Kampi/KiCad/3D/Coilcraft/XFL4020.stp

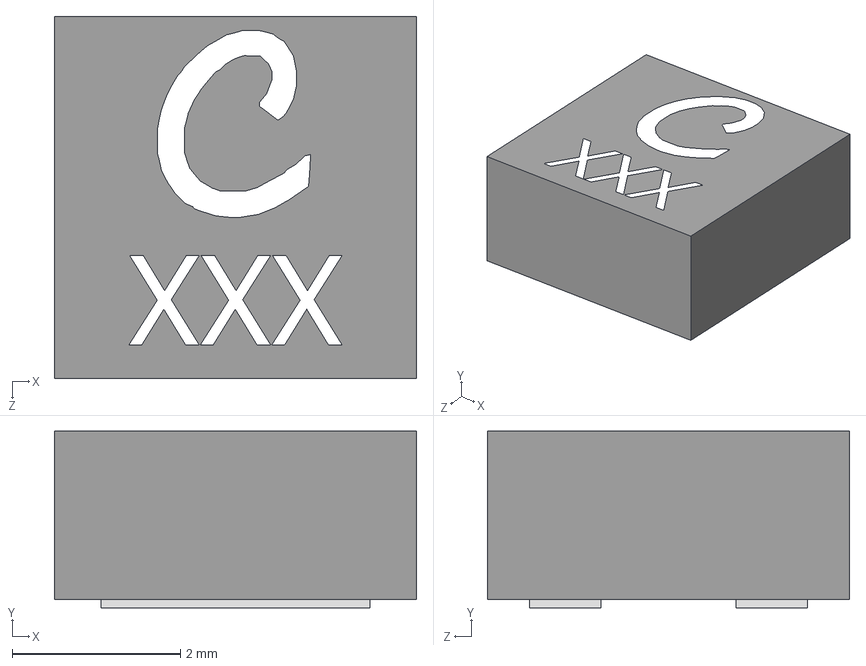
[picture p15: CAD file, 2021-03-04]
3D/Coilcraft/XFL4020.stp
4.30 x 2.10 x 4.30 mm
