Kampi/KiCad/3D/Connector_254/preci-dip/8fm-38-0006-02-146.stp

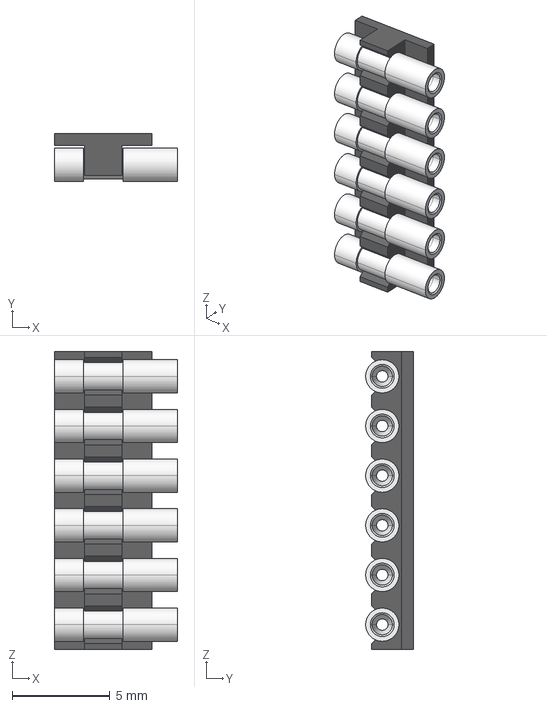
[picture p16: CAD file, 2020-06-16]
3D/Connector_254/preci-dip/8fm-38-0006-02-146.stp
6.30 x 2.44 x 15.2 mm
