Kampi/KiCad/3D/Connector_Audio/QingPu/PJ398SM_S_pin_centered.stp

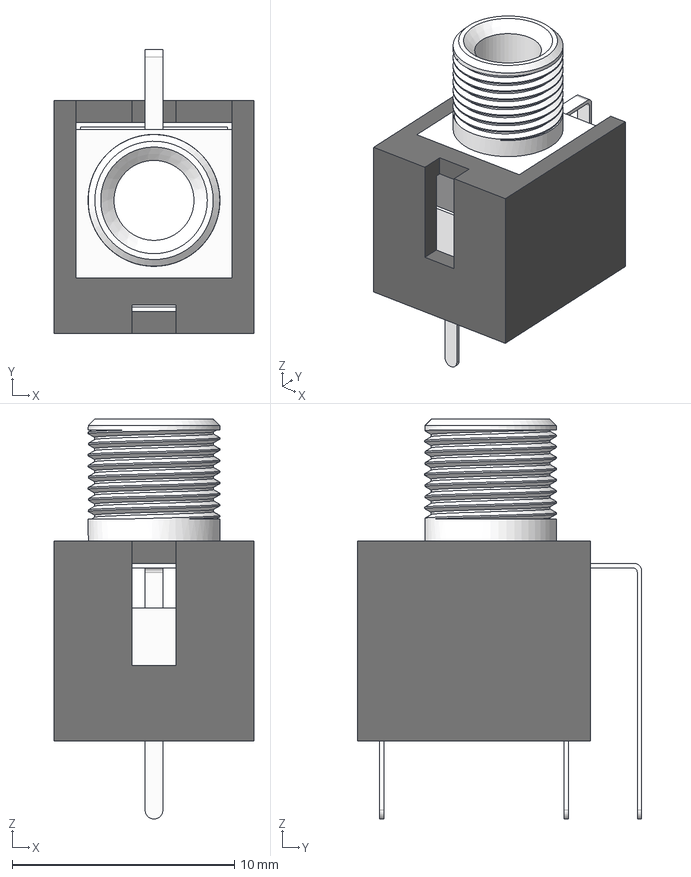
[picture p17: CAD file, 2020-06-21]
3D/Connector_Audio/QingPu/PJ398SM_S_pin_centered.stp
9.00 x 12.8 x 18.0 mm
