Kampi/KiCad/3D/Connector_Card/Hirose/DM3AT-SF-PEJM5.stp

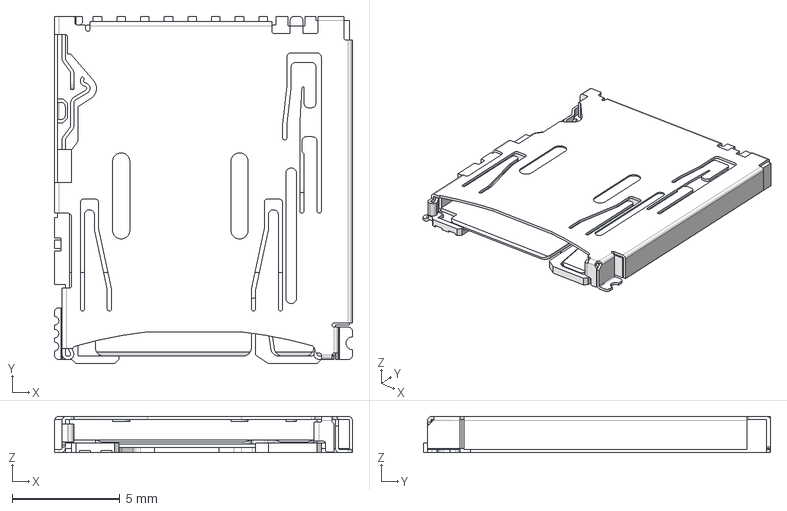
[picture p18: CAD file, 2020-09-08]
3D/Connector_Card/Hirose/DM3AT-SF-PEJM5.stp
13.8 x 16.2 x 1.68 mm
