Kampi/KiCad/3D/Connector_CUI/CUI_DEVICES_UJC-HP-3-SMT-TR.stp

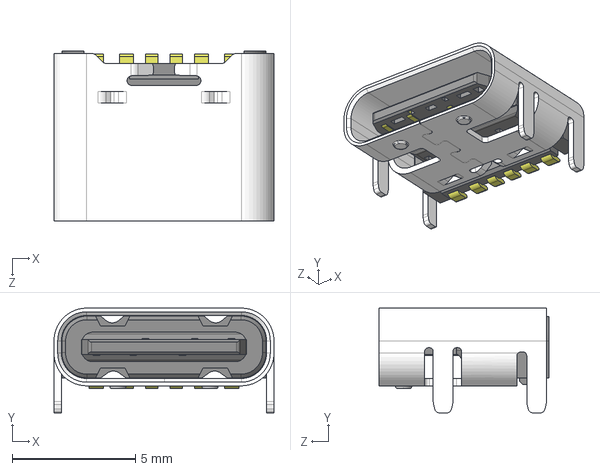
[picture p19: CAD file, 2020-06-03]
3D/Connector_CUI/CUI_DEVICES_UJC-HP-3-SMT-TR.stp
8.94 x 4.26 x 6.90 mm
