Kampi/KiCad/3D/Connector_IDC/Socket Male 10pin Straight THT Goldplated 2_54mm.stp

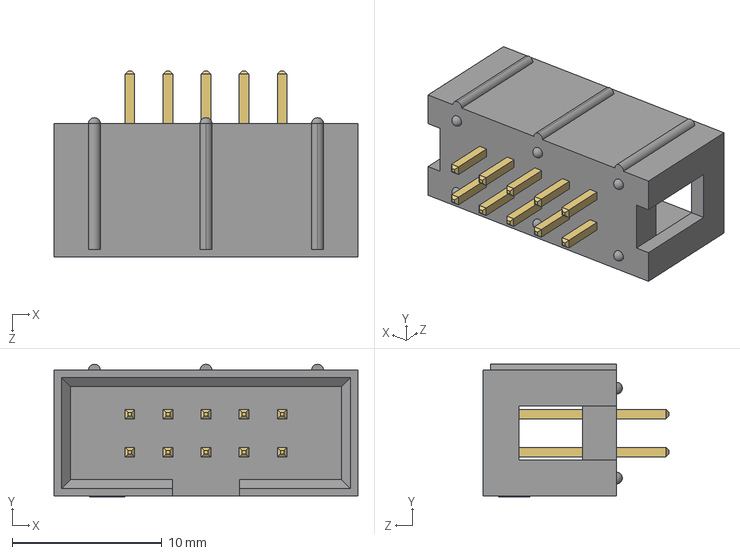
[picture p20: CAD file, 2020-06-20]
3D/Connector_IDC/Socket Male 10pin Straight THT Goldplated 2_54mm.stp
20.3 x 8.85 x 12.4 mm
