Kampi/KiCad/3D/Connector_JST/S6B-PH-SM4-TB.stp

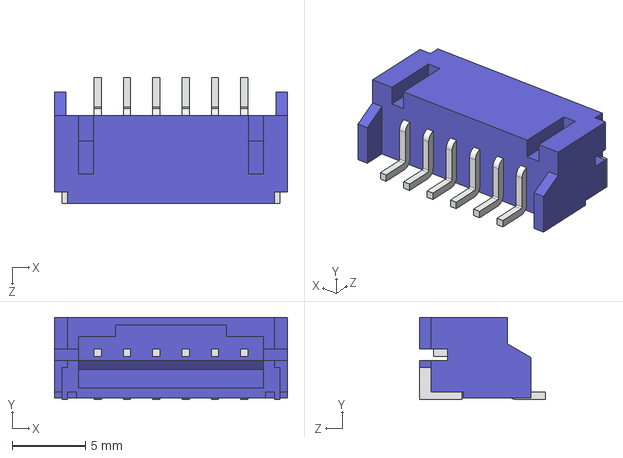
[picture p21: CAD file, 2022-03-19]
3D/Connector_JST/S6B-PH-SM4-TB.stp
15.9 x 5.60 x 8.60 mm
