Kampi/KiCad/3D/Connector_MiniDIN/TE Connectivity/c-5749231-1-o-3d.stp

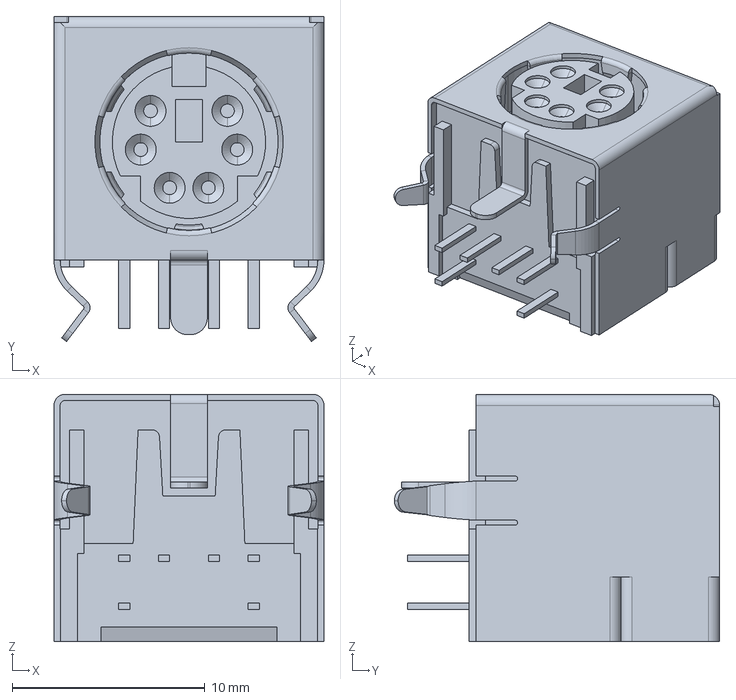
[picture p22: CAD file, 2019-10-17]
3D/Connector_MiniDIN/TE Connectivity/c-5749231-1-o-3d.stp
14.0 x 16.9 x 12.8 mm
