Kampi/KiCad/3D/Connector_Phoenix/PhoenixContact_MPT_0,5_4-4-2,54.stp

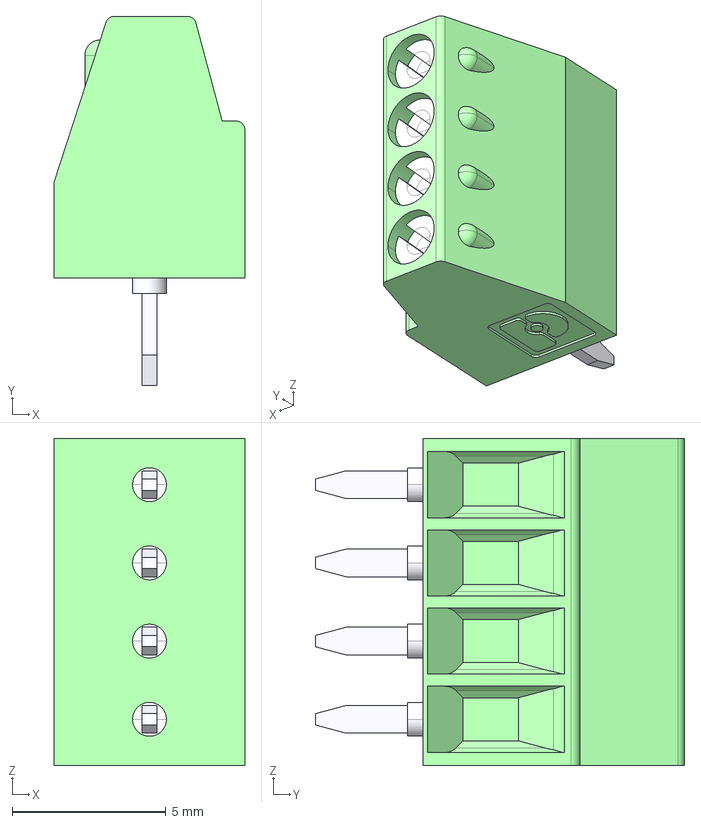
[picture p23: CAD file, 2020-06-03]
3D/Connector_Phoenix/PhoenixContact_MPT_0,5_4-4-2,54.stp
6.20 x 12.0 x 10.6 mm
