Kampi/KiCad/3D/Connector_USB/GCT/USB4110GFA.stp

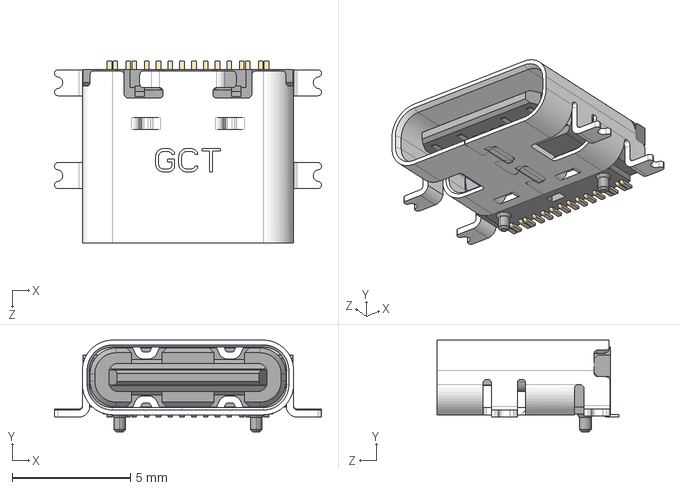
[picture p24: CAD file, 2026-01-24]
3D/Connector_USB/GCT/USB4110GFA.stp
11.3 x 3.89 x 7.70 mm
