Kampi/KiCad/3D/Connector_USB/TE Connectivity/c-292304-2-b-3d.stp

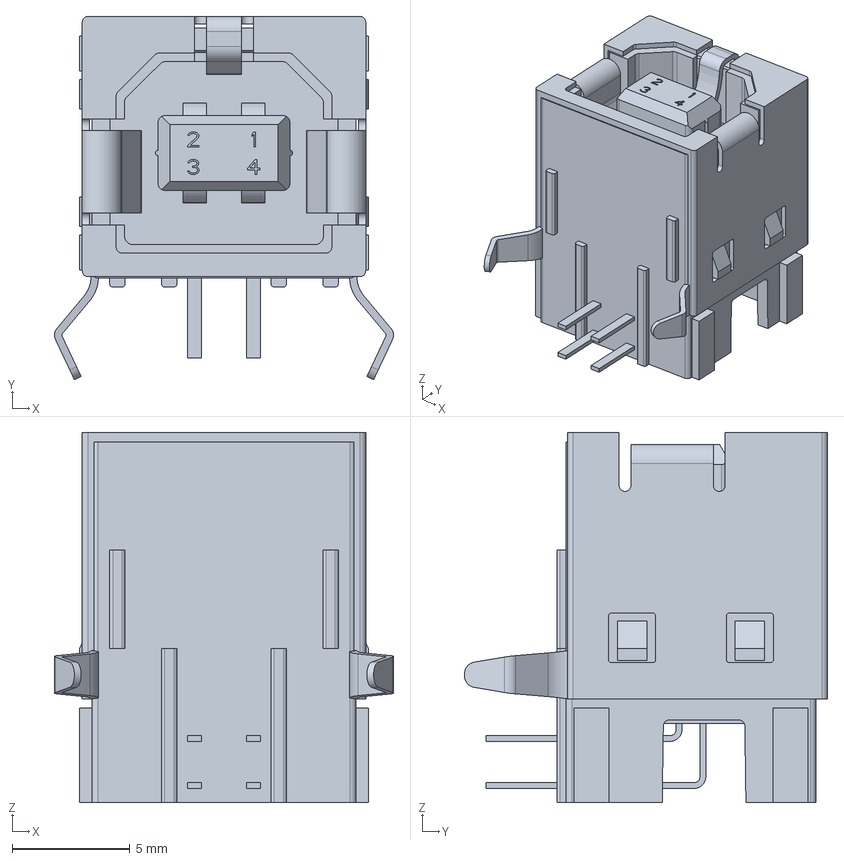
[picture p25: CAD file, 2019-10-16]
3D/Connector_USB/TE Connectivity/c-292304-2-b-3d.stp
14.4 x 15.4 x 15.7 mm
