Kampi/KiCad/3D/Cree/XLamp XP-G3.stp

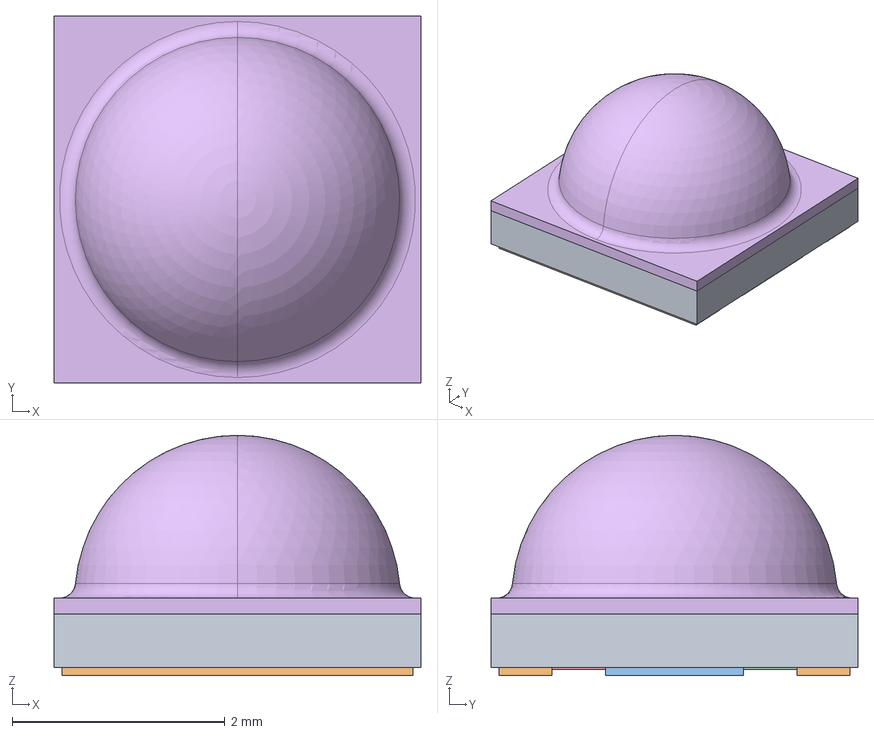
[picture p26: CAD file, 2026-01-24]
3D/Cree/XLamp XP-G3.stp
3.45 x 3.45 x 2.26 mm
2500-00565C
2500-00565C-BT
2500-00565C-SBN
2500-00565C-SB
2610-00066-DOME
