Kampi/KiCad/3D/Crystal/1612.stp

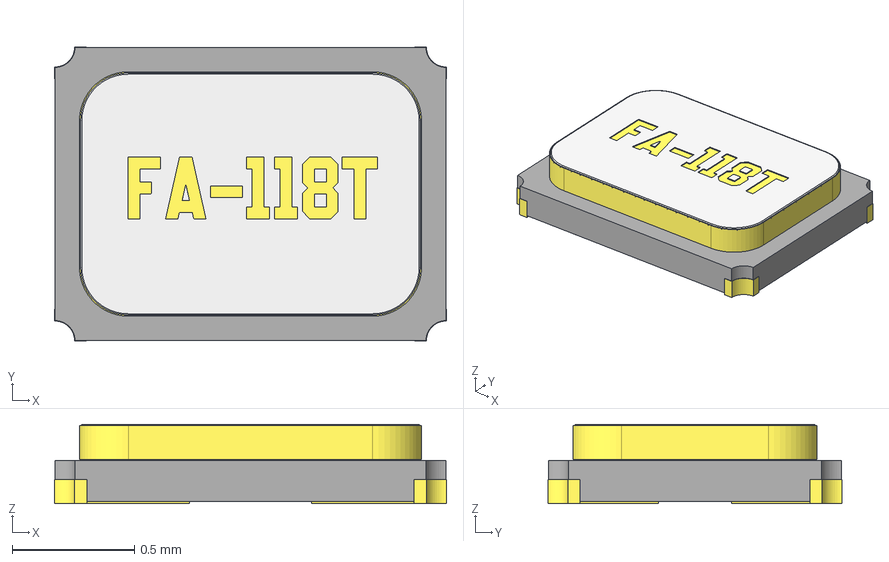
[picture p27: CAD file, 2024-10-24]
3D/Crystal/1612.stp
1.60 x 1.20 x 0.325 mm
TxT
Pin
Pin001
Pin002
Pin003
Pin004
