Kampi/KiCad/3D/Crystal/Abracon/ABS07L.stp

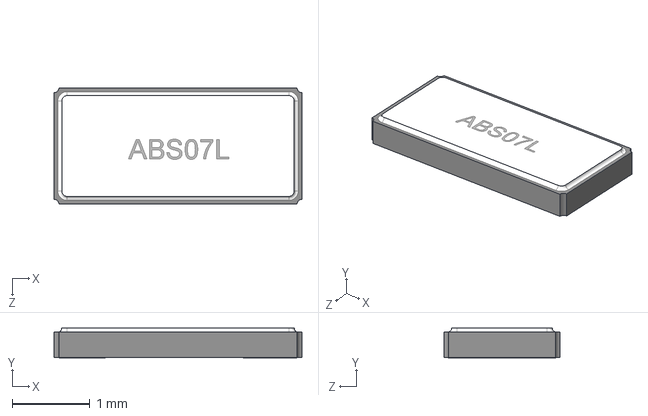
[picture p28: CAD file, 2020-09-11]
3D/Crystal/Abracon/ABS07L.stp
3.20 x 0.383 x 1.50 mm
