Kampi/KiCad/3D/CUI Devices/CMT-322-65-SMT-TR.stp

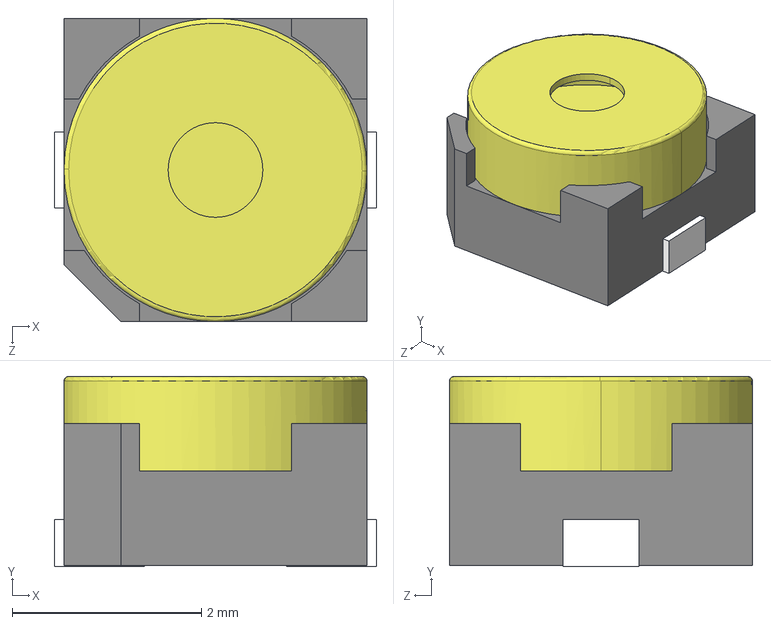
[picture p29: CAD file, 2023-12-06]
3D/CUI Devices/CMT-322-65-SMT-TR.stp
3.40 x 2.01 x 3.20 mm
