Kampi/KiCad/3D/DevBoards/Digilent/PmodOLED.stp

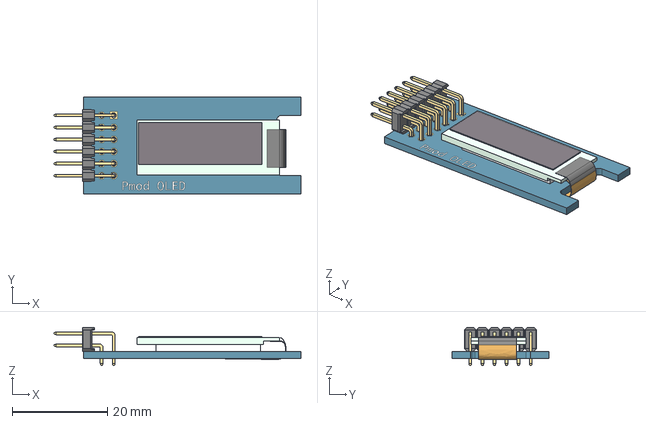
[picture p30: CAD file, 2020-05-07]
3D/DevBoards/Digilent/PmodOLED.stp
51.9 x 20.3 x 8.08 mm
