Kampi/KiCad/3D/DevBoards/Particle/Xenon.stp

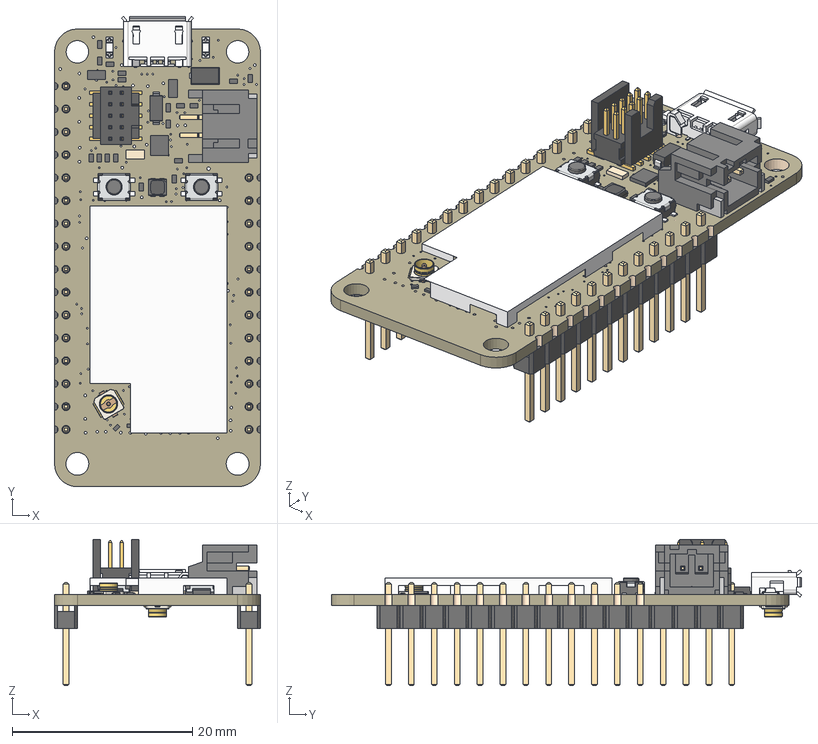
[picture p31: CAD file, 2020-05-14]
3D/DevBoards/Particle/Xenon.stp
22.9 x 52.2 x 16.3 mm
Board
_FTSH_105_01_L_DV_K_body_2
_FTSH_105_01_L_DV_K_pins1_4
_FTSH_105_01_L_DV_K_pins2_6
pin x 2
mount x 2
housing
switch v1 x 2
LED_CLVBA-FKA v1
uFL x 2
MBR120
MICRO_led (1) x 2
microUSB
DO-220AA SMP v1
0402-resistor v2 x 18
xenon-rf-shield-v002 v6
capacitor-smd v2
capacitor-smd v2 (1) x 2
ic
0402-resistor v2 (1) x 2
spacer (1) x 16
pin (1) x 16
spacer (1) (1) x 12
pin (1) (1) x 12
