Kampi/KiCad/3D/Display/LCD-320x240.step

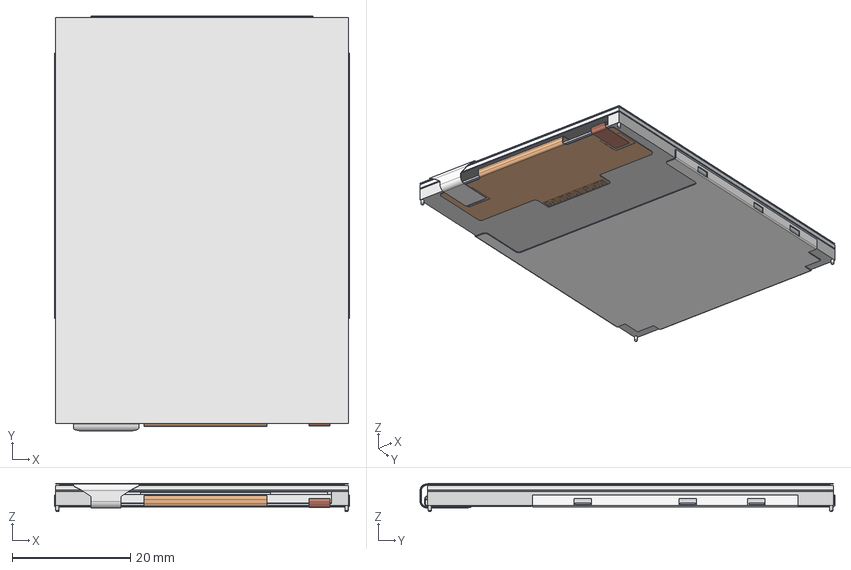
[picture p32: CAD file, 2026-01-24]
3D/Display/LCD-320x240.step
50.1 x 70.3 x 4.77 mm
frame
metal bandage
light_shelf
main_shelf
tft_matrix
tft_board
screen_film
screen_glass
touch_routs
touch_protect
touch_cable_contacts
touch_cable_film
