Kampi/KiCad/3D/Display/SevenSegment/Kingbright/SA23-11.stp

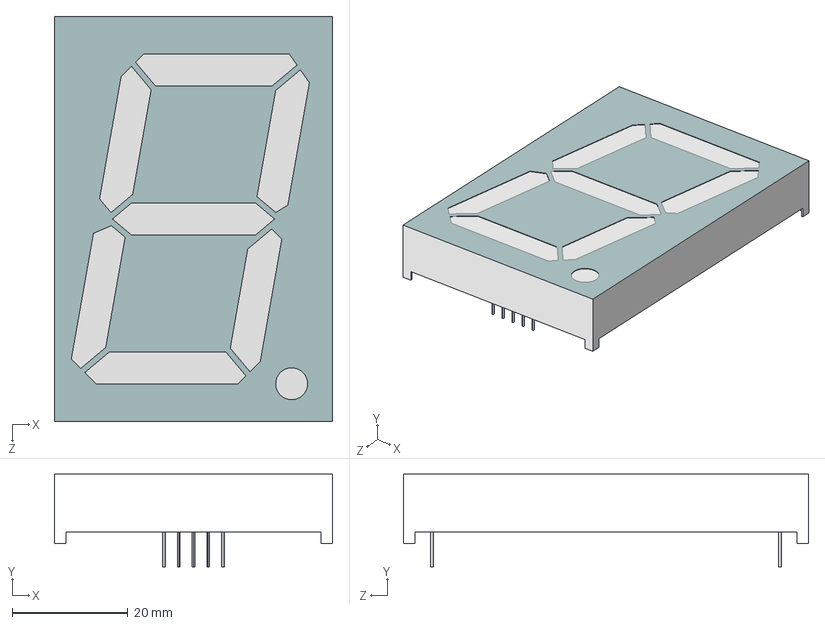
[picture p33: CAD file, 2020-06-30]
3D/Display/SevenSegment/Kingbright/SA23-11.stp
48.0 x 16.0 x 70.0 mm
