Kampi/KiCad/3D/E-Switch/TL3305.stp

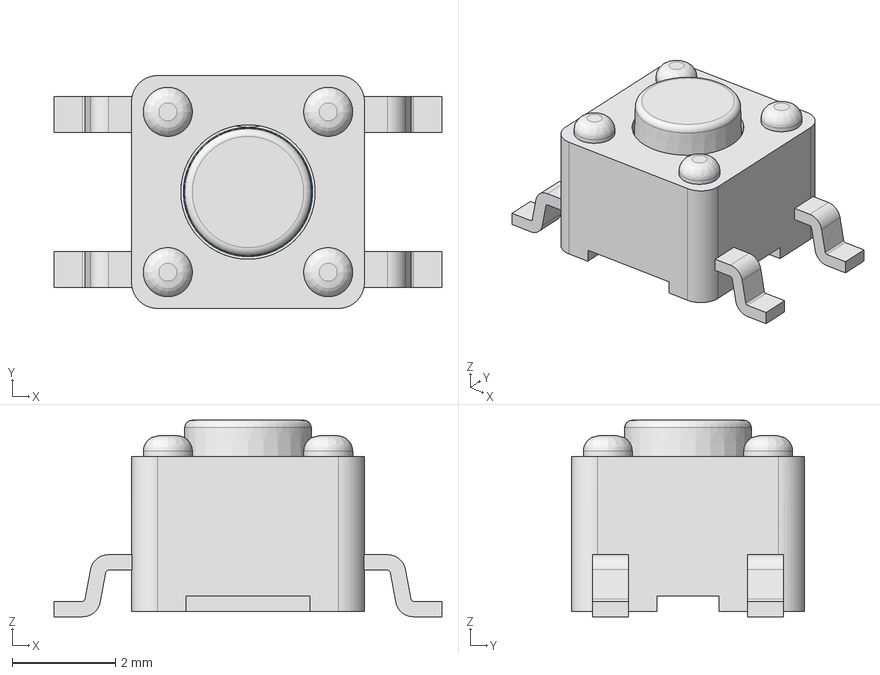
[picture p34: CAD file, 2026-01-24]
3D/E-Switch/TL3305.stp
7.50 x 4.50 x 3.80 mm
