Kampi/KiCad/3D/EastRising/ER-CON0.4-24P.stp

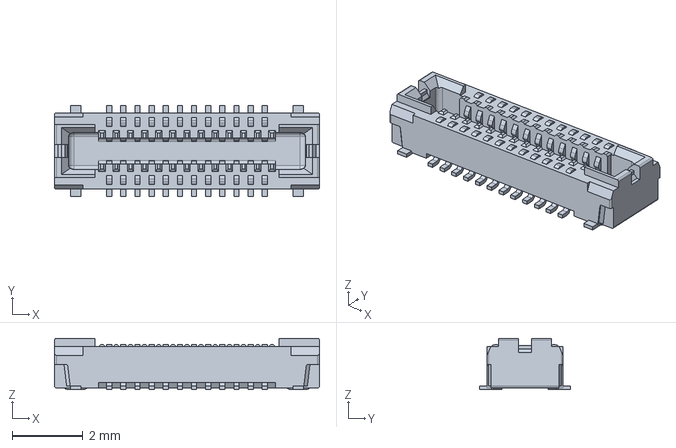
[picture p35: CAD file, 2023-08-20]
3D/EastRising/ER-CON0.4-24P.stp
7.50 x 2.58 x 1.45 mm
