Kampi/KiCad/3D/ECS/ECS-100-18-30B-AGN-TR.stp

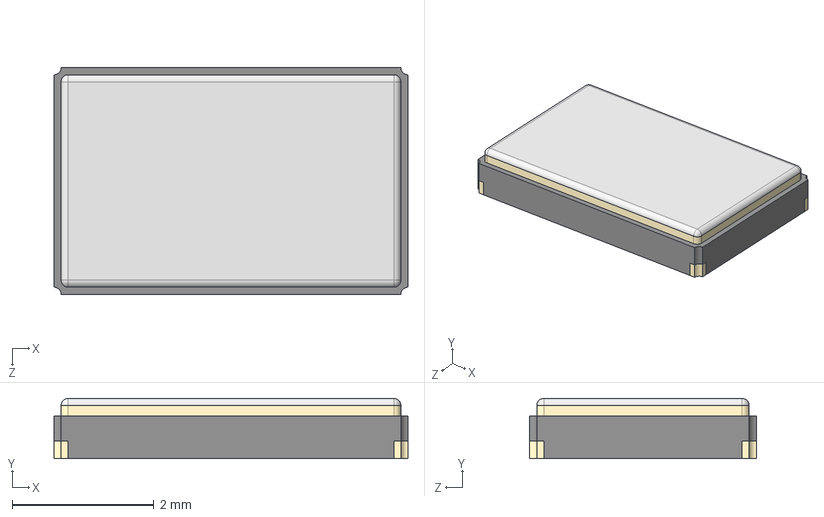
[picture p36: CAD file, 2026-07-22]
3D/ECS/ECS-100-18-30B-AGN-TR.stp
5.00 x 0.85 x 3.20 mm
