Kampi/KiCad/3D/Espressif/ESP32-C3-WROOM-02-H4.stp

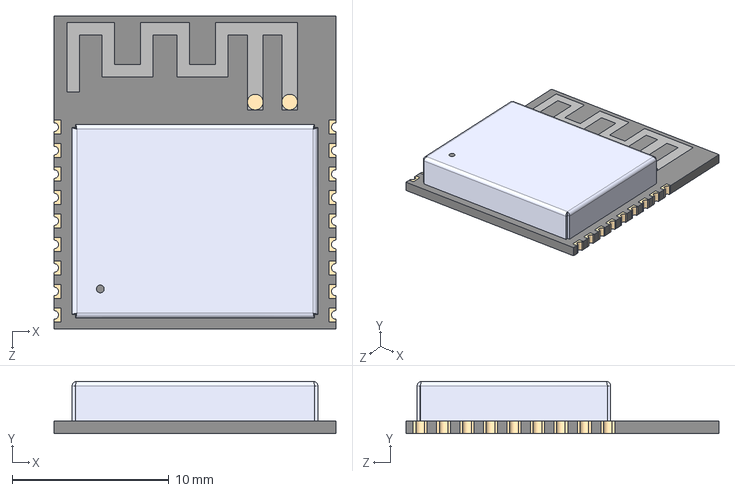
[picture p37: CAD file, 2022-07-02]
3D/Espressif/ESP32-C3-WROOM-02-H4.stp
18.0 x 3.35 x 20.0 mm
