Kampi/KiCad/3D/Fibocom/G510.stp

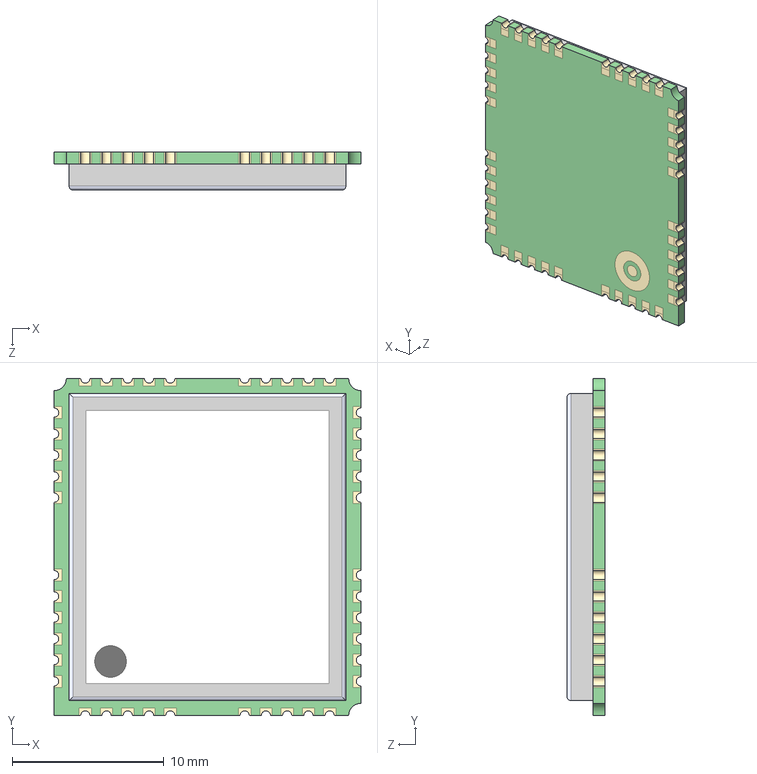
[picture p39: CAD file, 2021-02-05]
3D/Fibocom/G510.stp
20.2 x 22.2 x 2.50 mm
