Kampi/KiCad/3D/FTDI/FT231XS.stp

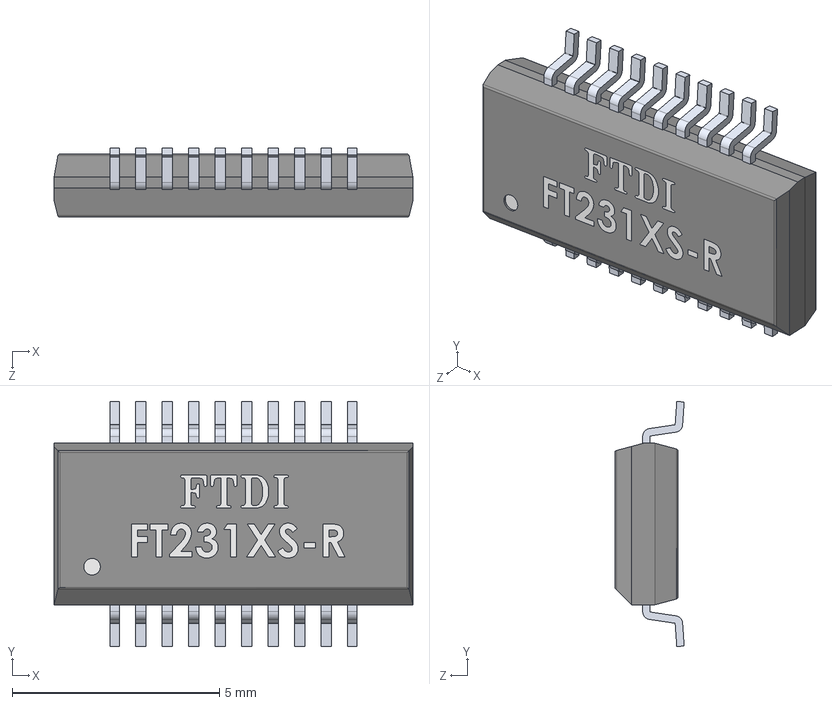
[picture p40: CAD file, 2022-09-24]
3D/FTDI/FT231XS.stp
8.66 x 5.91 x 1.67 mm
