Kampi/KiCad/3D/Fuse/5x20.stp

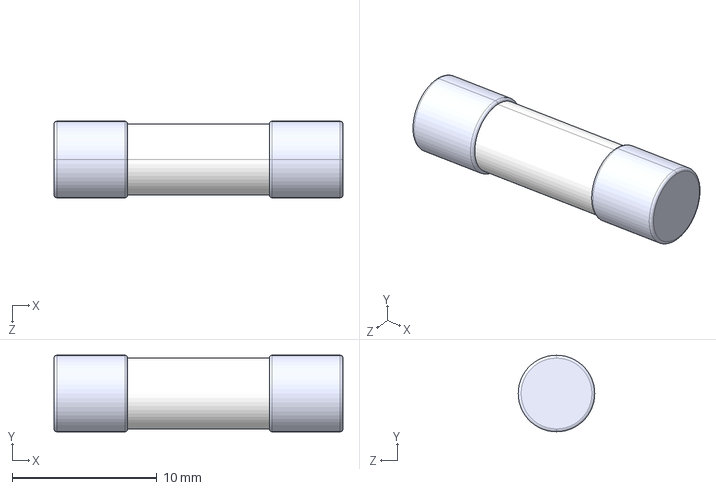
[picture p41: CAD file, 2026-05-04]
3D/Fuse/5x20.stp
20.0 x 5.30 x 5.30 mm
