Kampi/KiCad/3D/GCT/USB4120-03-C.stp

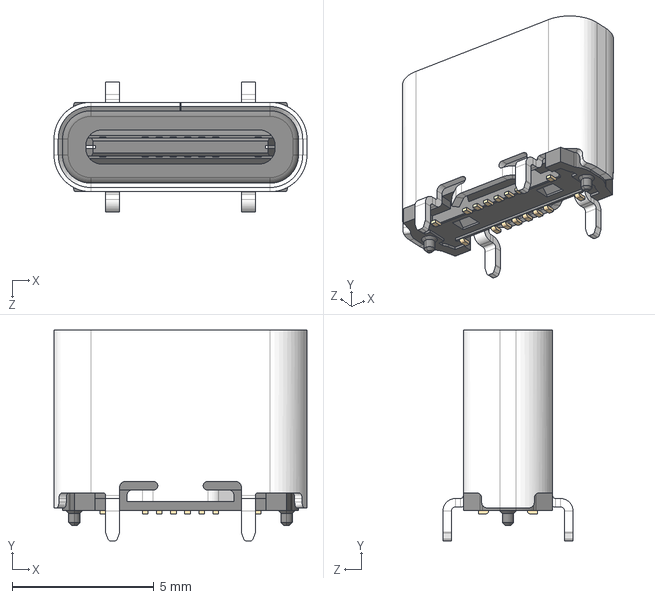
[picture p42: CAD file, 2026-05-06]
3D/GCT/USB4120-03-C.stp
8.94 x 7.45 x 4.60 mm
