Kampi/KiCad/3D/GlobTek Inc/PLUG-USBC-241SMT-TH-4BC2LS.stp

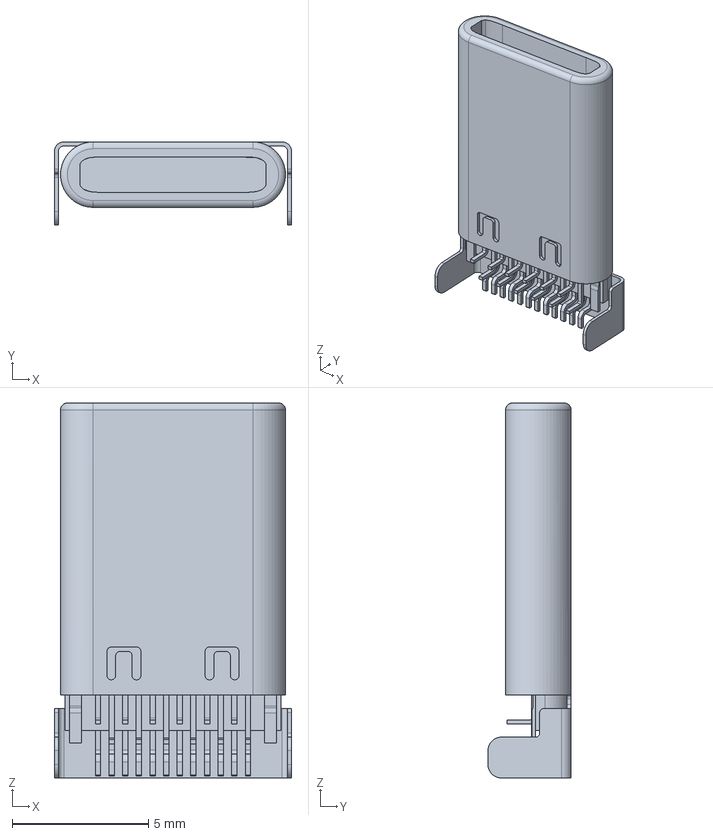
[picture p43: CAD file, 2026-01-24]
3D/GlobTek Inc/PLUG-USBC-241SMT-TH-4BC2LS.stp
8.70 x 3.05 x 13.8 mm
