Kampi/KiCad/3D/Hirose/DM3BT-DSF-PEJS.stp

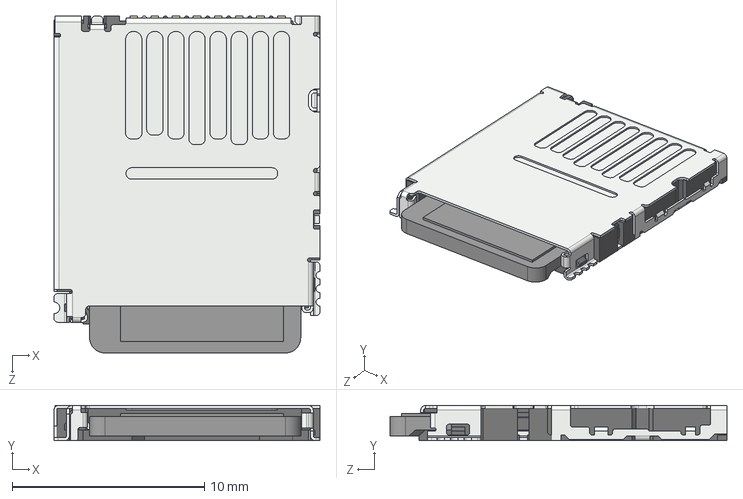
[picture p44: CAD file, 2026-01-24]
3D/Hirose/DM3BT-DSF-PEJS.stp
13.9 x 1.83 x 17.6 mm
CARD
DM3BT
