Kampi/KiCad/3D/HopeRF/RFM95.stp

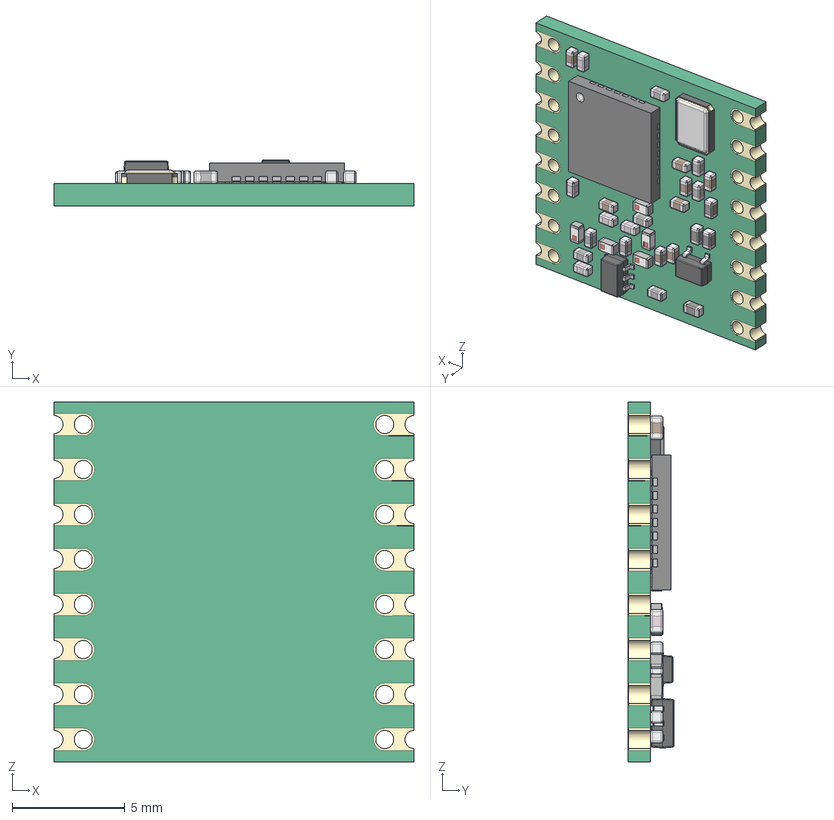
[picture p45: CAD file, 2021-02-05]
3D/HopeRF/RFM95.stp
16.0 x 2.04 x 16.0 mm
QFN 28
SMD Crystal
CAP 0403 x 8
CAP Ceramic 0403 x 8
Res 0403 x 4
CAP ML 0403 x 5
SOT-323
Inductor SMD 0403 x 5
SOT-363
