Kampi/KiCad/3D/Ignion/NN02-101.stp

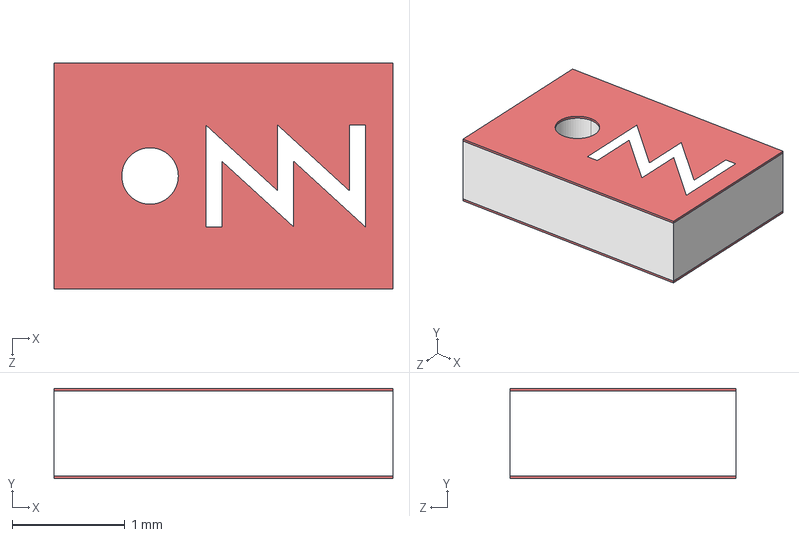
[picture p46: CAD file, 2026-01-24]
3D/Ignion/NN02-101.stp
3.00 x 0.8 x 2.00 mm
