Kampi/KiCad/3D/IMST/WiMOD_iM871A.stp

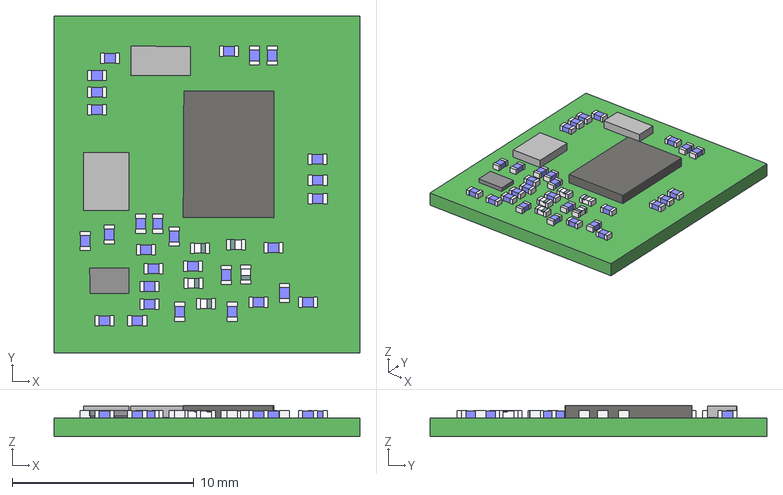
[picture p47: CAD file, 2026-06-22]
3D/IMST/WiMOD_iM871A.stp
16.8 x 18.5 x 1.73 mm
Board
Extruded x 111
