Kampi/KiCad/3D/Inductor/Murata/LQH3NPN2R2MJRL.stp

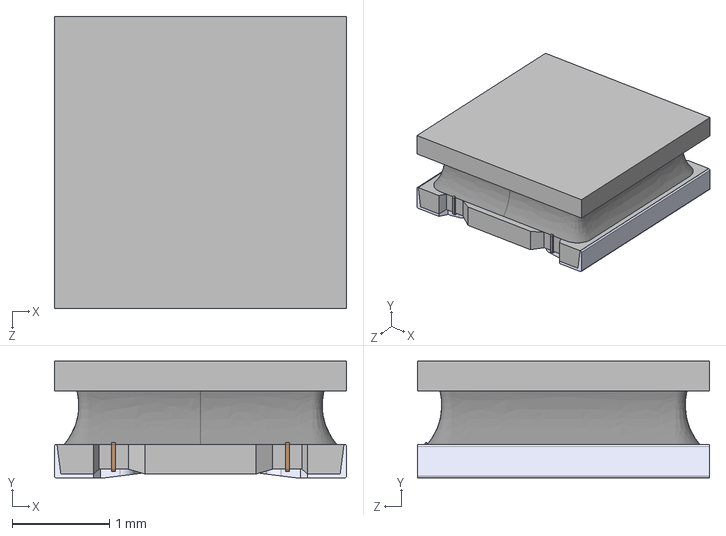
[picture p48: CAD file, 2021-05-16]
3D/Inductor/Murata/LQH3NPN2R2MJRL.stp
3.00 x 1.20 x 3.00 mm
