Kampi/KiCad/3D/Inductor/Taiyo Yuden/NR6028.stp

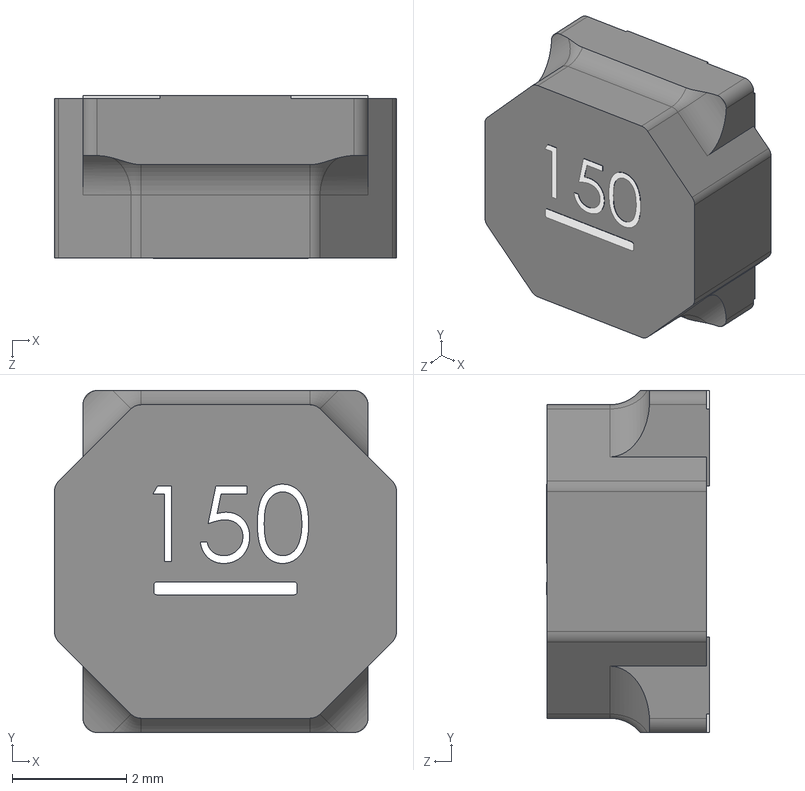
[picture p49: CAD file, 2021-11-06]
3D/Inductor/Taiyo Yuden/NR6028.stp
6.00 x 6.00 x 2.86 mm
