Kampi/KiCad/3D/Infineon/2EDN7534FXTMA1.stp

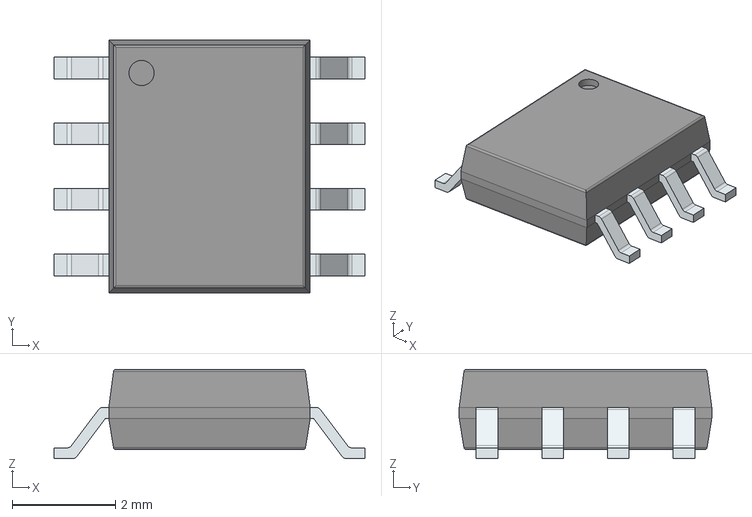
[picture p50: CAD file, 2026-01-24]
3D/Infineon/2EDN7534FXTMA1.stp
6.02 x 4.89 x 1.73 mm
PinsArrayLR
