Kampi/KiCad/3D/IR_Receiver/Vishay/TSOP283.stp

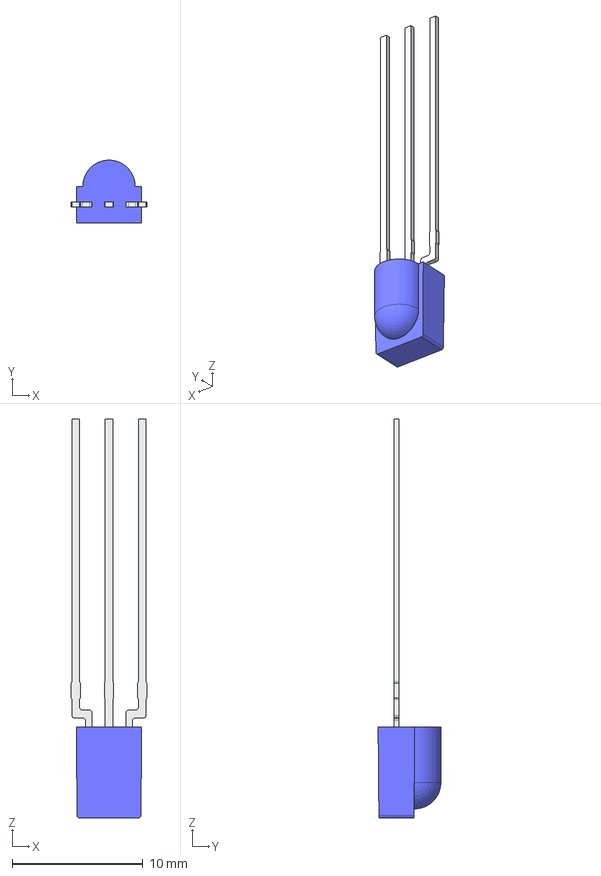
[picture p51: CAD file, 2020-09-07]
3D/IR_Receiver/Vishay/TSOP283.stp
5.78 x 4.80 x 30.5 mm
GO-100187
GO-100187.01
