Kampi/KiCad/3D/JST/B2B-PH-SM4-TB.stp

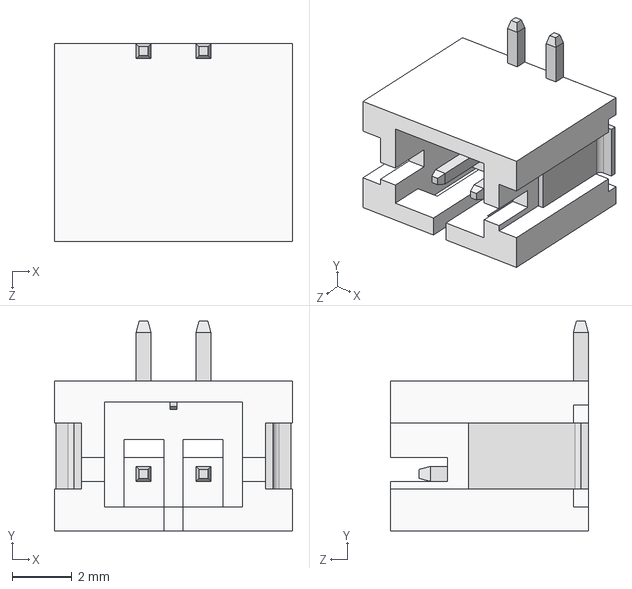
[picture p52: CAD file, 2026-01-24]
3D/JST/B2B-PH-SM4-TB.stp
7.95 x 7.00 x 6.60 mm
