Kampi/KiCad/3D/Kemet/P410QM223M300AH101.stp

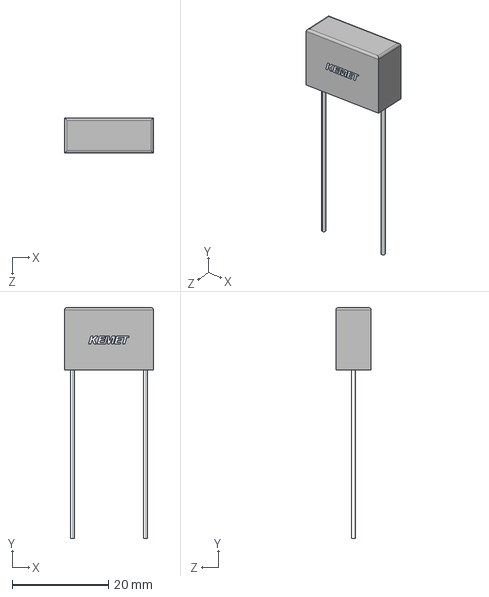
[picture p53: CAD file, 2024-10-24]
3D/Kemet/P410QM223M300AH101.stp
18.5 x 48.0 x 7.30 mm
