Kampi/KiCad/3D/Keystone/3030KTR.stp

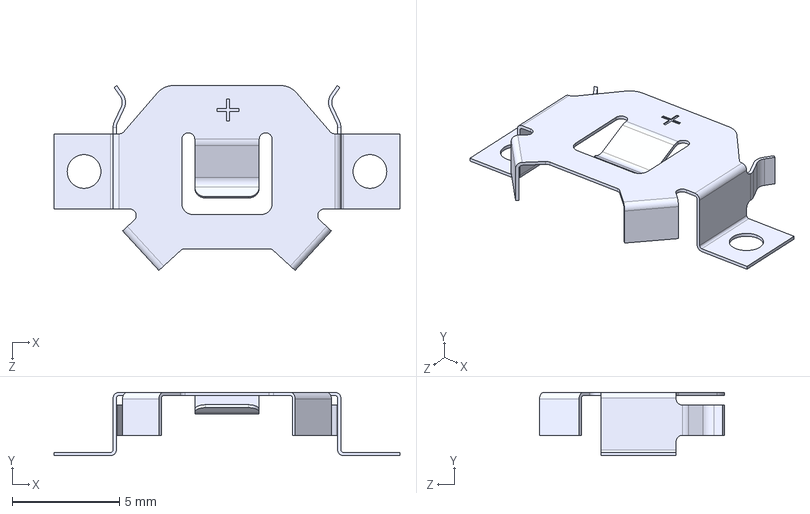
[picture p54: CAD file, 2026-08-02]
3D/Keystone/3030KTR.stp
16.1 x 2.95 x 8.61 mm
