Kampi/KiCad/3D/Knowles/SPK0641HT4H.stp

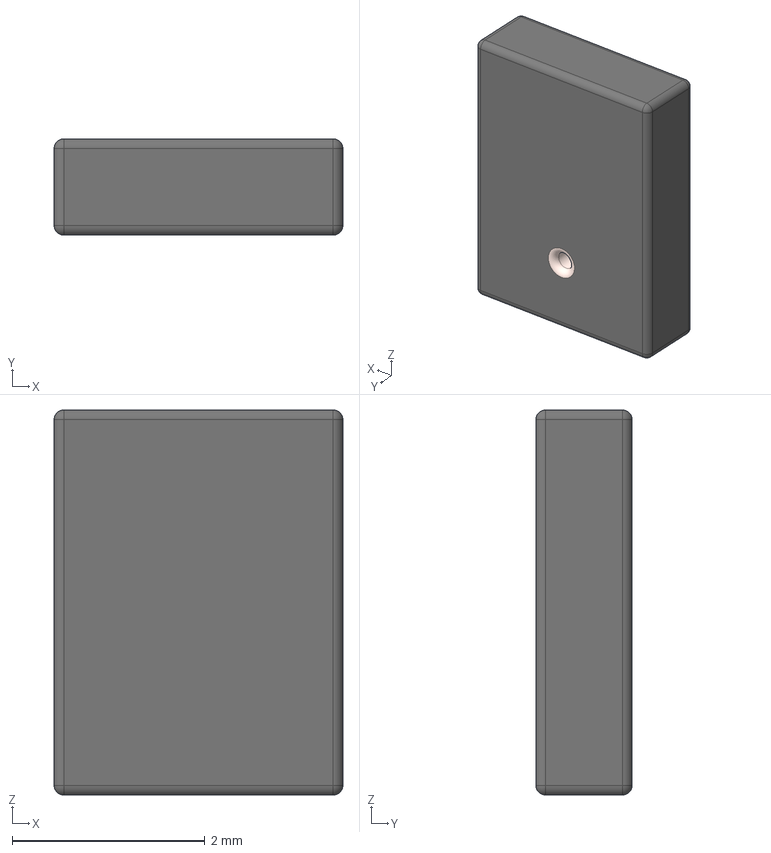
[picture p55: CAD file, 2024-02-06]
3D/Knowles/SPK0641HT4H.stp
3.00 x 1.00 x 4.00 mm
