Kampi/KiCad/3D/Kyocera/9296-POKE-HOME-CONNECTOR.step

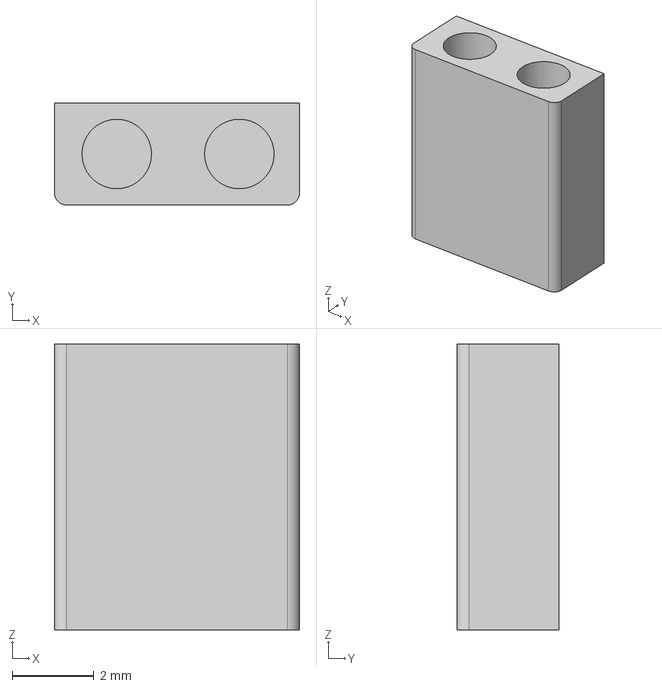
[picture p56: CAD file, 2026-02-19]
3D/Kyocera/9296-POKE-HOME-CONNECTOR.step
6.00 x 2.50 x 7.00 mm
