Kampi/KiCad/3D/LED/Cree/CLMVC-FKC.stp

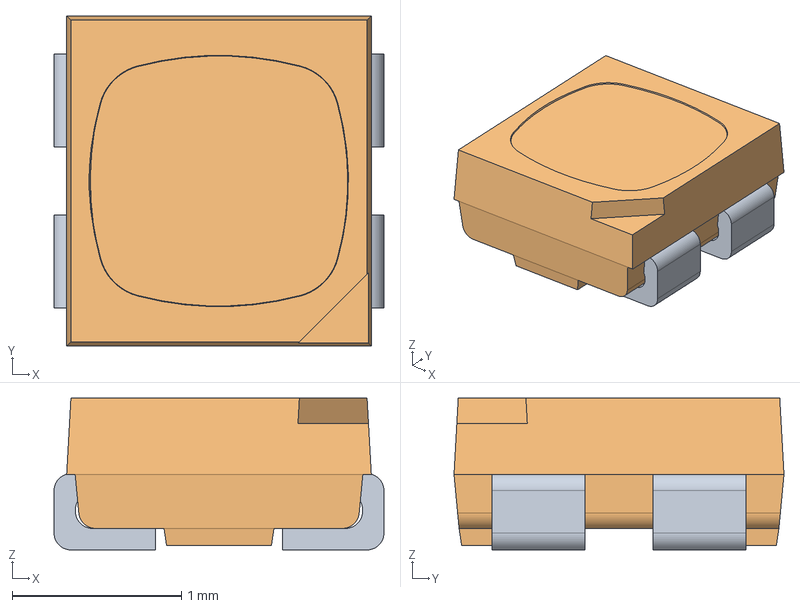
[picture p57: CAD file, 2021-08-19]
3D/LED/Cree/CLMVC-FKC.stp
1.95 x 1.95 x 0.897 mm
PRT0008
PRT0010
