Kampi/KiCad/3D/LED/Inolux/IN-3531SCUV.stp

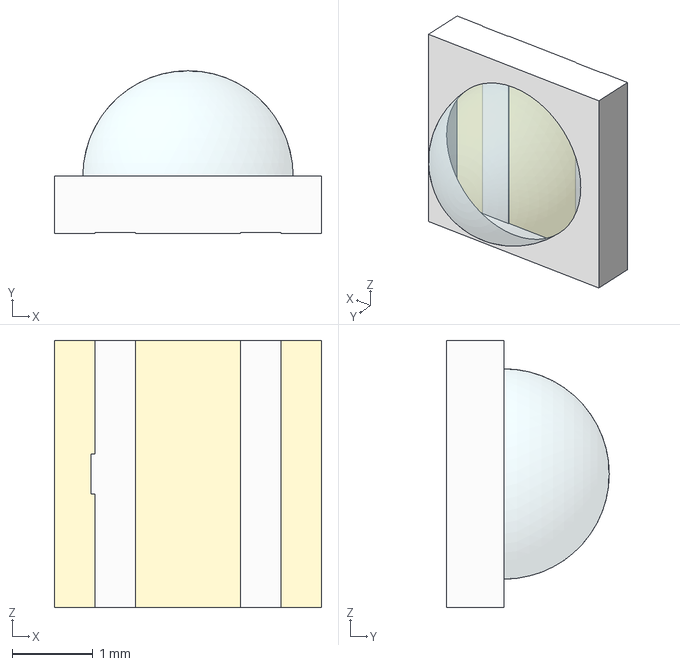
[picture p58: CAD file, 2020-06-16]
3D/LED/Inolux/IN-3531SCUV.stp
3.30 x 2.01 x 3.30 mm
