Kampi/KiCad/3D/LED/OSRAM Opto Semiconductors/SFH_4257.stp

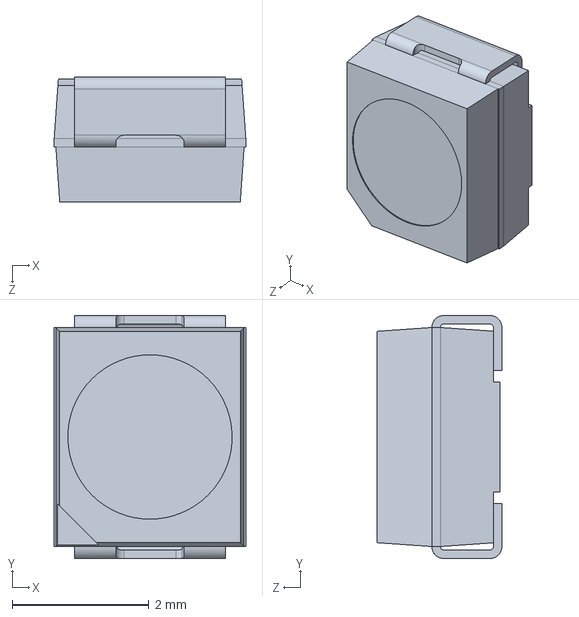
[picture p59: CAD file, 2021-05-16]
3D/LED/OSRAM Opto Semiconductors/SFH_4257.stp
2.80 x 3.55 x 1.83 mm
