Kampi/KiCad/3D/Luxeon/LUXEON IR Domed Line 150 Deg.stp

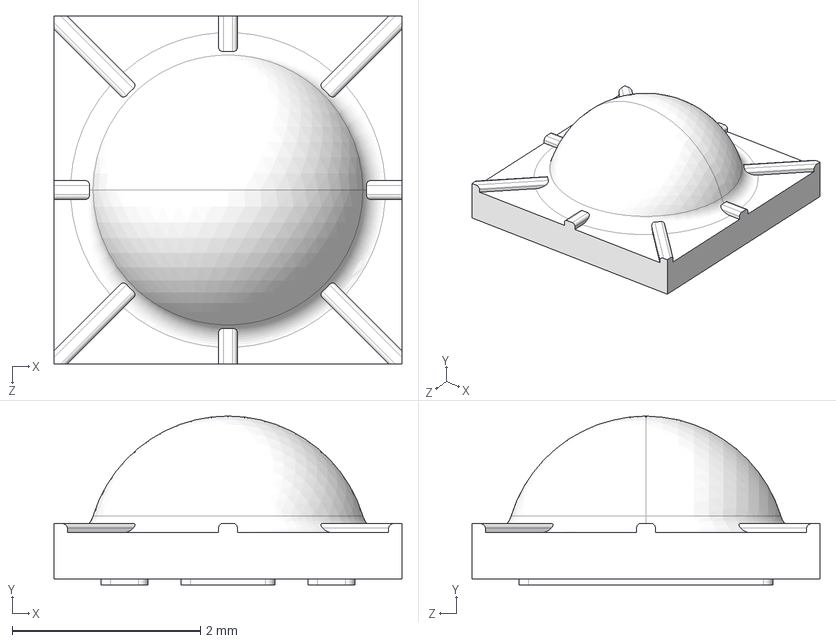
[picture p60: CAD file, 2023-01-01]
3D/Luxeon/LUXEON IR Domed Line 150 Deg.stp
3.70 x 1.80 x 3.70 mm
