Kampi/KiCad/3D/Mean Well/IRM-90-12.stp

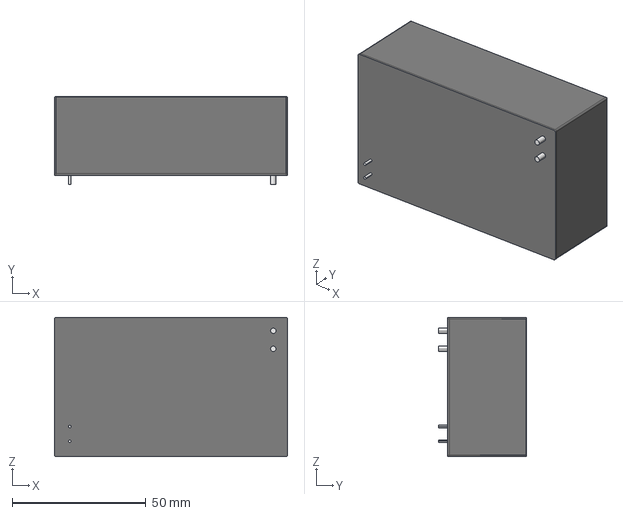
[picture p61: CAD file, 2026-07-12]
3D/Mean Well/IRM-90-12.stp
87.0 x 33.0 x 52.0 mm
