Kampi/KiCad/3D/Mechanical/Spacer/Harwin/r30-6011202.stp

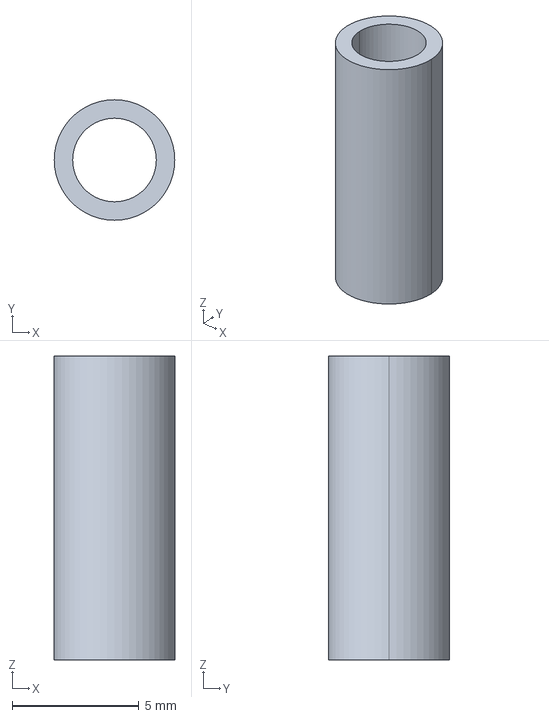
[picture p62: CAD file, 2020-07-30]
3D/Mechanical/Spacer/Harwin/r30-6011202.stp
4.76 x 4.76 x 12.0 mm
