Kampi/KiCad/3D/Micro Crystal/RV-8263-C8.stp

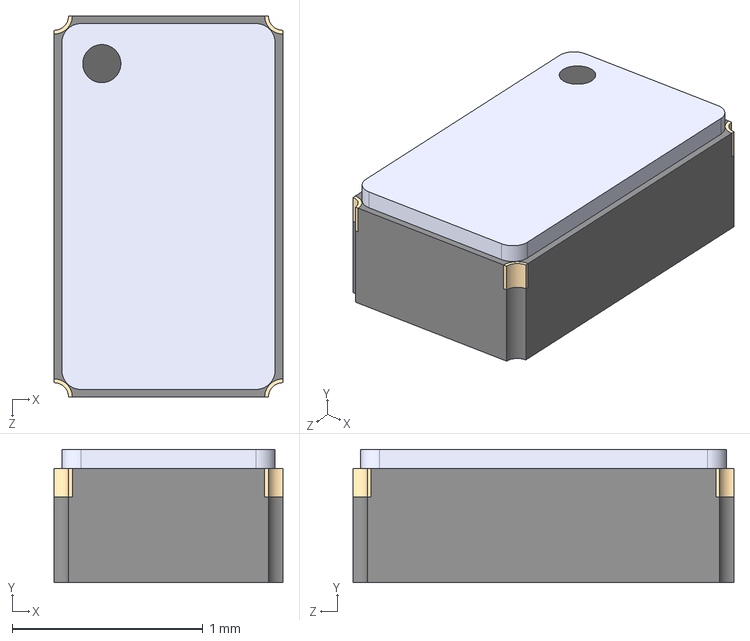
[picture p63: CAD file, 2024-06-07]
3D/Micro Crystal/RV-8263-C8.stp
1.20 x 0.7 x 2.00 mm
