Kampi/KiCad/3D/MonoliticPower/MP2182.stp

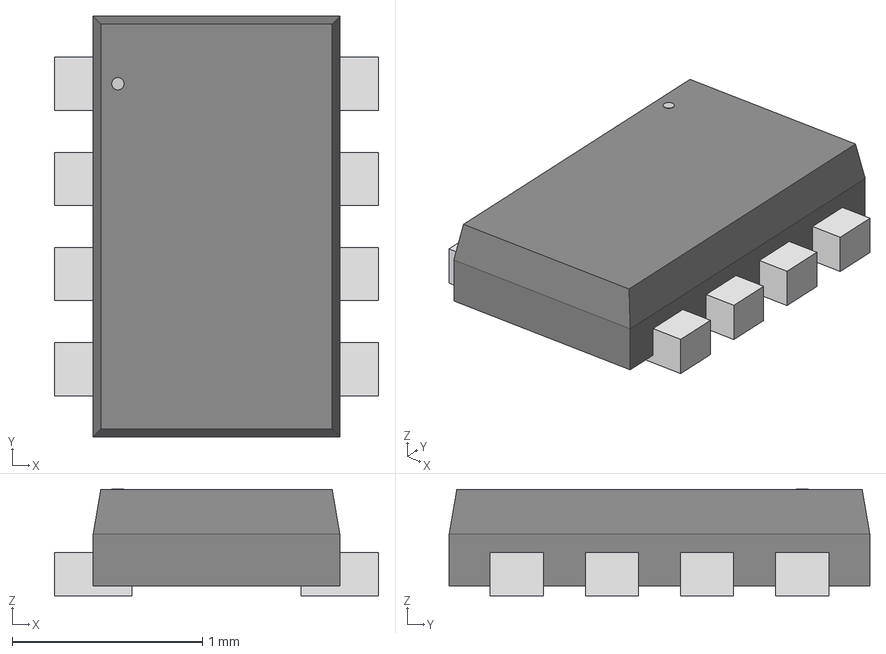
[picture p64: CAD file, 2021-03-04]
3D/MonoliticPower/MP2182.stp
1.70 x 2.21 x 0.561 mm
