Kampi/KiCad/3D/MPD/BH-18650-PC.stp

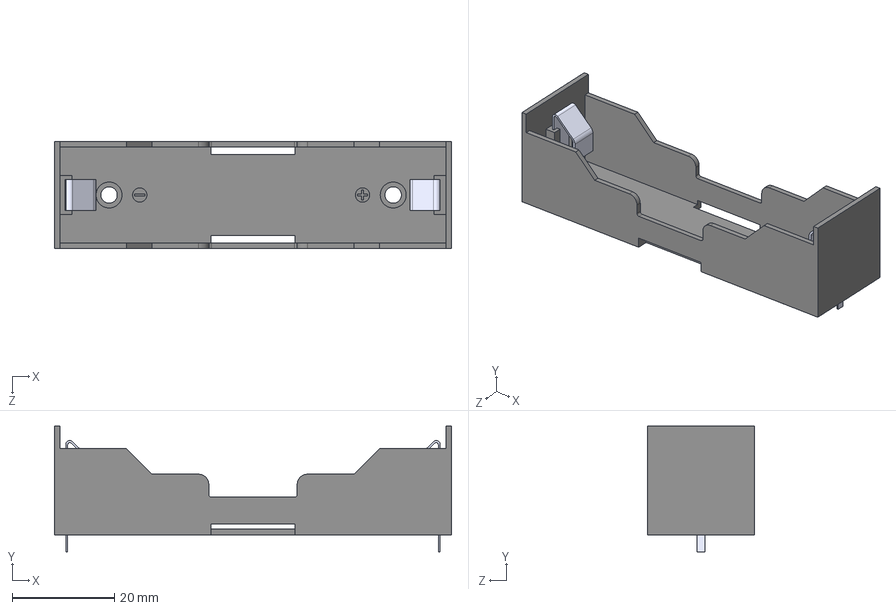
[picture p65: CAD file, 2024-09-03]
3D/MPD/BH-18650-PC.stp
77.7 x 24.6 x 20.9 mm
