Kampi/KiCad/3D/Murata/DFE2016.stp

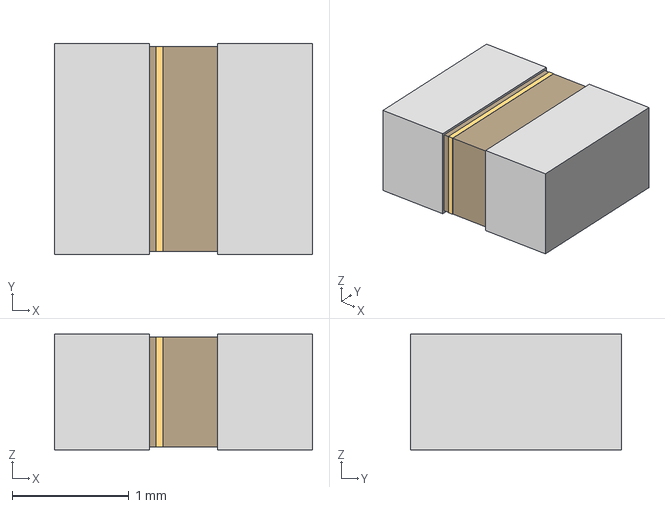
[picture p66: CAD file, 2026-01-24]
3D/Murata/DFE2016.stp
2.21 x 1.80 x 0.991 mm
