Kampi/KiCad/3D/NDK/NX2016SA_NDK.stp

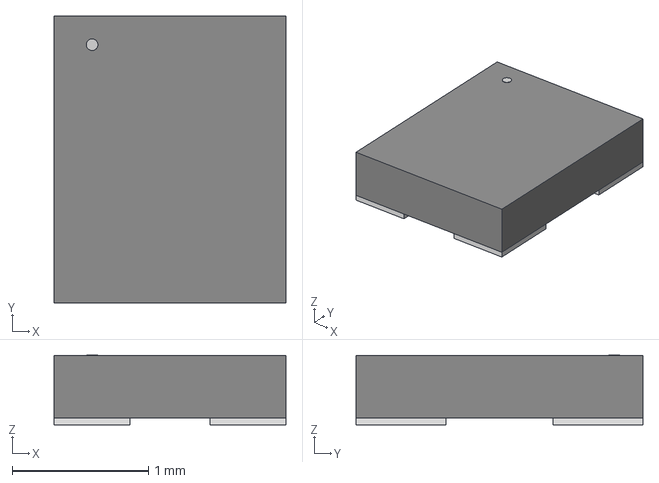
[picture p67: CAD file, 2023-09-16]
3D/NDK/NX2016SA_NDK.stp
1.70 x 2.11 x 0.511 mm
