Kampi/KiCad/3D/Nexperia/PUSB3AB4Z.stp

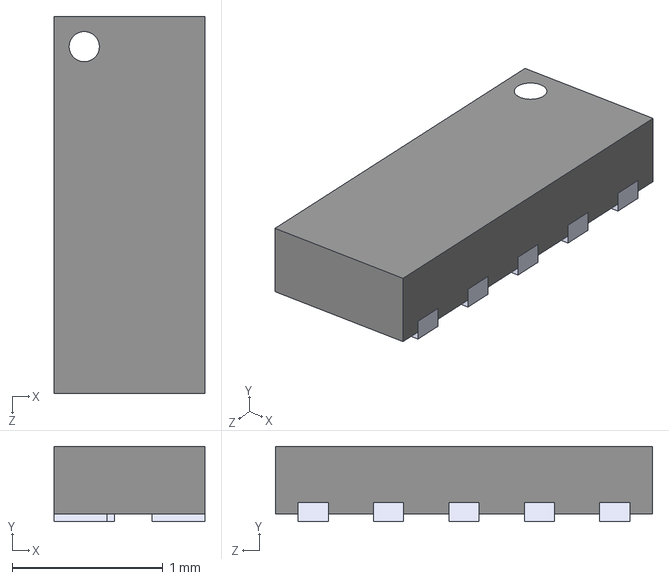
[picture p68: CAD file, 2026-01-24]
3D/Nexperia/PUSB3AB4Z.stp
1.00 x 0.5 x 2.50 mm
