Kampi/KiCad/3D/OmniVision/OV2640_WithConnector.stp

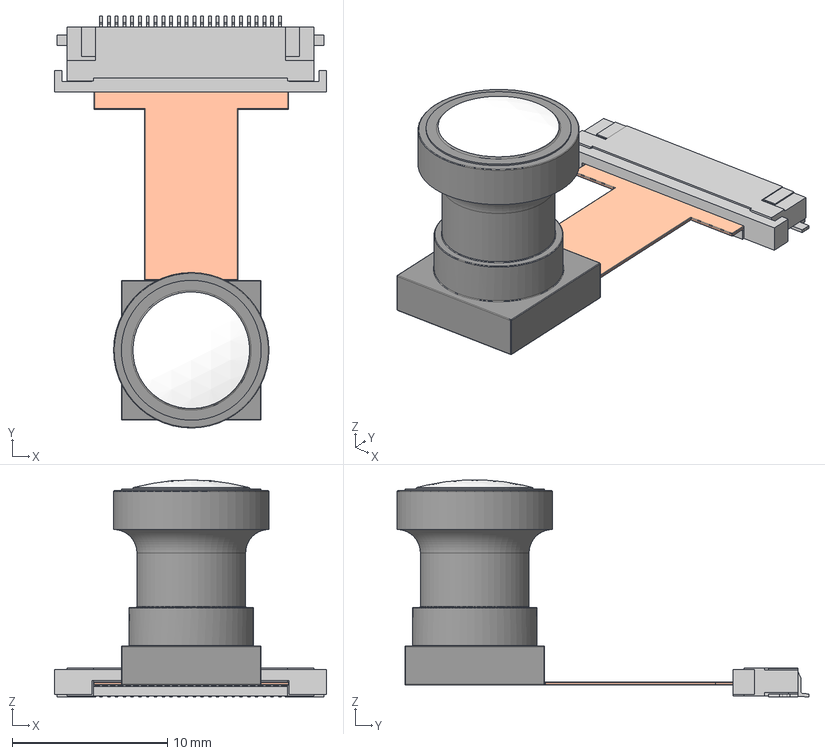
[picture p69: CAD file, 2021-03-04]
3D/OmniVision/OV2640_WithConnector.stp
17.5 x 26.5 x 14.0 mm
