Kampi/KiCad/3D/Omron/G6QE.stp

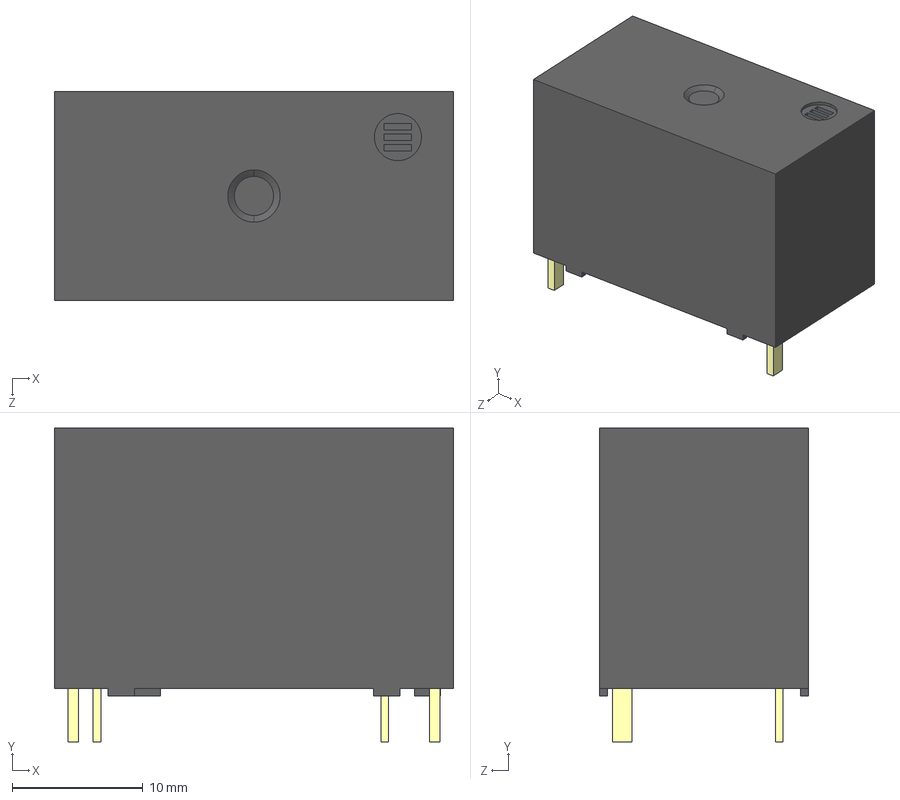
[picture p70: CAD file, 2024-09-20]
3D/Omron/G6QE.stp
30.5 x 24.0 x 16.0 mm
