Kampi/KiCad/3D/Osram/SFH7016.stp

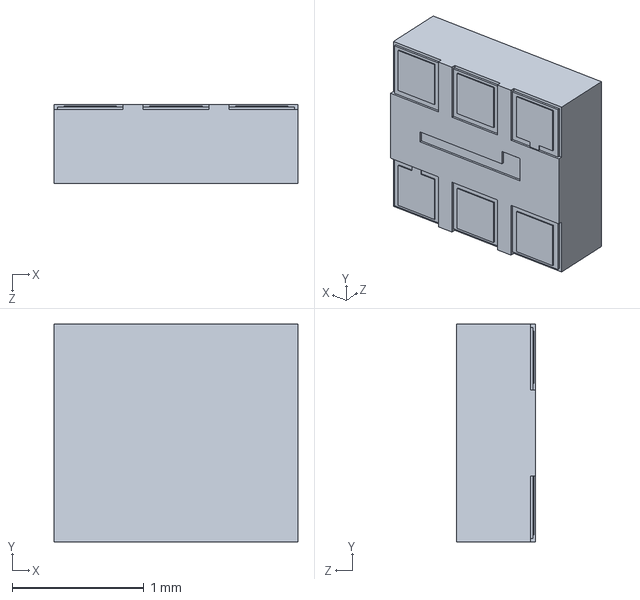
[picture p71: CAD file, 2026-01-24]
3D/Osram/SFH7016.stp
1.85 x 1.65 x 0.6 mm
