Kampi/KiCad/3D/Packages/AVX/7343_E.stp

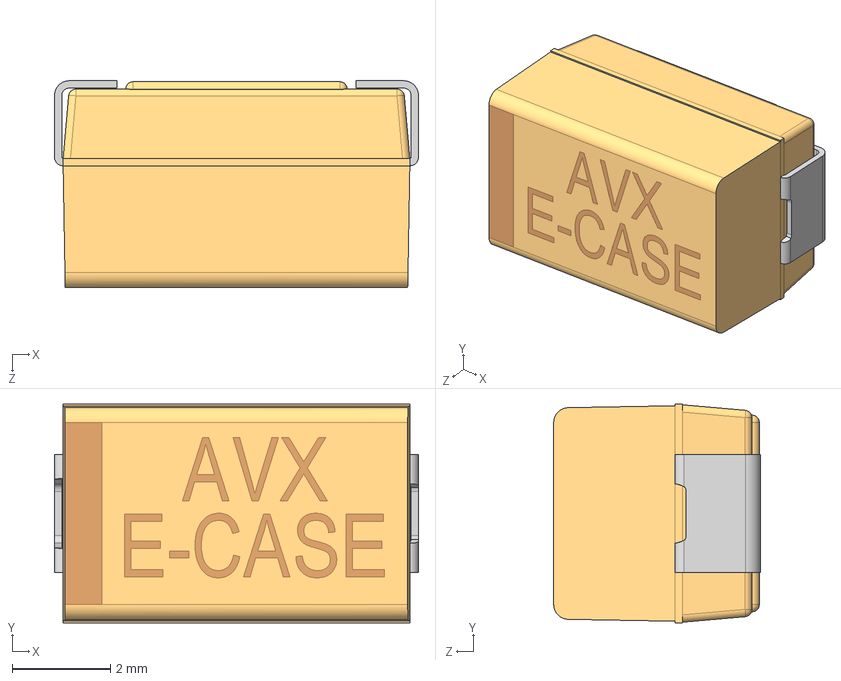
[picture p72: CAD file, 2020-06-05]
3D/Packages/AVX/7343_E.stp
7.40 x 4.45 x 4.20 mm
