Kampi/KiCad/3D/Packages/Vishay/SMPA.stp

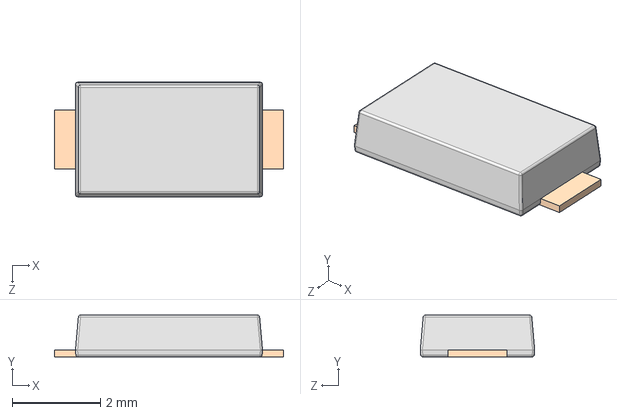
[picture p73: CAD file, 2020-09-08]
3D/Packages/Vishay/SMPA.stp
5.20 x 0.95 x 2.60 mm
