Kampi/KiCad/3D/Packages/X2QFN-8.stp

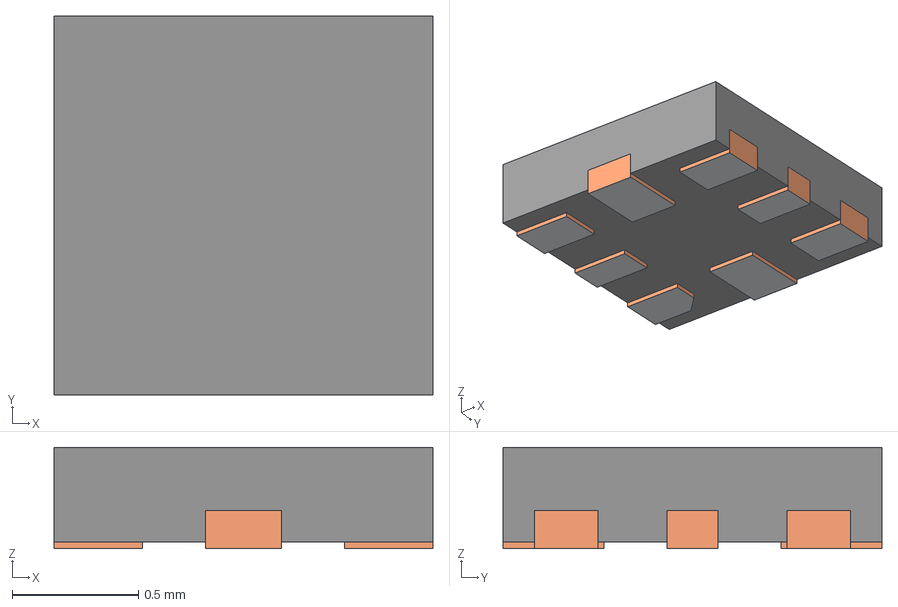
[picture p74: CAD file, 2026-08-25]
3D/Packages/X2QFN-8.stp
1.50 x 1.50 x 0.4 mm
FRAME-RUG0008A
BODY-QFN
PIN1-ID
