Kampi/KiCad/3D/Panasonic/EXBA10.stp

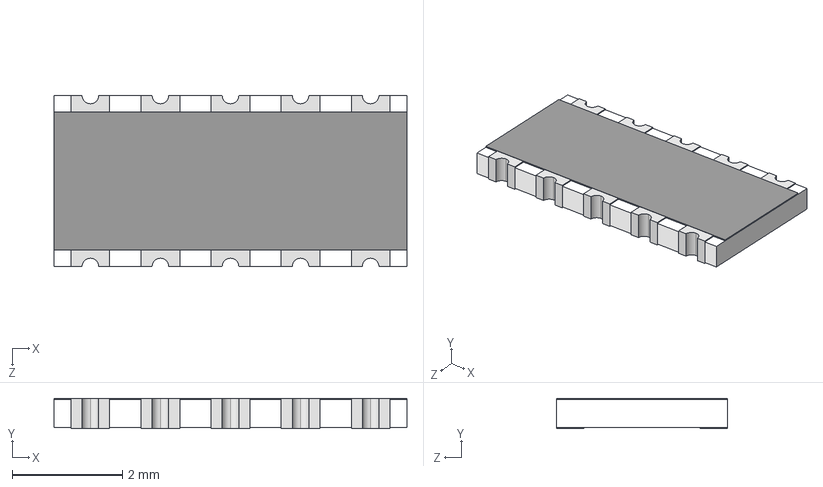
[picture p75: CAD file, 2023-05-01]
3D/Panasonic/EXBA10.stp
6.40 x 0.55 x 3.10 mm
