Kampi/KiCad/3D/Phoenix/MSTBA-2-5-4-G-5-08.stp

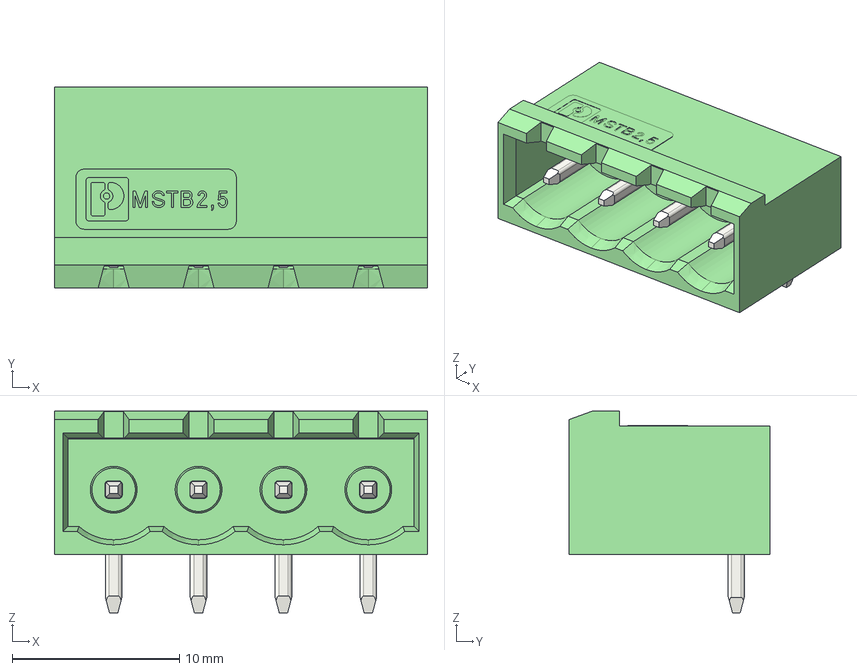
[picture p76: CAD file, 2026-07-16]
3D/Phoenix/MSTBA-2-5-4-G-5-08.stp
22.3 x 12.0 x 12.1 mm
