Kampi/KiCad/3D/Pomagtor/RD90_LZH0230529-004_DJ-5PIN_PH2_54.stp

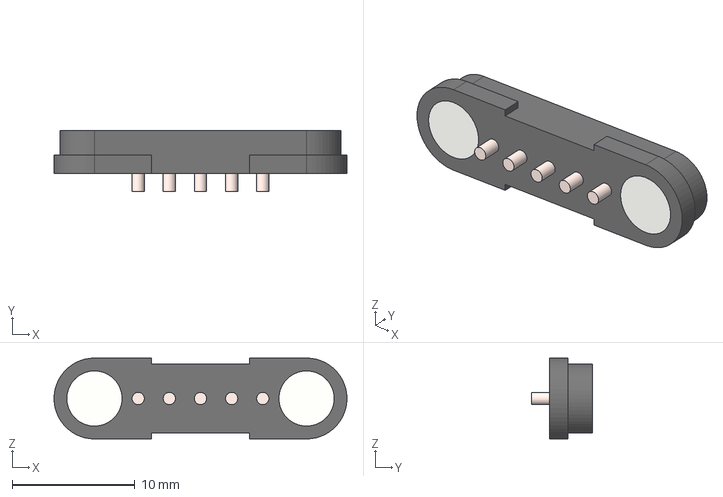
[picture p77: CAD file, 2023-08-23]
3D/Pomagtor/RD90_LZH0230529-004_DJ-5PIN_PH2_54.stp
23.9 x 5.00 x 6.60 mm
