Kampi/KiCad/3D/Pulse Electronics/P0841SNLT.stp

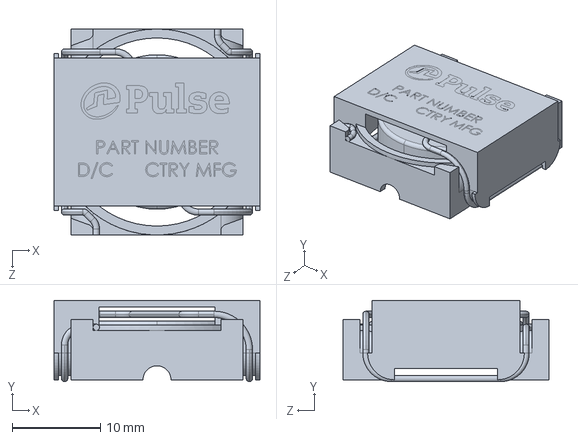
[picture p78: CAD file, 2026-01-24]
3D/Pulse Electronics/P0841SNLT.stp
23.4 x 9.23 x 23.4 mm
