Kampi/KiCad/3D/R_Potentiometer/Alpha/R0904N_tall.stp

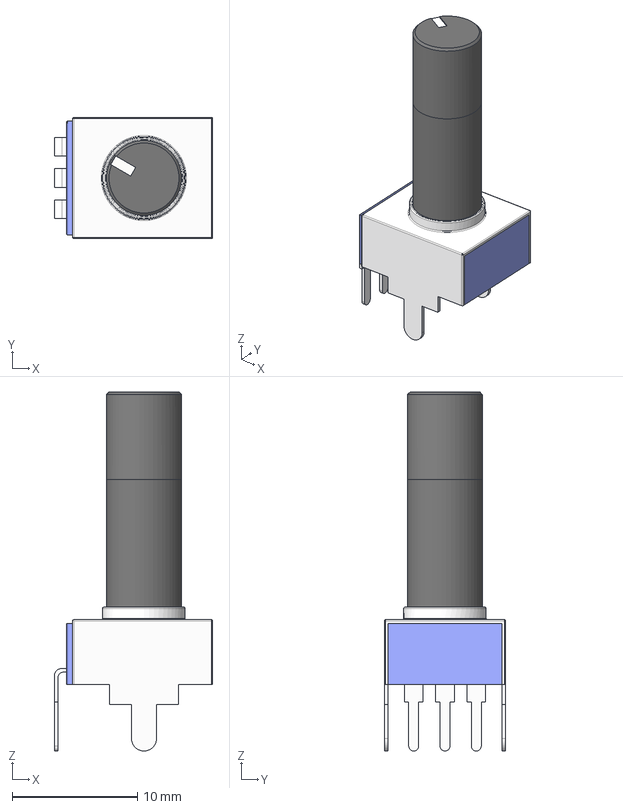
[picture p79: CAD file, 2020-06-21]
3D/R_Potentiometer/Alpha/R0904N_tall.stp
12.7 x 9.70 x 28.7 mm
