Kampi/KiCad/3D/R_Potentiometer/Bourns/PTV09A-4x30u-xxxx.stp

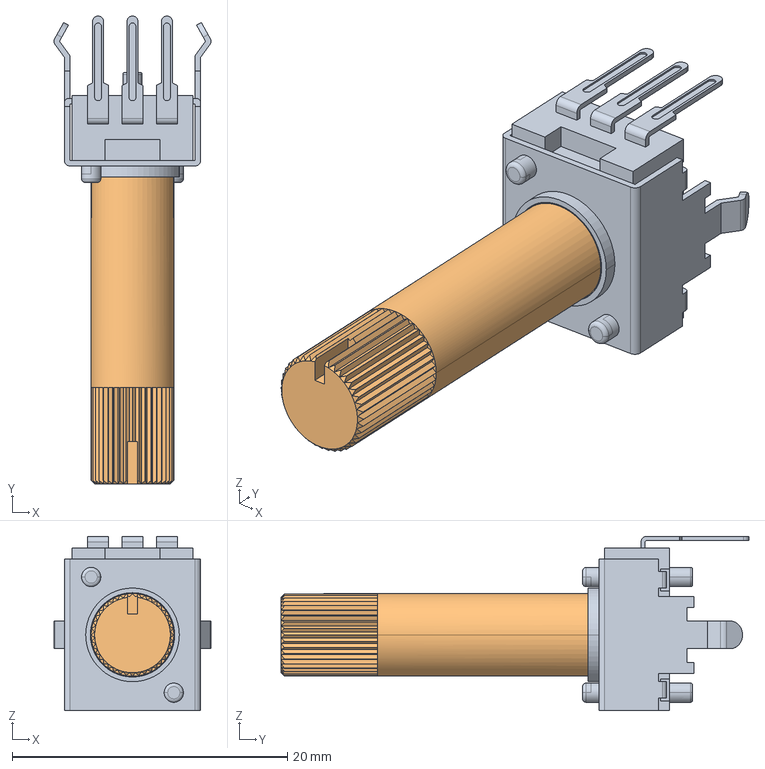
[picture p80: CAD file, 2021-05-16]
3D/R_Potentiometer/Bourns/PTV09A-4x30u-xxxx.stp
11.4 x 34.0 x 12.7 mm
