Kampi/KiCad/3D/R_Potentiometer/PT6KVM.stp

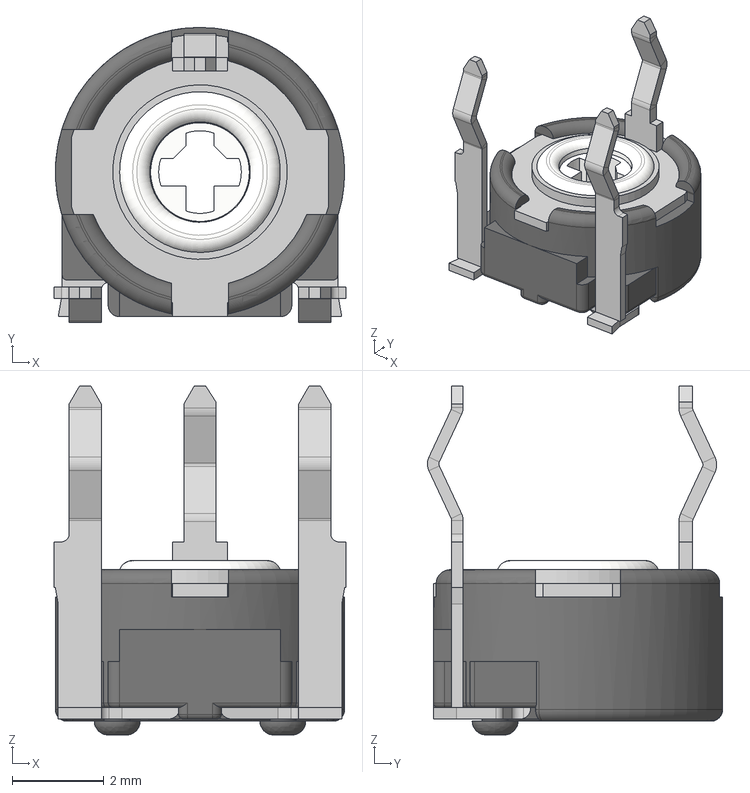
[picture p81: CAD file, 2026-01-24]
3D/R_Potentiometer/PT6KVM.stp
6.35 x 6.43 x 7.60 mm
PT6KH-HOT RUNNER-CARCASA_Predeterminada
PT6KH-HOT RUNNER-COLECTOR_Predeterminada
PT6KH-HOT RUNNER-PORTACURSOR_Predeterminada
PT6KH-HOT RUNNER-TERMINAL IZQUIERDO_Predeterminada
PT6KH-HOT RUNNER-TERMINAL DERECHO_Predeterminada
