Kampi/KiCad/3D/R_Potentiometer/Vishay/T7YB.stp

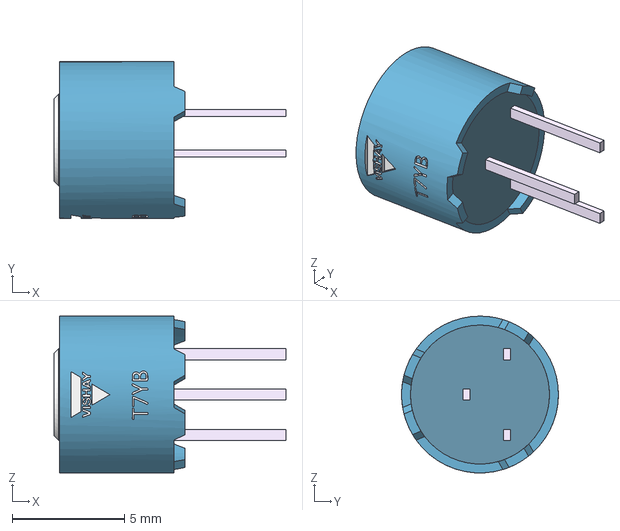
[picture p82: CAD file, 2026-01-24]
3D/R_Potentiometer/Vishay/T7YB.stp
10.4 x 7.00 x 7.00 mm
