Kampi/KiCad/3D/RAK/RAK3172-SiP.stp

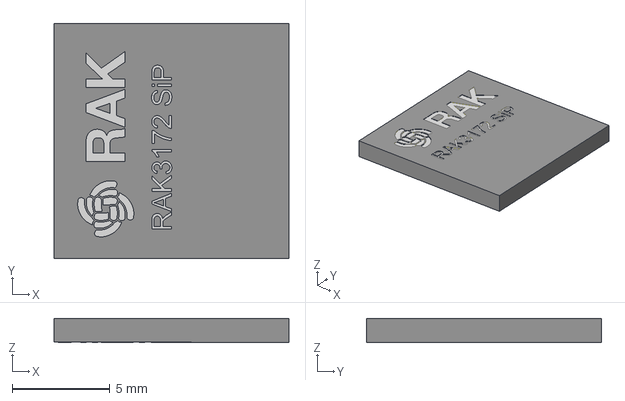
[picture p83: CAD file, 2023-05-01]
3D/RAK/RAK3172-SiP.stp
12.0 x 12.0 x 1.24 mm
