Kampi/KiCad/3D/RECOM/RAC05-K.step

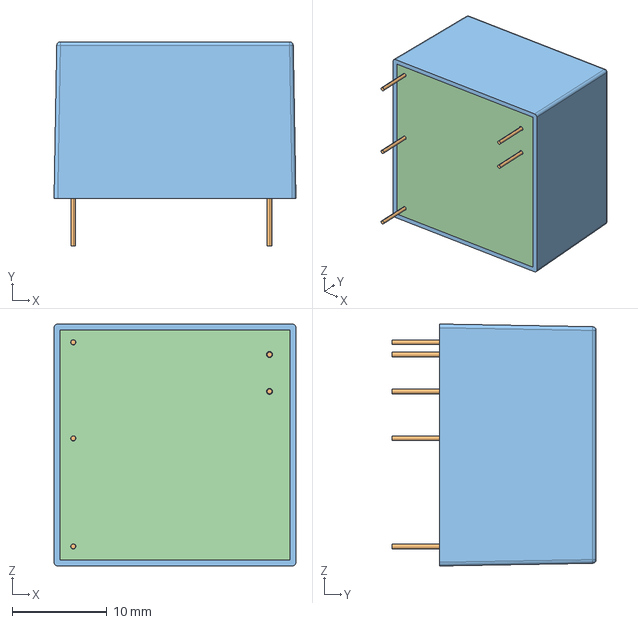
[picture p84: CAD file, 2026-08-25]
3D/RECOM/RAC05-K.step
25.6 x 21.6 x 25.6 mm
