Kampi/KiCad/3D/Relays/Omron/G5Q_1A.stp

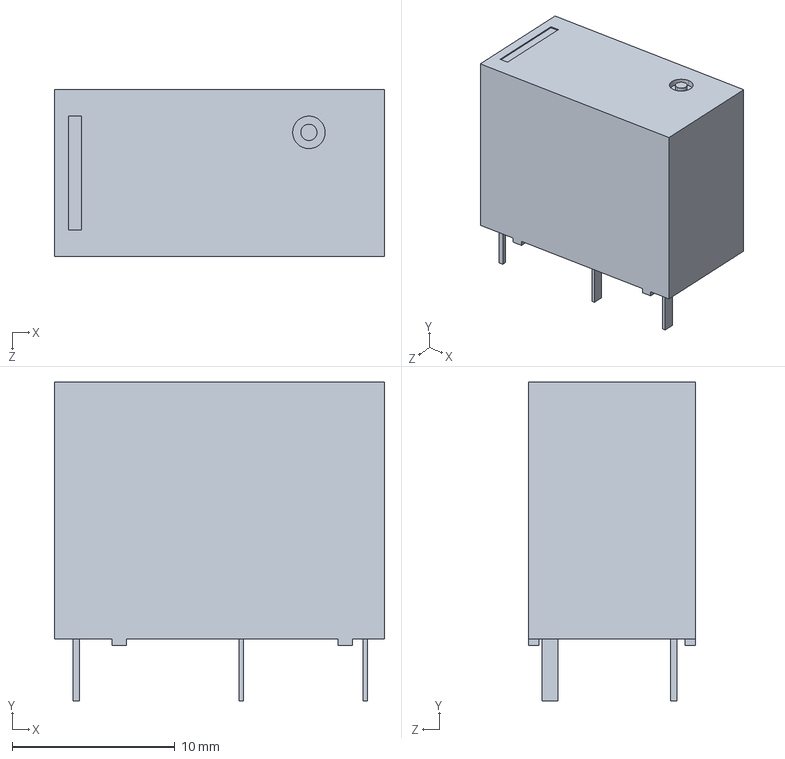
[picture p85: CAD file, 2020-09-23]
3D/Relays/Omron/G5Q_1A.stp
20.3 x 19.6 x 10.3 mm
