Kampi/KiCad/3D/Renesas/DA7212-01UM2.stp

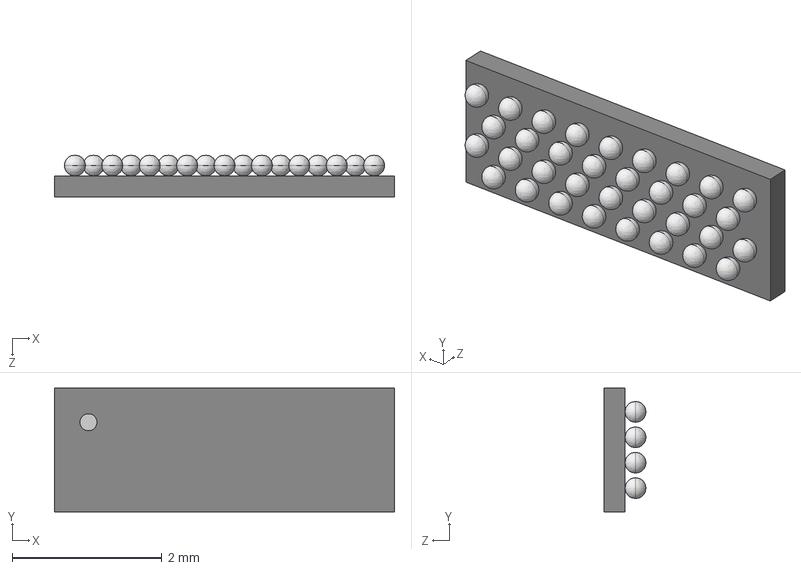
[picture p86: CAD file, 2026-01-24]
3D/Renesas/DA7212-01UM2.stp
4.55 x 1.65 x 0.561 mm
