Kampi/KiCad/3D/Rf-star/RF-BM-2652.stp

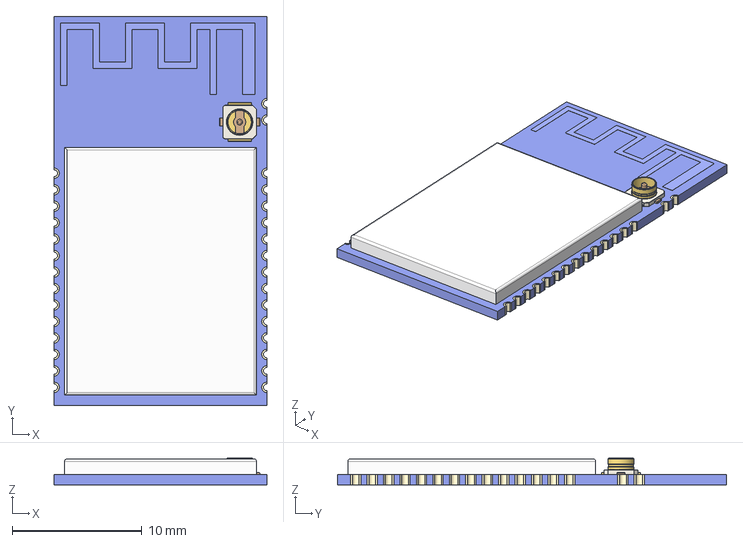
[picture p87: CAD file, 2026-07-01]
3D/Rf-star/RF-BM-2652.stp
16.4 x 30.0 x 2.04 mm
