Kampi/KiCad/3D/ROHM/RUM001L02.stp

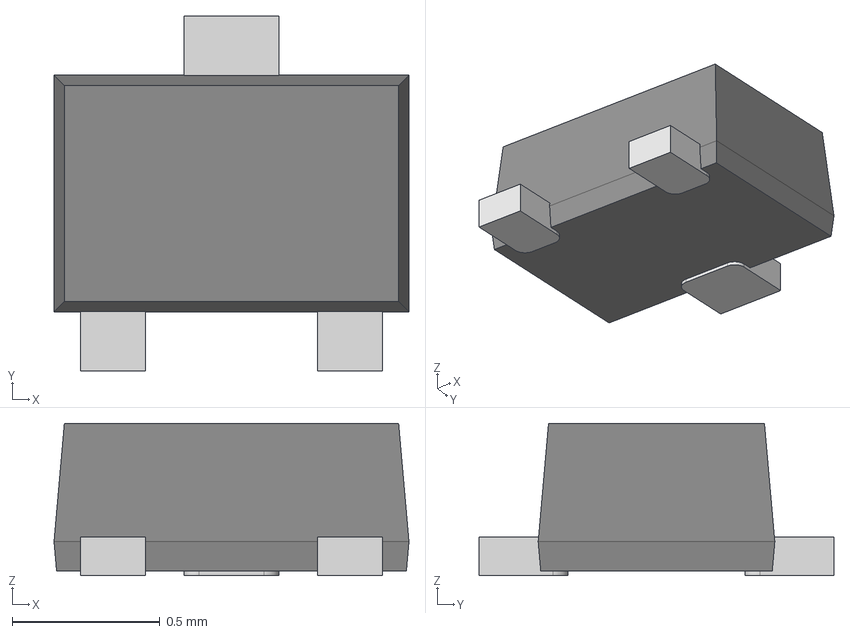
[picture p88: CAD file, 2021-02-05]
3D/ROHM/RUM001L02.stp
1.20 x 1.20 x 0.515 mm
3D_Model_VMT3_Rev0-prt0
3D_Model_VMT3_Rev0-prt1
3D_Model_VMT3_Rev0-prt2
3D_Model_VMT3_Rev0-prt3
