Kampi/KiCad/3D/Same Sky/CPT-9019S-SMT-TR.stp

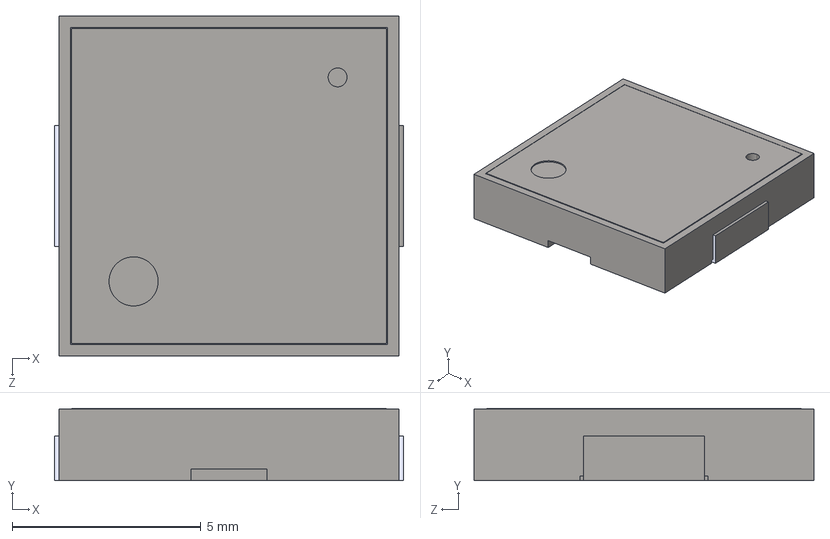
[picture p89: CAD file, 2026-05-02]
3D/Same Sky/CPT-9019S-SMT-TR.stp
9.24 x 1.91 x 9.00 mm
