Kampi/KiCad/3D/Samtec/SM02B-SRSS-TB-LF-SN.stp

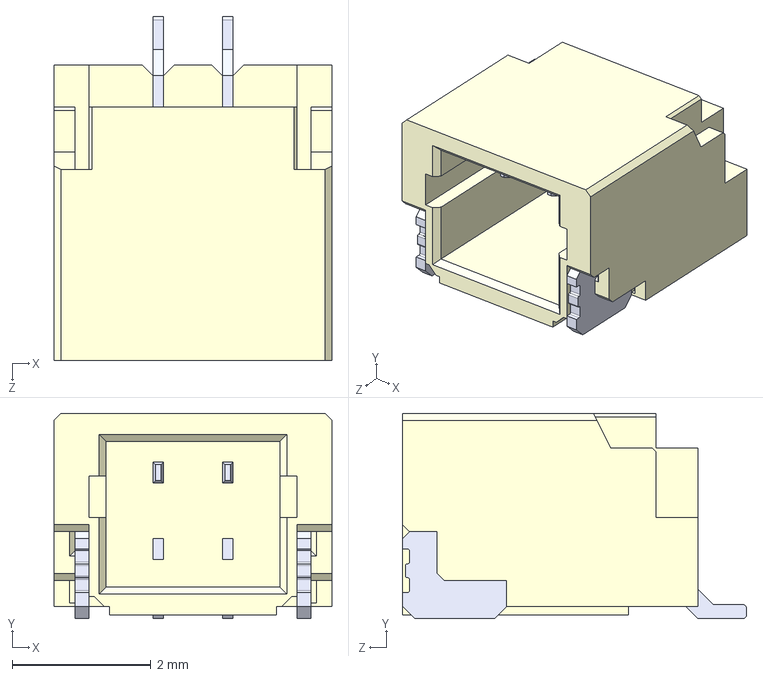
[picture p90: CAD file, 2026-02-19]
3D/Samtec/SM02B-SRSS-TB-LF-SN.stp
4.00 x 2.95 x 4.95 mm
