Kampi/KiCad/3D/SD/Micro SD.stp

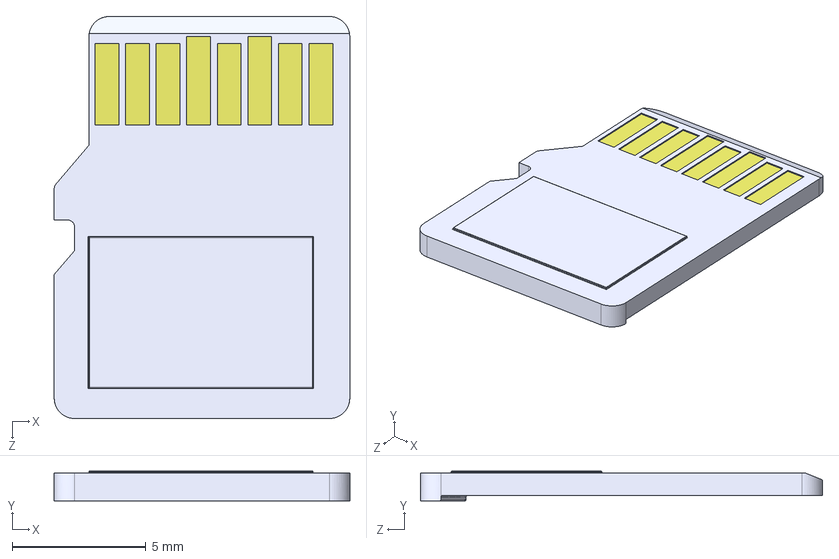
[picture p91: CAD file, 2026-05-26]
3D/SD/Micro SD.stp
11.0 x 1.12 x 15.0 mm
