Kampi/KiCad/3D/Senba/D203B.stp

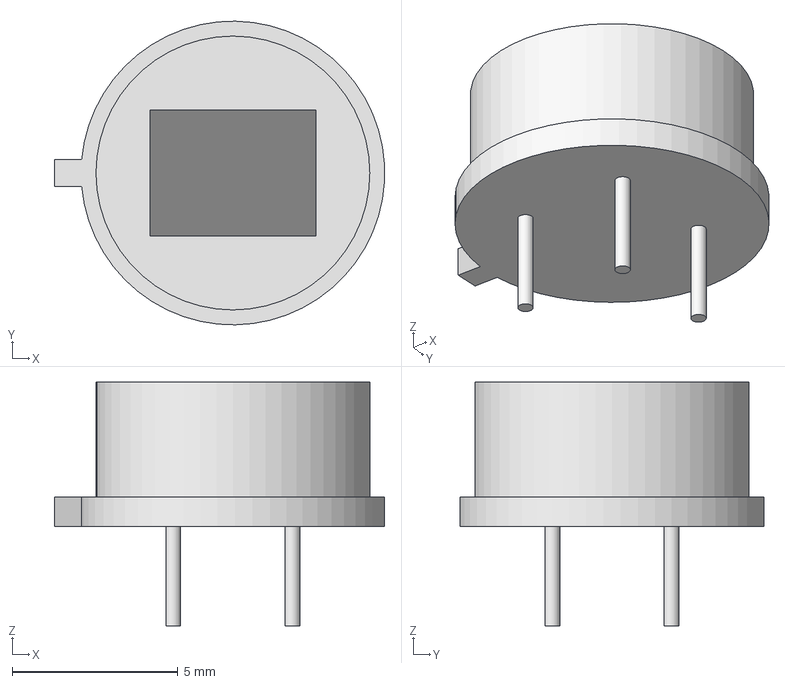
[picture p92: CAD file, 2021-03-04]
3D/Senba/D203B.stp
9.94 x 9.15 x 7.35 mm
