Kampi/KiCad/3D/Sensirion/SHT41-AD1B-R3.stp

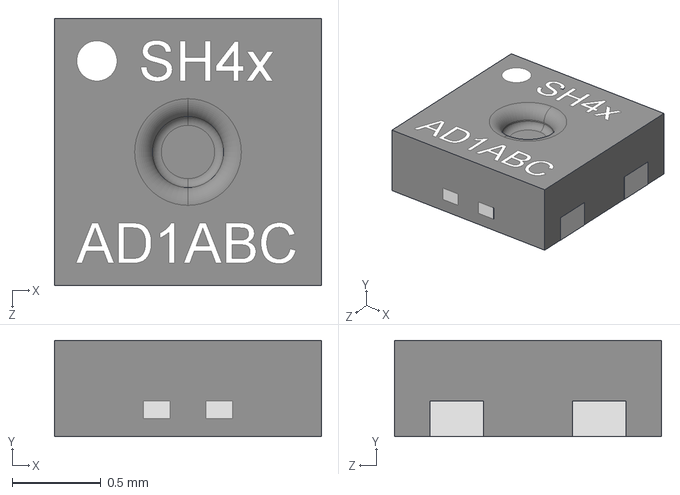
[picture p93: CAD file, 2022-03-19]
3D/Sensirion/SHT41-AD1B-R3.stp
1.50 x 0.542 x 1.50 mm
