Kampi/KiCad/3D/Silvertel/AG5424.stp

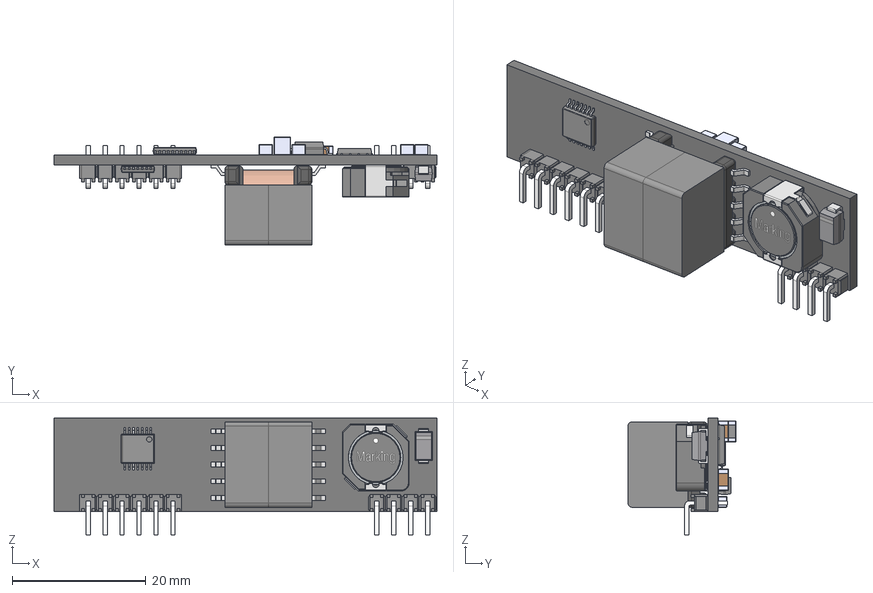
[picture p94: CAD file, 2026-07-16]
3D/Silvertel/AG5424.stp
57.3 x 16.2 x 17.5 mm
PCB
070-2381_6P
EP13-2381
150-0899_6D
150-0899_6D001
shielding ring
core
base
base001
glue
AD74AB66-7A37-4F10-BC0E-3733FB91EFA1
BODY-TSSOP
LEAD-TSSOP
LEAD-TSSOP001
LEAD-TSSOP002
LEAD-TSSOP003
LEAD-TSSOP004
LEAD-TSSOP005
LEAD-TSSOP006
LEAD-TSSOP007
LEAD-TSSOP008
LEAD-TSSOP009
LEAD-TSSOP010
LEAD-TSSOP011
LEAD-TSSOP012
LEAD-TSSOP013
BODY-TSSOP001
LEAD-TSSOP014
LEAD-TSSOP015
LEAD-TSSOP016
LEAD-TSSOP017
LEAD-TSSOP018
LEAD-TSSOP019
LEAD-TSSOP020
LEAD-TSSOP021
LEAD-TSSOP022
LEAD-TSSOP023
LEAD-TSSOP024
LEAD-TSSOP025
LEAD-TSSOP026
LEAD-TSSOP027
LEAD-TSSOP028
LEAD-TSSOP029
LEAD-TSSOP030
LEAD-TSSOP031
LEAD-TSSOP032
LEAD-TSSOP033
3H7
0ED97B3F-6B44-4599-8682-60F6A2334077
0ED97B3F-6B44-4599-8682-60F6A2334078
LBC3225T101MR
LBC3225T101MR001
LBC3225T101MR002
GRJ31CC71E106KE11L
GRJ31CC71E106KE11L001
GRJ31CC71E106KE11L002
GRJ31CC71E106KE11L005
GRJ31CC71E106KE11L006
GRJ31CC71E106KE11L007
GRJ31CC71E106KE11L009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
