Kampi/KiCad/3D/SIMCom/SIM28ML.stp

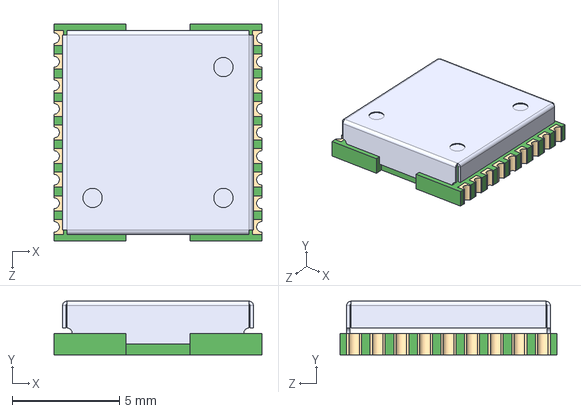
[picture p95: CAD file, 2023-01-01]
3D/SIMCom/SIM28ML.stp
9.70 x 2.50 x 10.1 mm
