Kampi/KiCad/3D/Socket/DIP_Socket/ZIF_28.stp

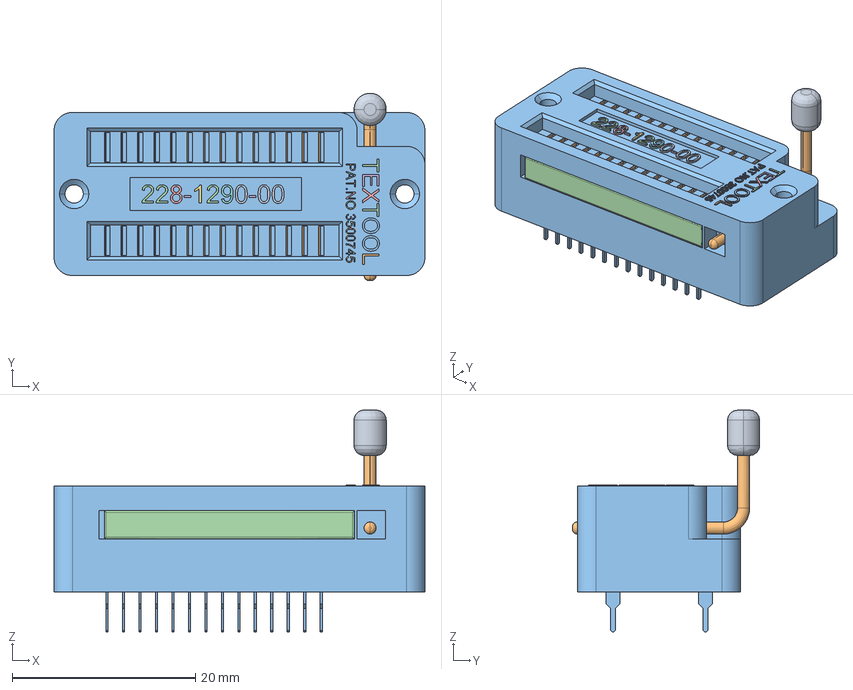
[picture p96: CAD file, 2019-10-13]
3D/Socket/DIP_Socket/ZIF_28.stp
40.5 x 20.5 x 24.2 mm
