Kampi/KiCad/3D/SSD/2242_M.stp

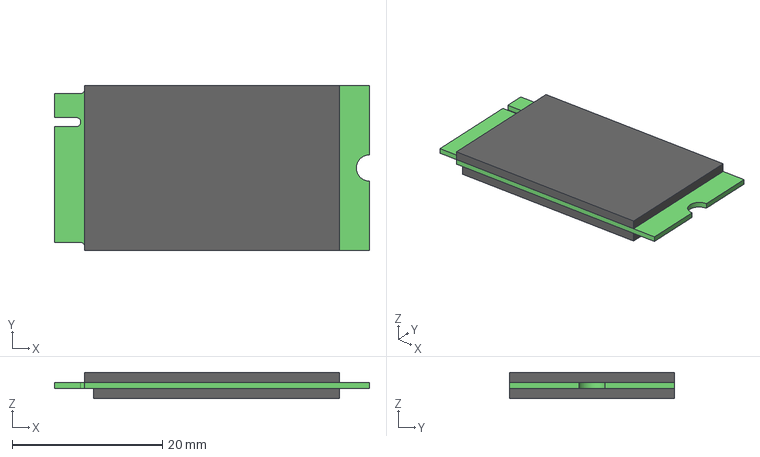
[picture p97: CAD file, 2026-05-05]
3D/SSD/2242_M.stp
42.0 x 22.0 x 3.50 mm
