Kampi/KiCad/3D/ST/MB1404-H563ZI-C01.stp

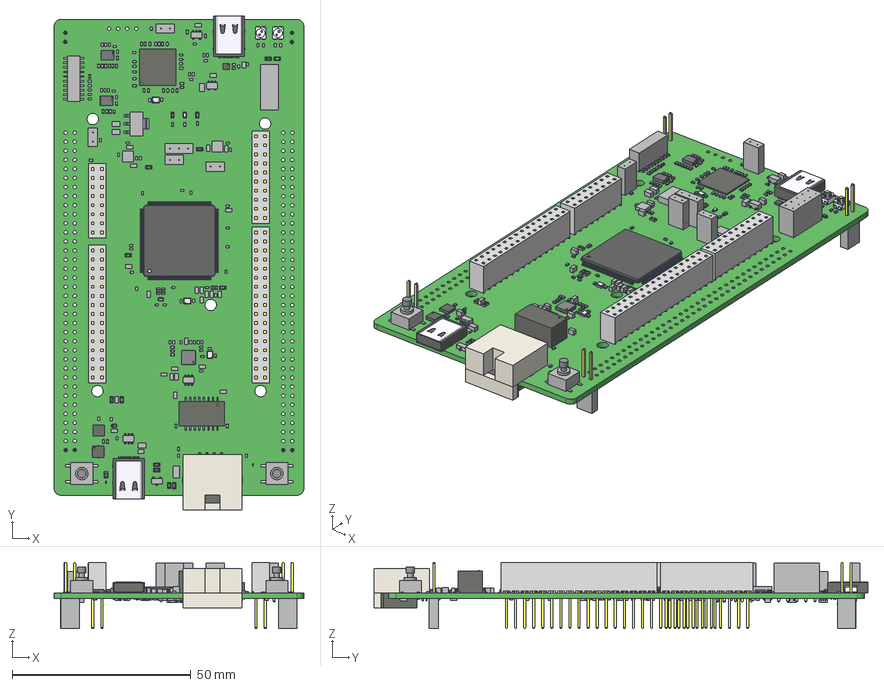
[picture p98: CAD file, 2026-08-25]
3D/ST/MB1404-H563ZI-C01.stp
70.0 x 138.4 x 18.6 mm
Extruded x 428
R0402 x 102
632723300011_Housing x 2
632723300011_Shielding_3_v3 x 2
632723300011_PIN2_Top_v3 x 16
632723300011_Housing_TOP x 2
632723300011_Shielding_1_v3 x 2
632723300011_PIN1_Top_v3 x 8
632723300011_Housing_Bottom x 2
632723300011_PIN1_Bottom_v3 x 2
632723300011_PIN2_Bottom_v3 x 2
632723300011_PIN4_Bottom_v3 x 2
632723300011_PIN5_Bottom_v3 x 2
632723300011_PIN6_Bottom_v3 x 2
632723300011_PIN7_Bottom_v3 x 2
632723300011_Shielding_2 x 4
632723300011_PIN1_Bottom_v3_mir x 2
632723300011_PIN4_Bottom_v3_mir x 2
632723300011_PIN6_Bottom_v3_mir x 2
632723300011_PIN2_Bottom_v3_mir x 2
632723300011_PIN5_Bottom_v3_mir x 2
632723300011_PIN7_Bottom_v3_mir x 2
632723300011_Housing_Bottom3 x 2
SOT323-5L x 2
_TSW-102-09-G-S_body x 4
_T-1S6-09-TSW-1-09-2-S x 4
C0805_2012D x 4
C0402 x 57
C0603 x 24
R0603 x 44
SOT23-3_TO-236AB x 4
_TSW-102-07-G-S_body x 4
_T-1S6-07-TSW-1-07-2-S x 4
LQFP144_20X20_P050
_FTSH-110-01-L-DV_body
_FTSH-110-01-L-DV_pins1
_FTSH-110-01-L-DV_pins2
_TSW-105-07-G-D_body
_T-1S6-07-TSW-1-07-5-D
Samtec-TSW-103-07-F-S
SOT223
_T1SSQ-108-23-F-D
_P2SSQ-108-23-F-D
_T1SSQ-115-23-F-D
_P2SSQ-115-23-F-D
_T1SSQ-110-23-F-D
_P2SSQ-110-23-F-D
_T1SSQ-117-23-F-D
_P2SSQ-117-23-F-D
C1206_H1P6
L0603
User_Library-LED_0603_G_Pocket002 x 3
User_Library-LED_0603_G_Pad004 x 3
User_Library-LED_0603_G_Fillet x 3
User_Library-LED_0603_G_Pocket001 x 3
User_Library-LED_0603_G_Pad x 3
SOT23-6 x 2
VQFN24-EPAD
DFN6-EPAD_3X3_P095 x 2
SOT23-5L x 2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
