Kampi/KiCad/3D/Switches/Apem/SMT_Series.stp

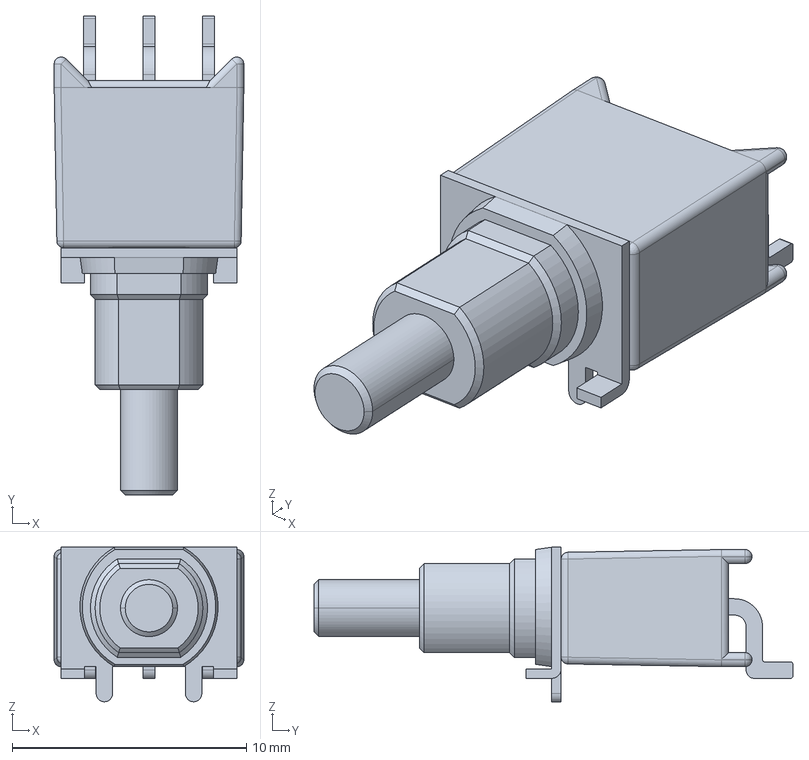
[picture p99: CAD file, 2020-01-17]
3D/Switches/Apem/SMT_Series.stp
8.10 x 20.5 x 6.60 mm
