Kampi/KiCad/3D/Switches/Nidec/ATE1D-2M3-10-Z.stp

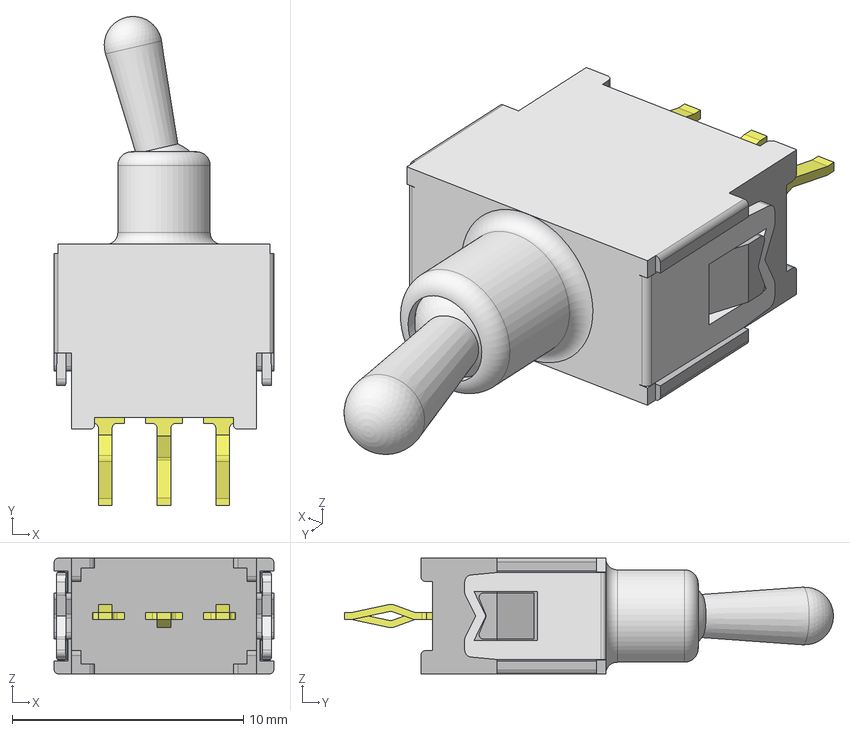
[picture p100: CAD file, 2020-06-19]
3D/Switches/Nidec/ATE1D-2M3-10-Z.stp
9.50 x 21.1 x 5.00 mm
_2001A1_(ATE)
_1001A-1
_1001A-2
_3001A-329
_3001A-229
_3001A-29
