Kampi/KiCad/3D/Switches/Panasonic/ESE24MH1.stp

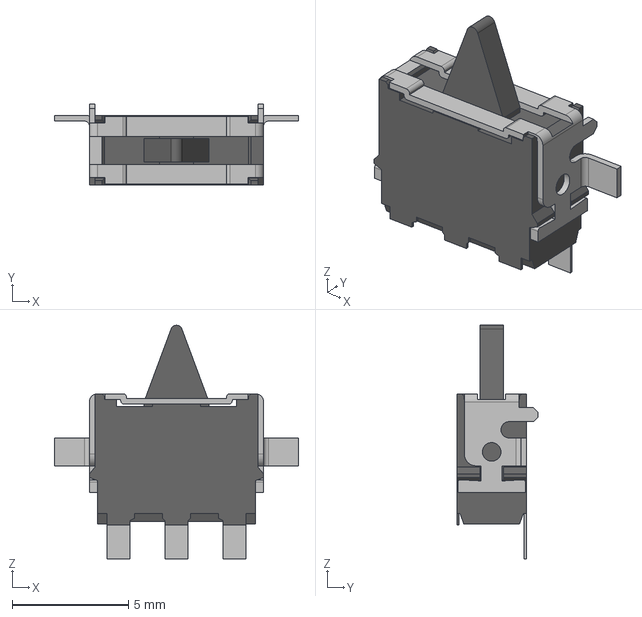
[picture p101: CAD file, 2020-01-24]
3D/Switches/Panasonic/ESE24MH1.stp
10.5 x 3.50 x 10.1 mm
