Kampi/KiCad/3D/Switches/Schurter/1241.162X.5.stp

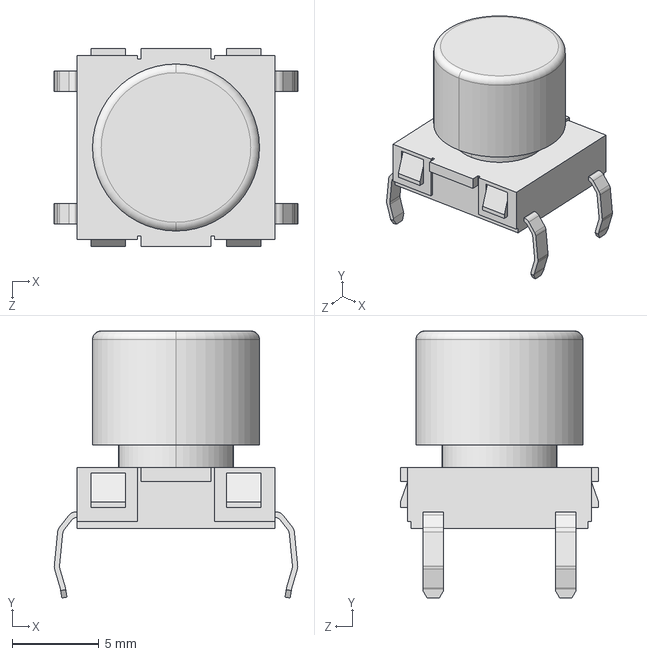
[picture p102: CAD file, 2021-03-04]
3D/Switches/Schurter/1241.162X.5.stp
14.0 x 15.3 x 11.4 mm
