Kampi/KiCad/3D/Switches/SW_SPST_TL3305A.stp

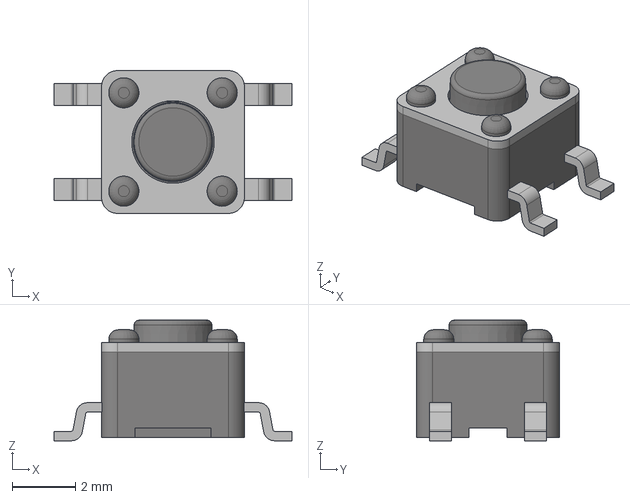
[picture p103: CAD file, 2026-01-24]
3D/Switches/SW_SPST_TL3305A.stp
7.50 x 4.50 x 3.80 mm
