Kampi/KiCad/3D/Switches/TE Connectivity/C-2454985-3-A.stp

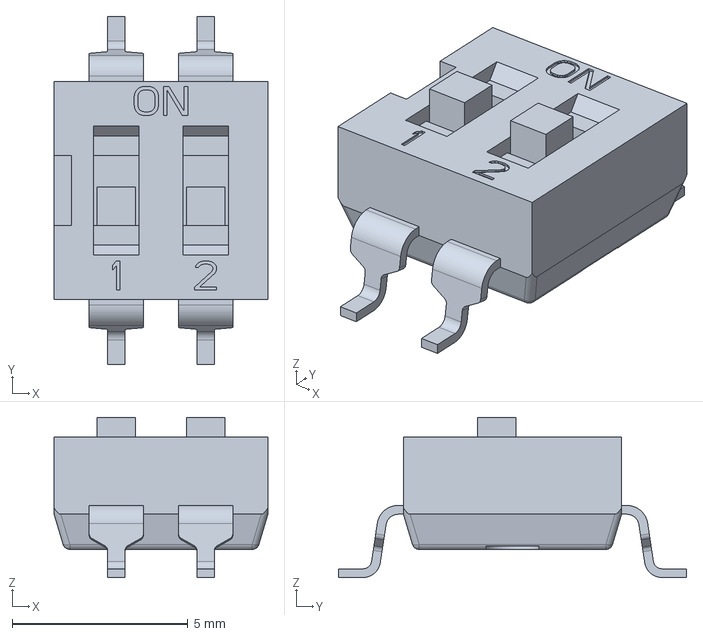
[picture p104: CAD file, 2026-01-24]
3D/Switches/TE Connectivity/C-2454985-3-A.stp
6.08 x 9.90 x 4.55 mm
