Kampi/KiCad/3D/Tag Connect/TC2030-IDC.stp

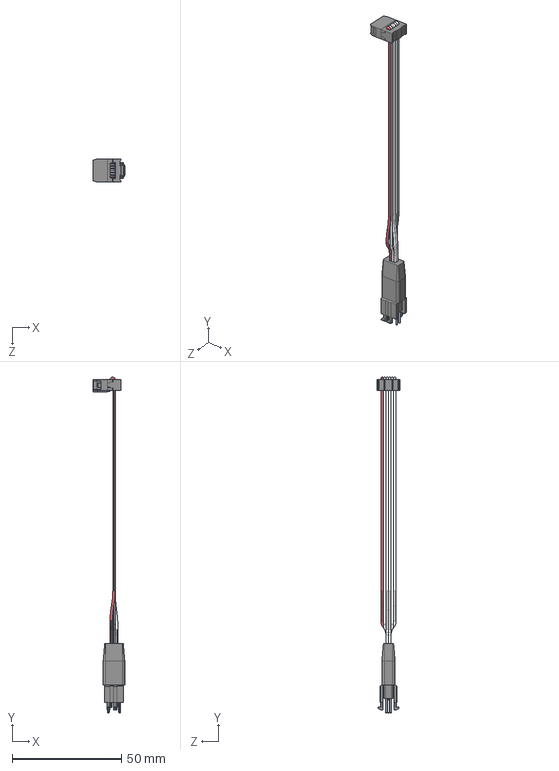
[picture p105: CAD file, 2023-10-31]
3D/Tag Connect/TC2030-IDC.stp
14.5 x 153.6 x 10.7 mm
