Kampi/KiCad/3D/Taiyo Yuden/NRS6028.stp

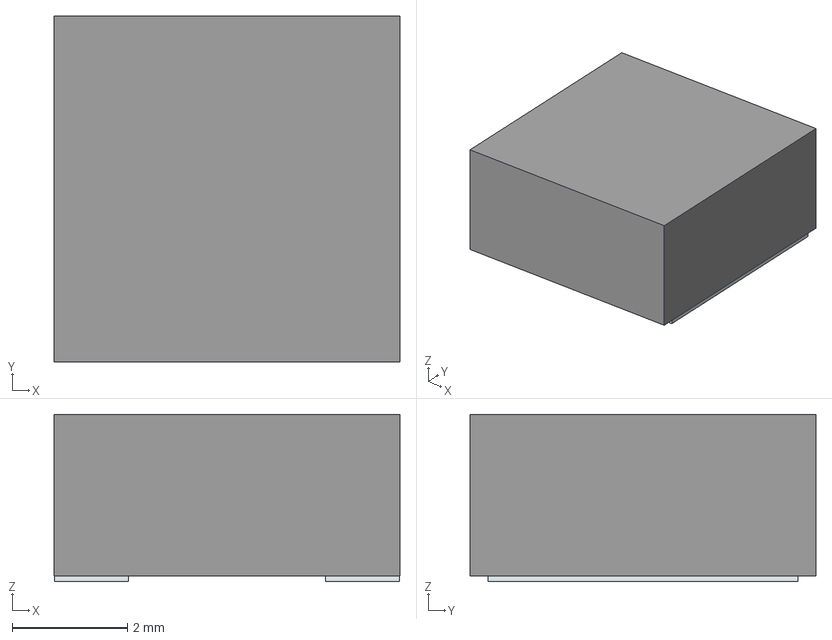
[picture p106: CAD file, 2026-01-24]
3D/Taiyo Yuden/NRS6028.stp
6.00 x 6.00 x 2.90 mm
Pins
