Kampi/KiCad/3D/Taoglas/ILA.02_Web.stp

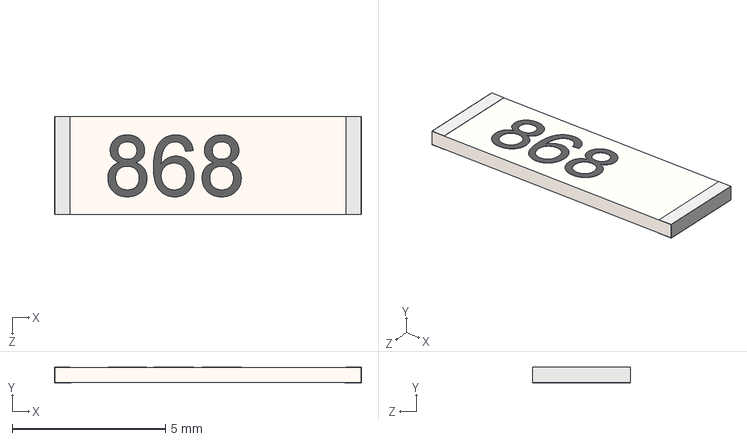
[picture p107: CAD file, 2022-09-24]
3D/Taoglas/ILA.02_Web.stp
10.0 x 0.52 x 3.20 mm
