Kampi/KiCad/3D/TDK/VLCF5020T-150MR90-1.stp

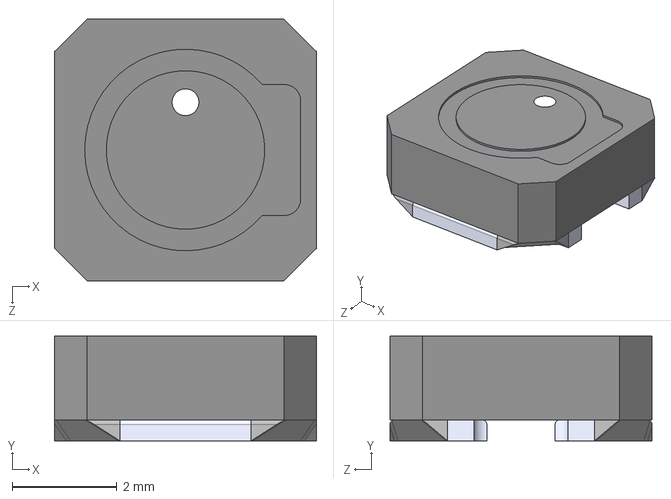
[picture p108: CAD file, 2026-01-24]
3D/TDK/VLCF5020T-150MR90-1.stp
5.00 x 2.00 x 5.00 mm
