Kampi/KiCad/3D/Toradex/Verdin Industrial Heatsink Type 1 V1.0B.stp

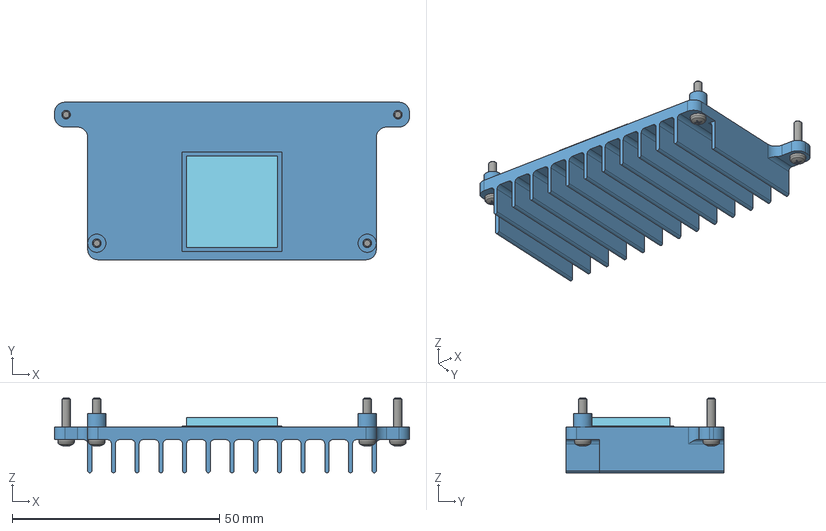
[picture p109: CAD file, 2026-06-03]
3D/Toradex/Verdin Industrial Heatsink Type 1 V1.0B.stp
85.6 x 38.0 x 18.0 mm
83300000997_heatsink
83300000997_Gap Pad
ISO 7045 - M2 x 10 - 4.8 - H x 4
