Kampi/KiCad/3D/Toshiba/TLP293(TPL,E.stp

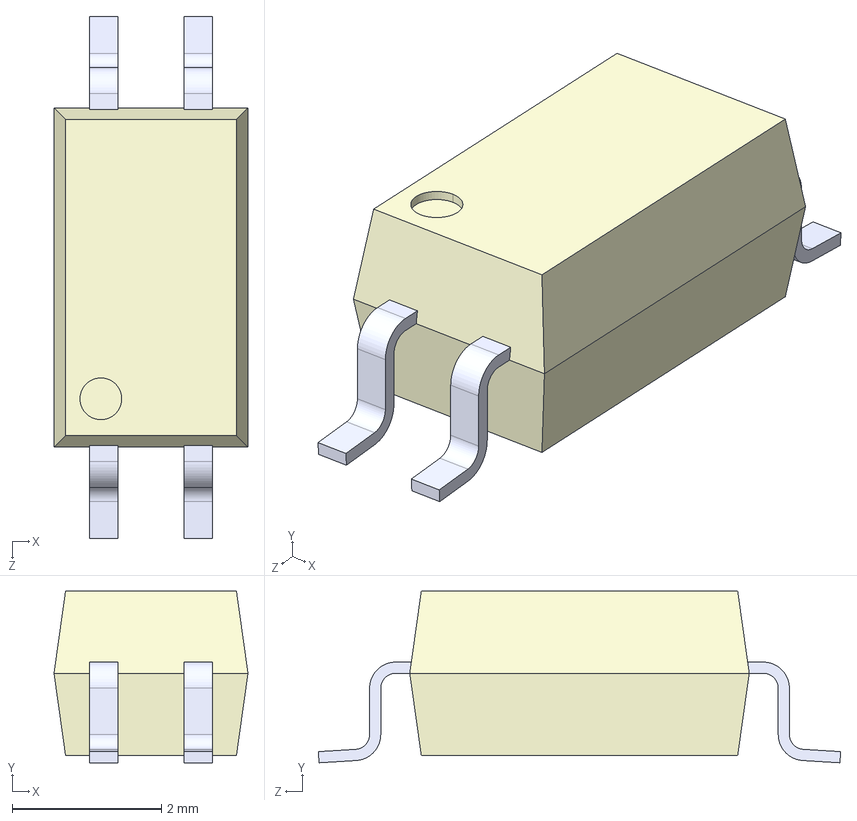
[picture p110: CAD file, 2026-07-16]
3D/Toshiba/TLP293(TPL,E.stp
2.60 x 2.30 x 7.00 mm
