Kampi/KiCad/3D/Traco Power/TMPW 25.stp

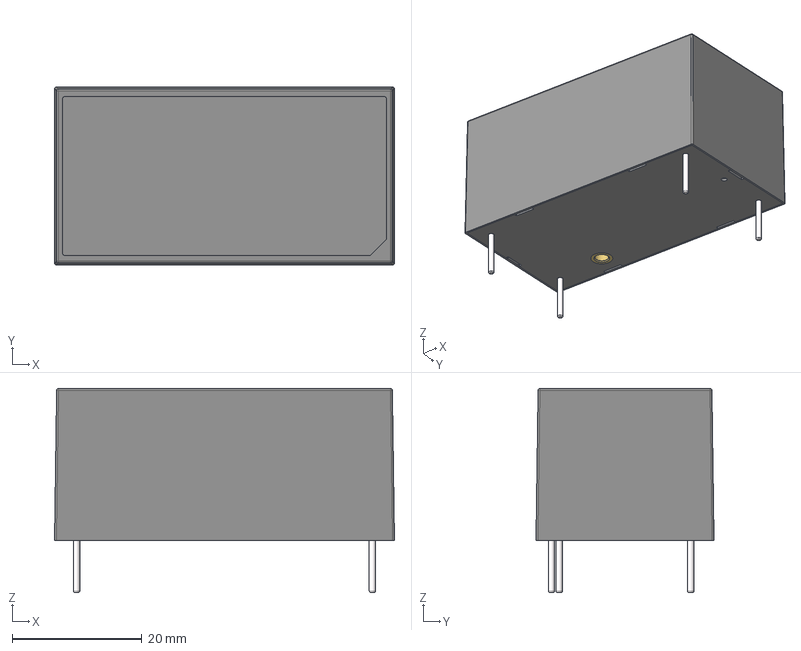
[picture p111: CAD file, 2024-09-03]
3D/Traco Power/TMPW 25.stp
52.5 x 27.5 x 31.5 mm
