Kampi/KiCad/3D/u-blox/NORA-B1x6.stp

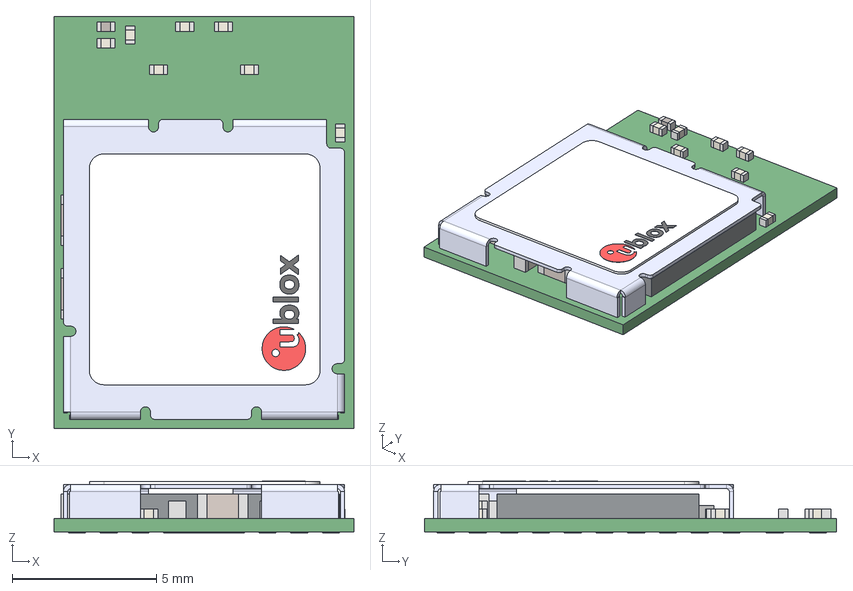
[picture p112: CAD file, 2023-08-20]
3D/u-blox/NORA-B1x6.stp
10.4 x 14.3 x 1.79 mm
label_8x8
logo_x_4mm
logo_o_4mm
logo_l_4mm
logo_b_4mm
logo_u_4mm
UBXH04-0000650_NORA-TYPE-1_SHIELD_rev3
Extruded x 185
aQFN-116_(7x7) x 2
Free-Models
