Kampi/KiCad/3D/VCC/LFB012CTP.stp

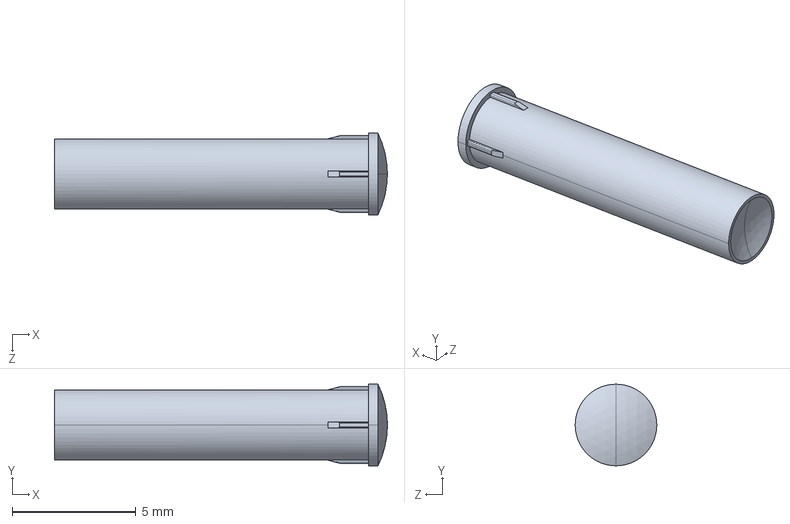
[picture p113: CAD file, 2026-01-24]
3D/VCC/LFB012CTP.stp
13.5 x 3.30 x 3.30 mm
