Kampi/KiCad/3D/Vishay/VEMD5-5X4_VIS.stp

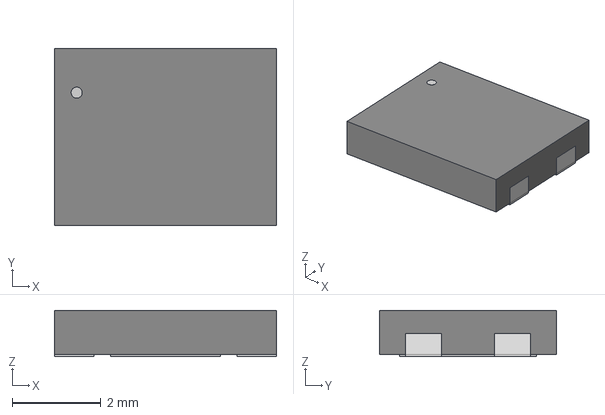
[picture p114: CAD file, 2026-01-24]
3D/Vishay/VEMD5-5X4_VIS.stp
5.00 x 3.99 x 1.04 mm
