Kampi/KiCad/3D/Vybronics/Z30C1T8219732L.stp

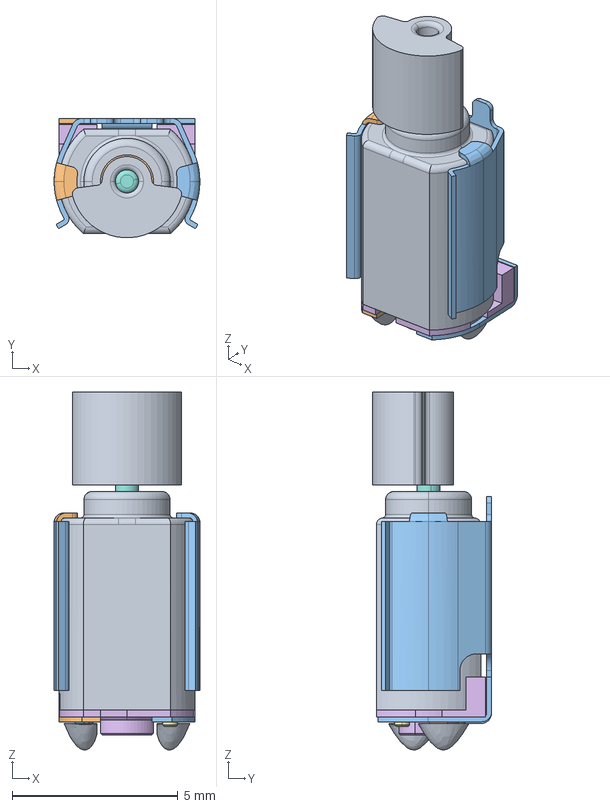
[picture p115: CAD file, 2026-01-24]
3D/Vybronics/Z30C1T8219732L.stp
4.40 x 3.60 x 10.8 mm
¿Ɵ1
¿Ȗᴐ_1
4311ͺо_1
4311ͺо_002
4311ͺо_003
4311ͺо_004
4311ͺо_005
4311ͺо_006
4311ͺо_007
4311ͺо_008
4311ͺо_009
4311ͺо_010
4311ͺо_011
4311ͺо_012
4311ͺо_013
4311ͺо_014
4311͗¹۟1
4311¸ÖÖá9.7_0.7_9.0
4311ֻ·ؓ_1
4311ֻ·ؓ_002
4311ֻ·ؓ_003
4311ֻ·ؓ_004
4311ֻ·ؓ_005
»ù°å_(3.3)
»ù°å_(3.3)001
»ù°å_(3.3)002
º¸Ͻµ❱ x 2
֧¼۟2
֧¼۟003
´ÅÌú x 2
µ苢_ x 2
µ苢_001 x 2
µ苢_002 x 2
Ïß°ü x 3
»ù°åÖá³Ð
ֱ¶¯Ö
VZ30C1T8219732Lº¸Ͻ¶̗Ѳ
VZ30C1T8219732Lº¸Ͻ¶̗Ѳ001
