Kampi/KiCad/Drawings/Particle/mesh/argon/argon-v1.step

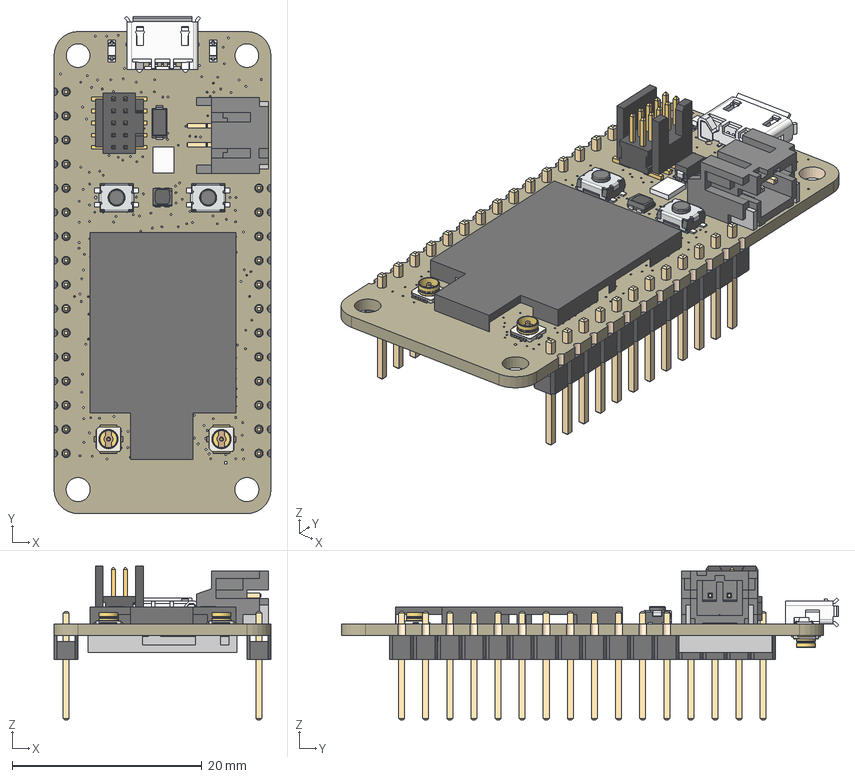
[picture p116: CAD file, 2020-05-14]
Drawings/Particle/mesh/argon/argon-v1.step
22.9 x 52.4 x 16.2 mm
Board
PMOS
10uF
2n7002
XC6208A42 x 2
2n7002_1
B5819w
0R
10uF_1
SKY13351-378LF
ss3p
_FTSH_105_01_L_DV_K_body_2
_FTSH_105_01_L_DV_K_pins1_4
_FTSH_105_01_L_DV_K_pins2_6
pin x 2
mount x 2
housing
microUSB
LED_CLVBA-FKA v1
switch v1 x 2
spacer (1) x 16
pin (1) x 16
spacer (1)_1 x 12
pin (1)_1 x 12
uFL x 3
MBR120
MICRO_led (1) v1 x 2
argon-bottom-rf-shield
argon-top-rf-shield v4
