Kampi/KiCad/3D/Abracon/ATXAIG-H13_ABR.stp

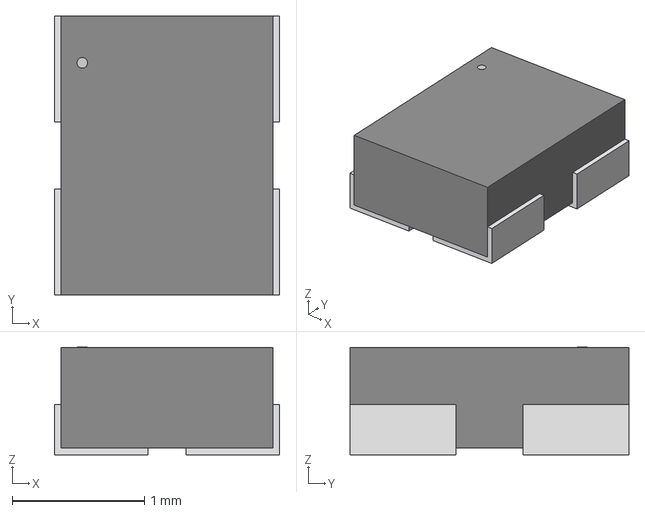
[picture p117: CAD file, 2024-07-23]
3D/Abracon/ATXAIG-H13_ABR.stp
1.70 x 2.11 x 0.815 mm
