Kampi/KiCad/3D/Amphenol/A-1JB.stp

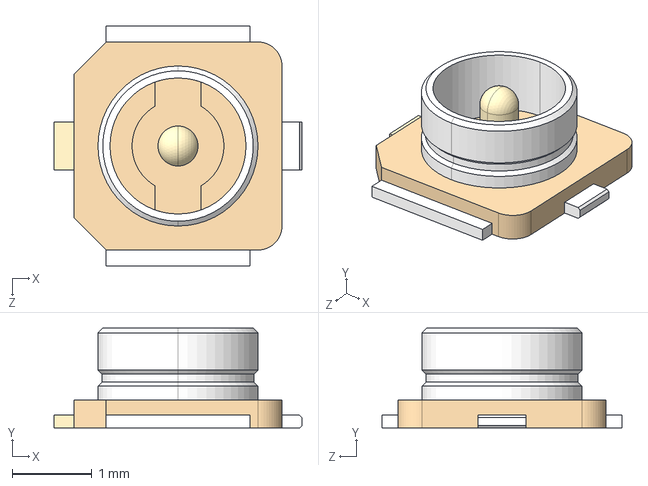
[picture p118: CAD file, 2026-06-22]
3D/Amphenol/A-1JB.stp
3.10 x 1.25 x 3.00 mm
