Kampi/KiCad/3D/Antenna/GSM_ANTENNA_42mm.stp

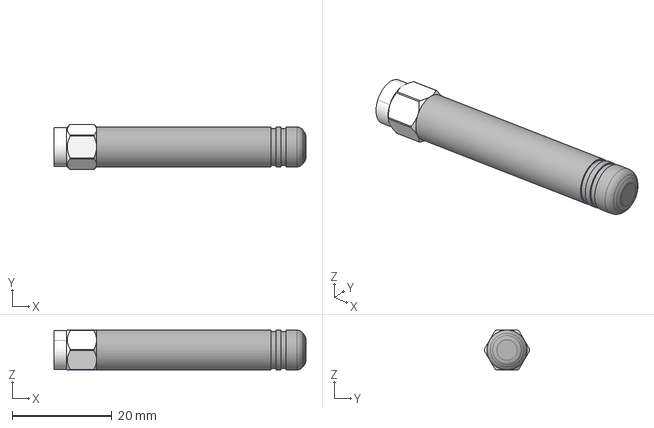
[picture p119: CAD file, 2024-06-07]
3D/Antenna/GSM_ANTENNA_42mm.stp
50.5 x 9.10 x 8.00 mm
