Kampi/KiCad/3D/Battery/CR2477.stp

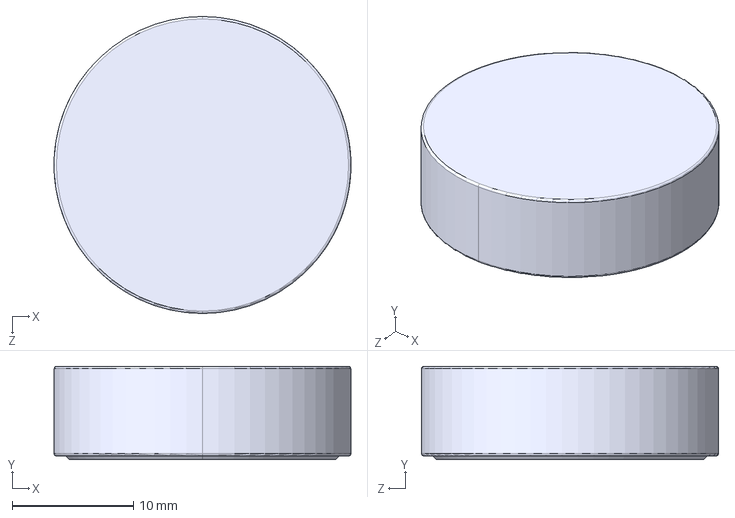
[picture p120: CAD file, 2026-01-24]
3D/Battery/CR2477.stp
24.5 x 7.70 x 24.5 mm
