Kampi/KiCad/3D/Batteryholder/Keystone/53.stp

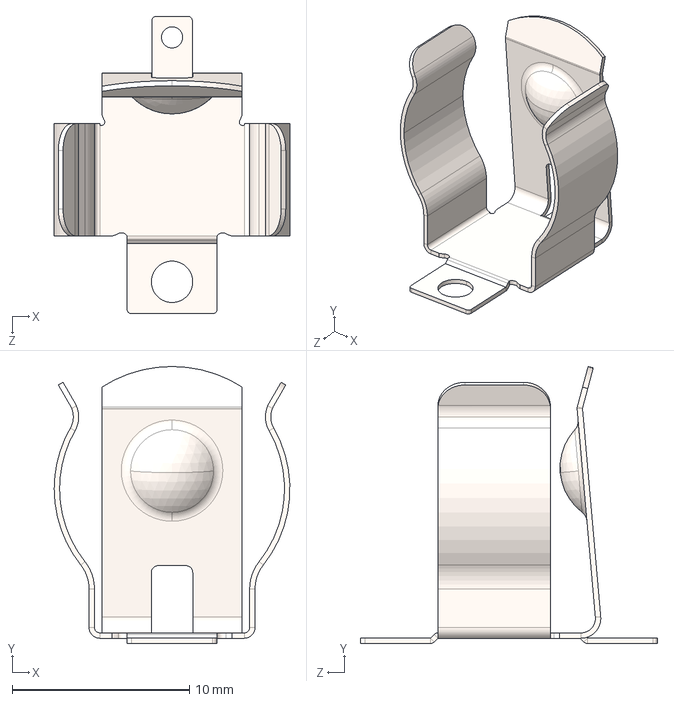
[picture p121: CAD file, 2021-08-19]
3D/Batteryholder/Keystone/53.stp
13.3 x 15.6 x 16.8 mm
