Kampi/KiCad/3D/Bivar/SLP3-300-100-R.stp

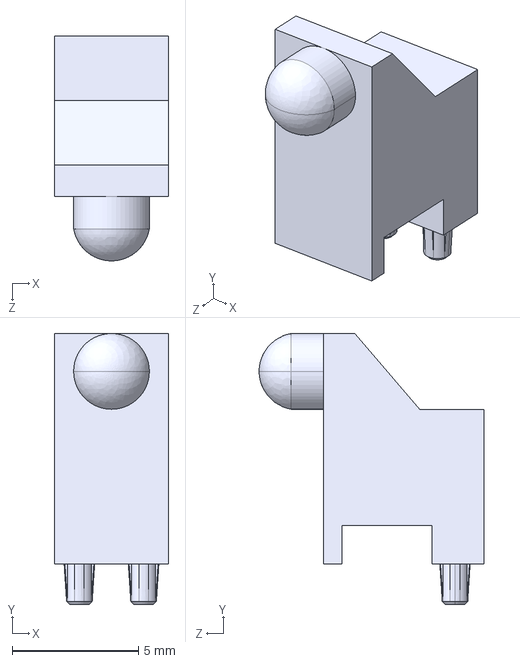
[picture p122: CAD file, 2026-05-26]
3D/Bivar/SLP3-300-100-R.stp
4.52 x 10.7 x 8.89 mm
