Kampi/KiCad/3D/C&K/KMR211GLFS.stp

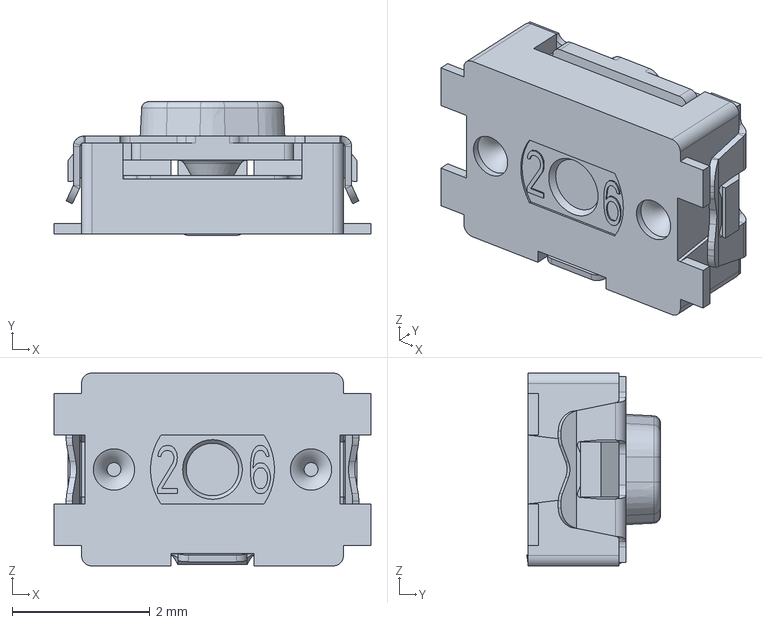
[picture p123: CAD file, 2022-05-29]
3D/C&K/KMR211GLFS.stp
4.60 x 1.94 x 2.80 mm
