Kampi/KiCad/3D/Connector_254/Pin Header 2x11 TH Pitch 2.54mm.stp

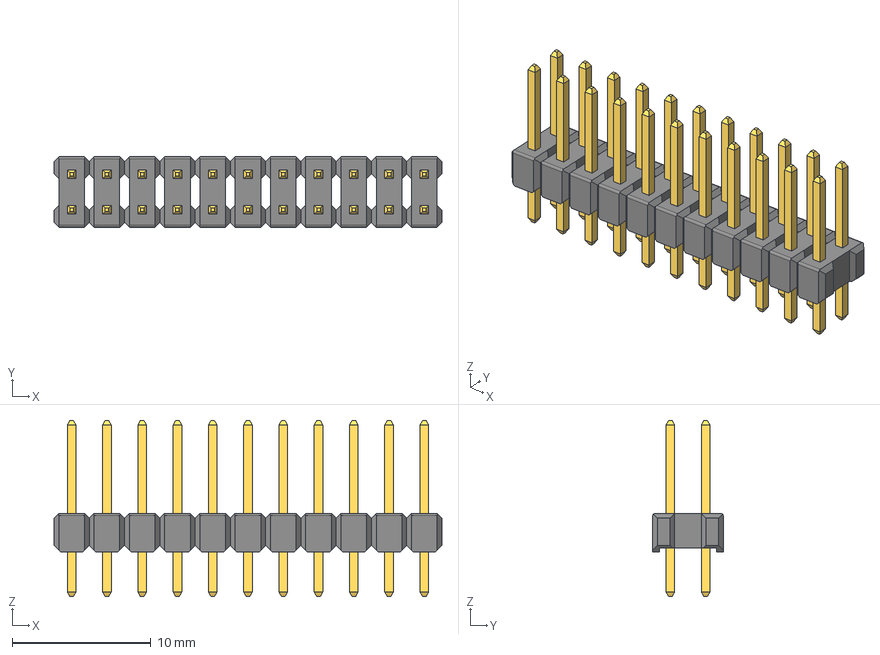
[picture p124: CAD file, 2020-01-17]
3D/Connector_254/Pin Header 2x11 TH Pitch 2.54mm.stp
27.9 x 5.08 x 12.7 mm
