Kampi/KiCad/3D/Connector_254/preci-dip/8fm-78-0004-02-146.stp

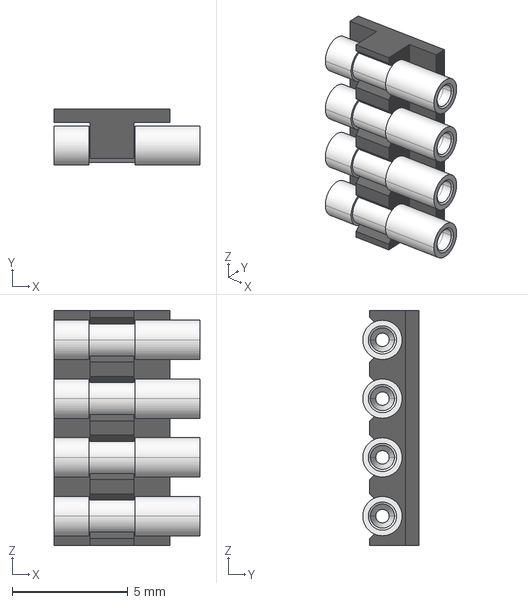
[picture p125: CAD file, 2020-06-16]
3D/Connector_254/preci-dip/8fm-78-0004-02-146.stp
6.30 x 2.44 x 10.2 mm
