Kampi/KiCad/3D/Connector_JST/S3B-PH-SM4-TB.stp

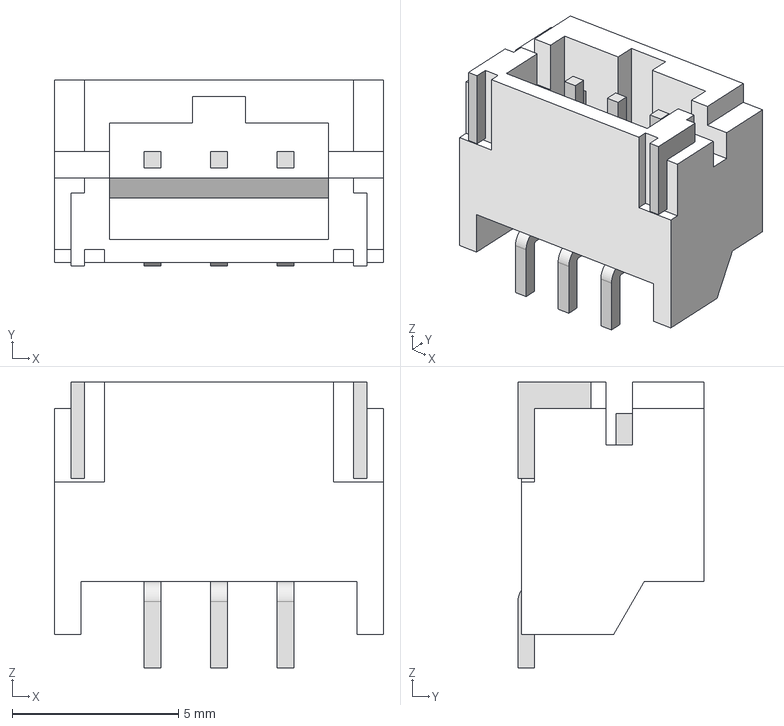
[picture p126: CAD file, 2020-05-12]
3D/Connector_JST/S3B-PH-SM4-TB.stp
9.90 x 5.60 x 8.60 mm
