Kampi/KiCad/3D/Connector_Phoenix/PhoenixContact_MSTBA_2,5_18-G-5,08_1x18_P5.08mm_Horizontal.stp

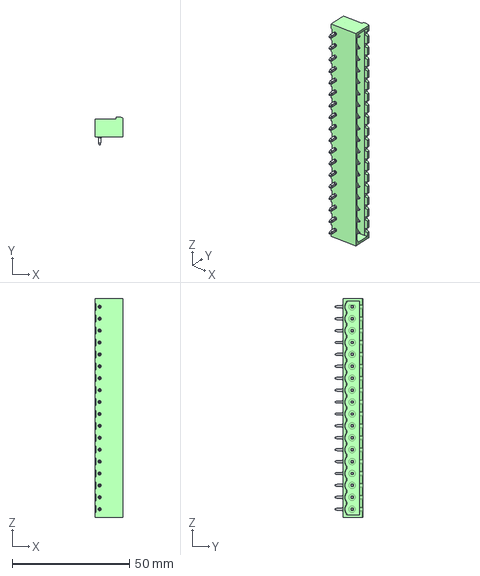
[picture p127: CAD file, 2020-06-03]
3D/Connector_Phoenix/PhoenixContact_MSTBA_2,5_18-G-5,08_1x18_P5.08mm_Horizontal.stp
12.0 x 12.1 x 93.4 mm
