Kampi/KiCad/3D/Connector_TE/2-2172067-2.stp

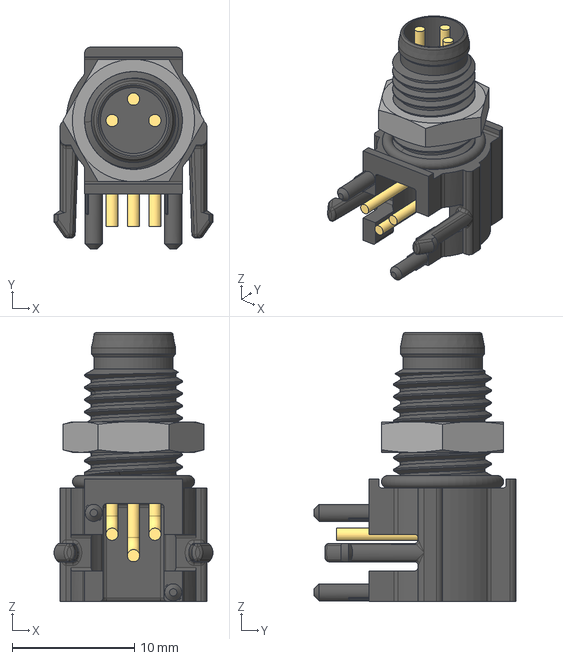
[picture p128: CAD file, 2020-05-14]
3D/Connector_TE/2-2172067-2.stp
13.0 x 16.5 x 22.0 mm
