Kampi/KiCad/3D/Connector_USB/GCT/USB1061-GF-L-A.stp

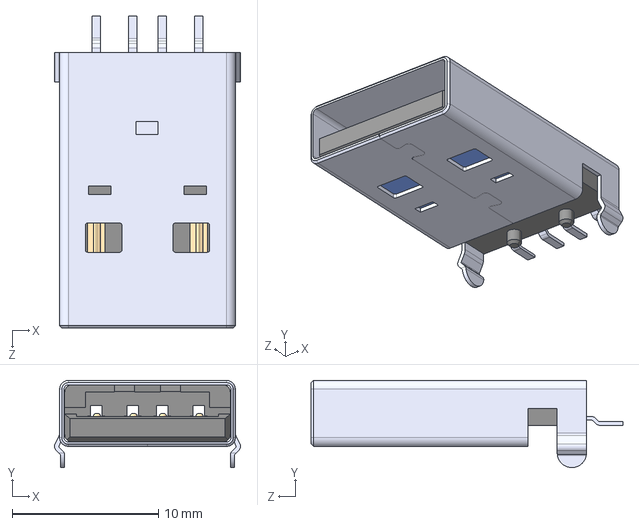
[picture p129: CAD file, 2024-06-07]
3D/Connector_USB/GCT/USB1061-GF-L-A.stp
12.7 x 5.95 x 21.3 mm
