Kampi/KiCad/3D/Cree/QLS6B-FKW-CNSNSF043.stp

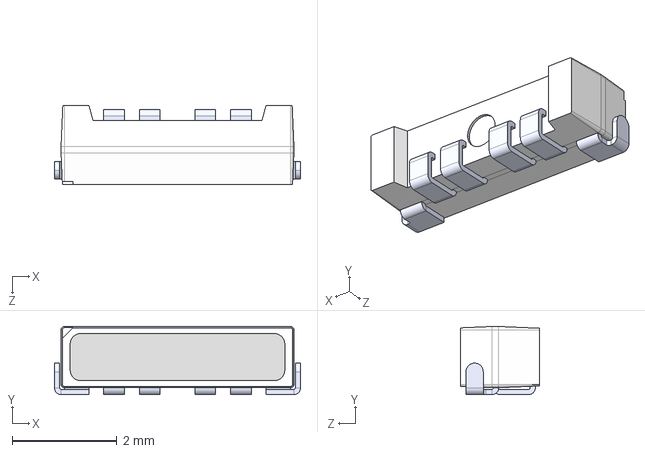
[picture p130: CAD file, 2022-07-31]
3D/Cree/QLS6B-FKW-CNSNSF043.stp
4.70 x 1.30 x 1.50 mm
