Kampi/KiCad/3D/Crystal/2012.stp

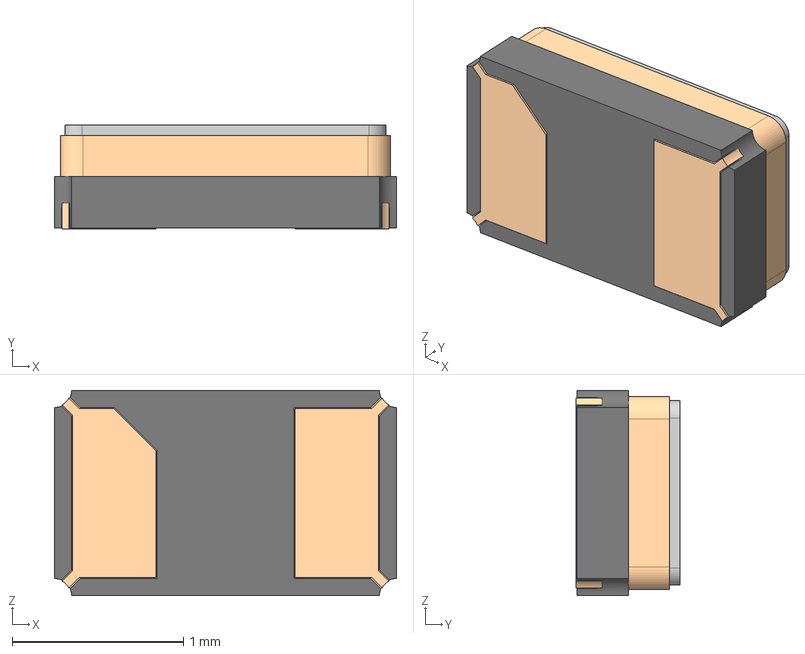
[picture p131: CAD file, 2024-06-08]
3D/Crystal/2012.stp
2.00 x 0.606 x 1.20 mm
