Kampi/KiCad/3D/DevBoards/Digilent/PmodI2S2.stp

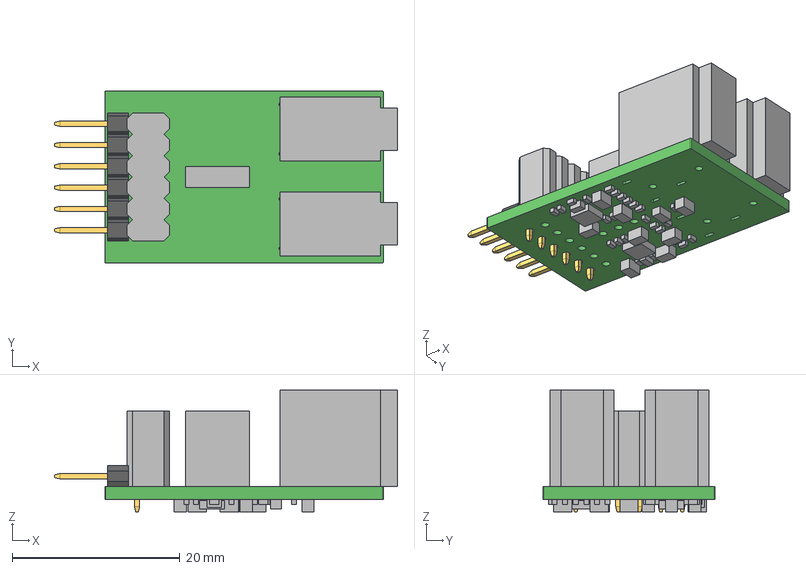
[picture p132: CAD file, 2020-05-05]
3D/DevBoards/Digilent/PmodI2S2.stp
40.9 x 20.5 x 14.5 mm
Board
Extruded x 42
ConnectorHeader_1x6PMOD_Plastic
ConnectorHeader_1x6PMOD_Pins
