Kampi/KiCad/3D/Display/SevenSegment/Kingbright/SX18-11.stp

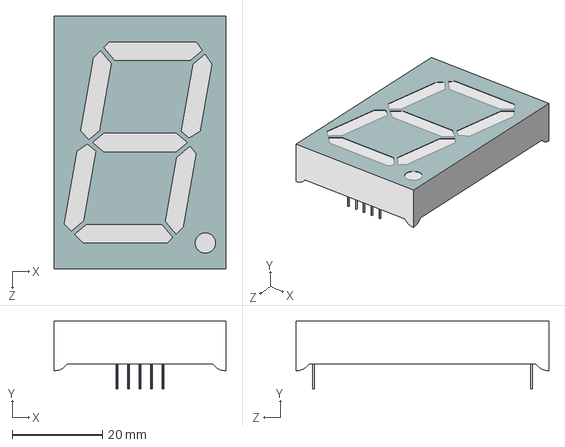
[picture p133: CAD file, 2020-06-30]
3D/Display/SevenSegment/Kingbright/SX18-11.stp
38.0 x 15.0 x 56.0 mm
