Kampi/KiCad/3D/E-Switch/JS5208.stp

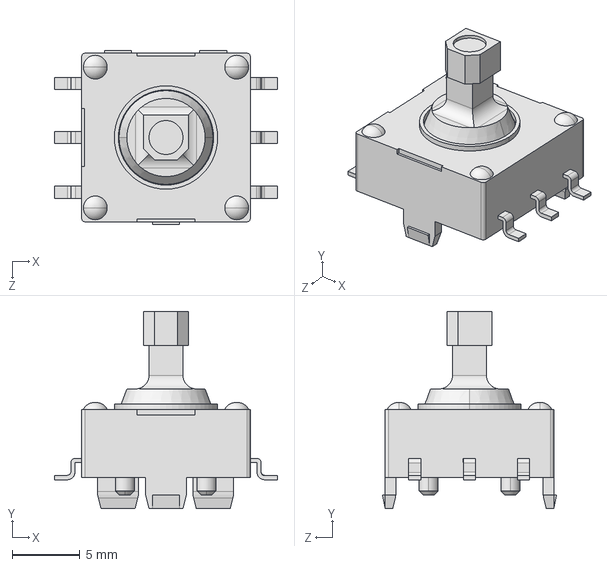
[picture p134: CAD file, 2026-01-24]
3D/E-Switch/JS5208.stp
16.4 x 14.5 x 12.8 mm
