Kampi/KiCad/3D/ECS/ECS-.327-6-1210-TR.stp

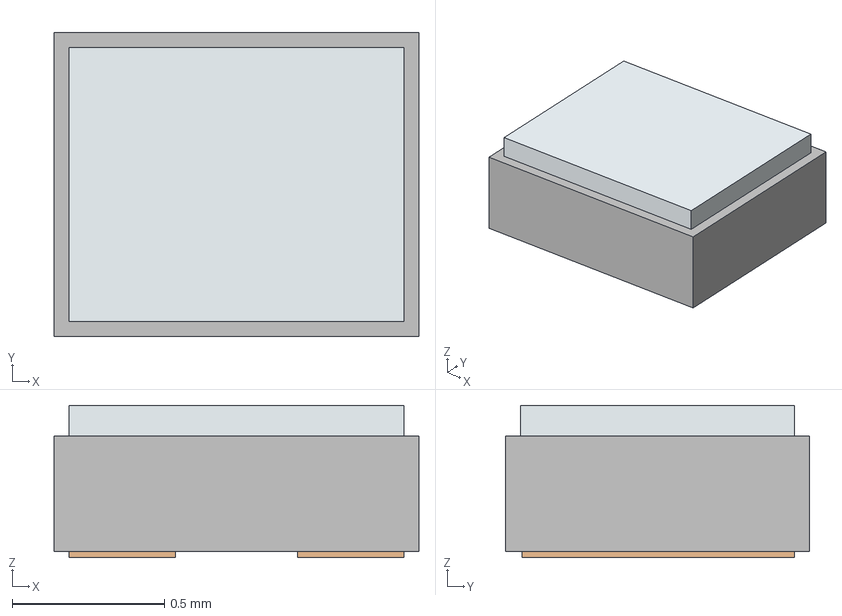
[picture p135: CAD file, 2026-01-24]
3D/ECS/ECS-.327-6-1210-TR.stp
1.20 x 1.00 x 0.5 mm
solidBody
solidTop1
solidLead
