Kampi/KiCad/3D/Espressif/ESP8266-ESP07.stp

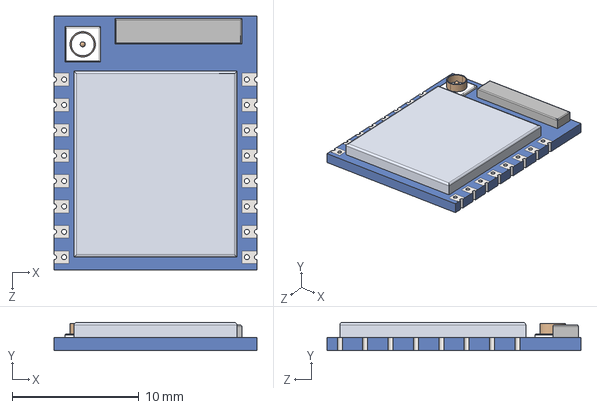
[picture p136: CAD file, 2021-09-12]
3D/Espressif/ESP8266-ESP07.stp
16.0 x 2.21 x 20.0 mm
