Kampi/KiCad/3D/Fanstel/BT40E.stp

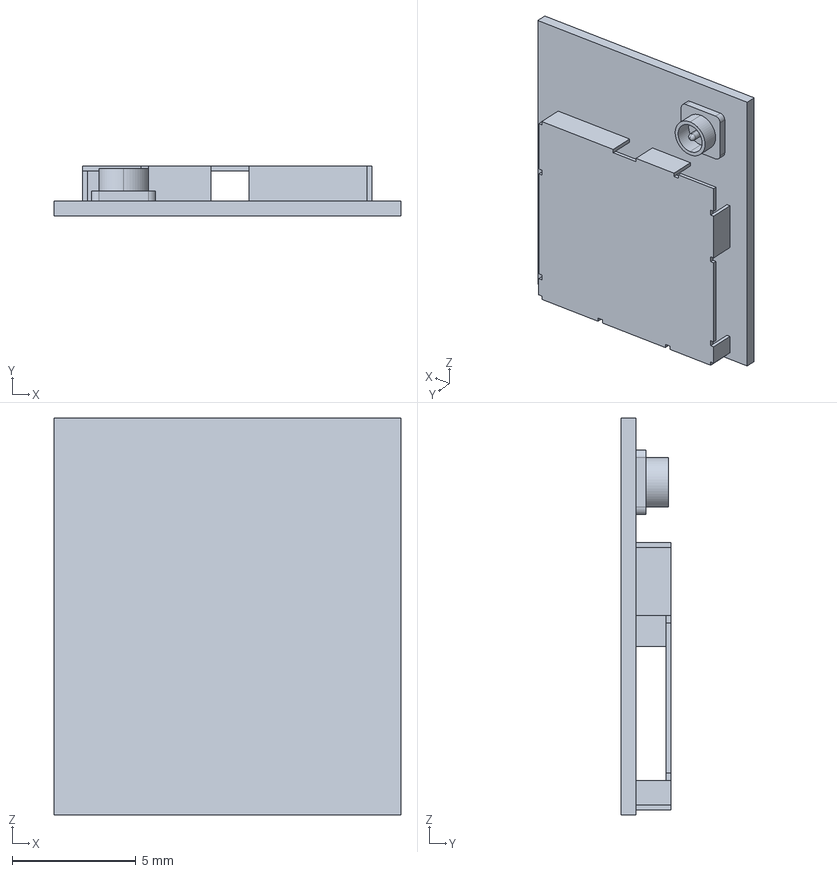
[picture p137: CAD file, 2026-06-25]
3D/Fanstel/BT40E.stp
14.0 x 2.00 x 16.0 mm
