Kampi/KiCad/3D/Fuse/2920.stp

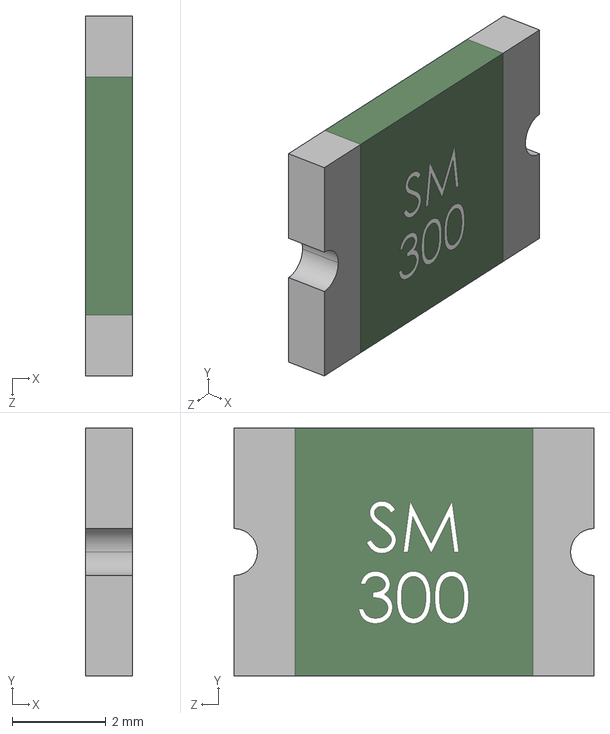
[picture p138: CAD file, 2026-01-24]
3D/Fuse/2920.stp
1.00 x 5.30 x 7.70 mm
