Kampi/KiCad/3D/GCT/BD125-10-A-0305-0580-L-B.stp

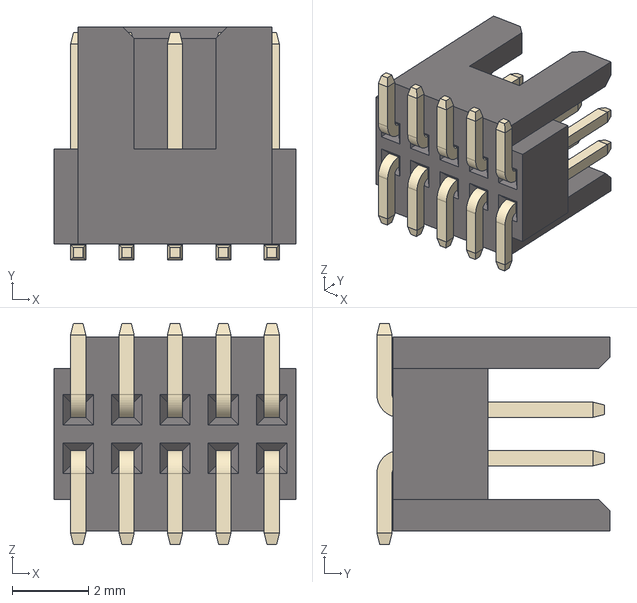
[picture p139: CAD file, 2026-01-24]
3D/GCT/BD125-10-A-0305-0580-L-B.stp
6.35 x 6.12 x 5.80 mm
BD125-10-A-0305-0580-L-B_H
BD125-10-A-0305-0580-L-B_P x 10
