Kampi/KiCad/3D/Hirose/FH19C-8S-0.5SH.stp

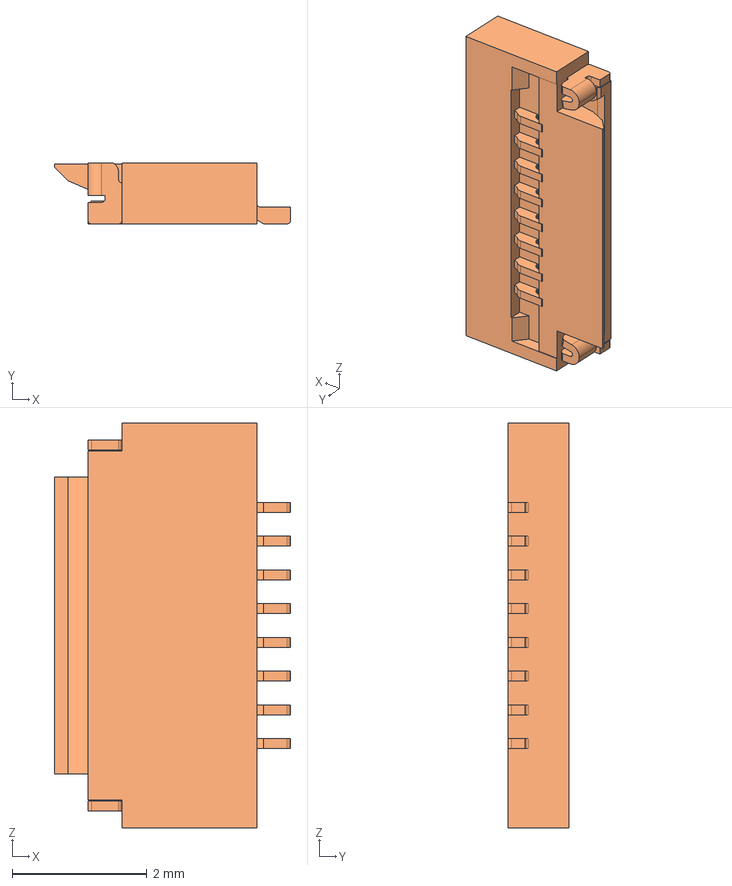
[picture p140: CAD file, 2024-06-07]
3D/Hirose/FH19C-8S-0.5SH.stp
3.50 x 0.9 x 6.00 mm
