Kampi/KiCad/3D/Ignion/NN02-201.stp

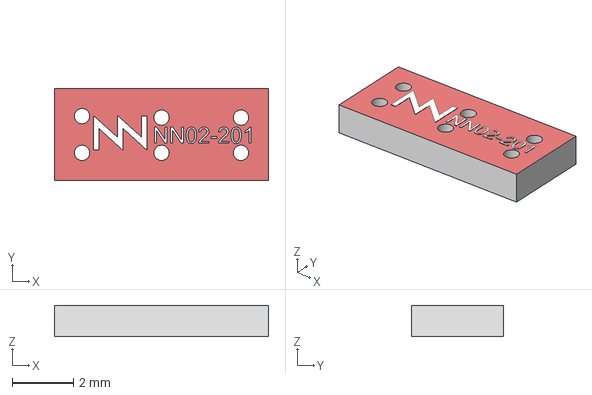
[picture p141: CAD file, 2023-05-01]
3D/Ignion/NN02-201.stp
7.00 x 3.00 x 1.02 mm
