Kampi/KiCad/3D/Inductor/Taiyo Yuden/NRS5030.stp

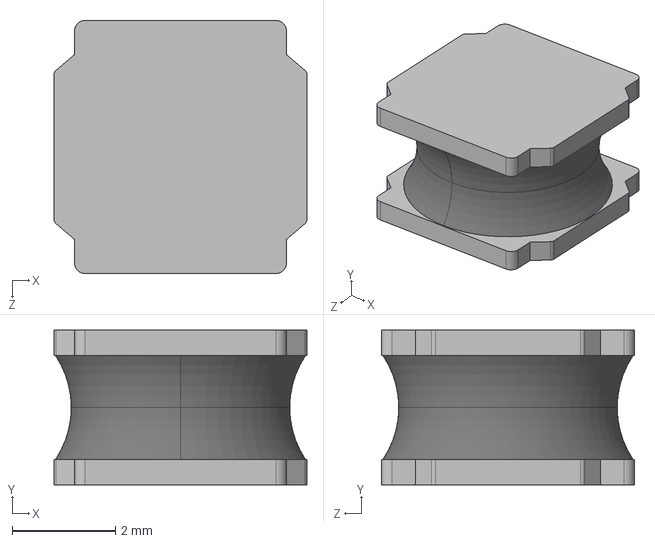
[picture p142: CAD file, 2020-07-30]
3D/Inductor/Taiyo Yuden/NRS5030.stp
4.90 x 3.00 x 4.90 mm
