Kampi/KiCad/3D/Infineon/ESD131B1W0201E6327XTSA1.stp

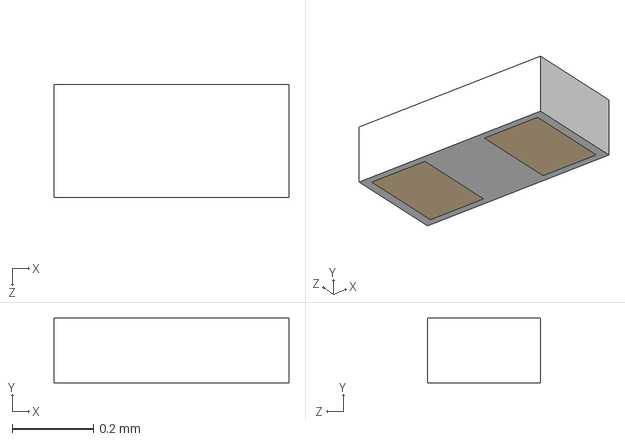
[picture p143: CAD file, 2024-06-08]
3D/Infineon/ESD131B1W0201E6327XTSA1.stp
0.58 x 0.16 x 0.28 mm
