Kampi/KiCad/3D/JST/S2B-PH-SM4-TB.stp

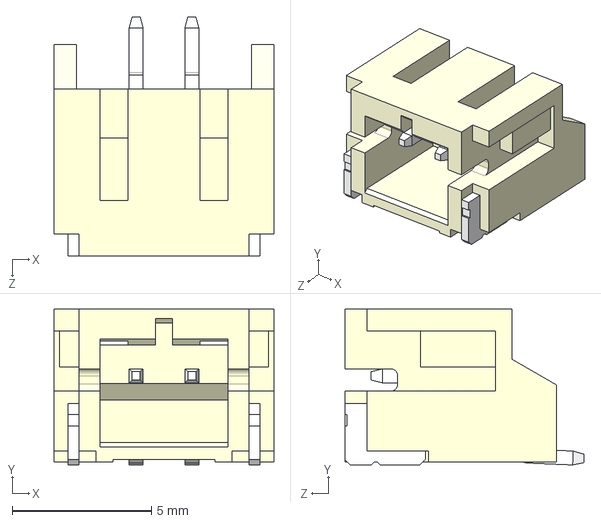
[picture p144: CAD file, 2026-01-24]
3D/JST/S2B-PH-SM4-TB.stp
7.90 x 5.60 x 8.60 mm
